saschapo/smartlada/VAZ2106_Smart_Lamp_Context.md

# Умный светильник из заднего фонаря ВАЗ-2106 — контекст проекта

> Хэндофф-документ для будущих сессий. Фиксирует все технические решения, их обоснование и открытые вопросы.
> Формат: **[Ф]** факт · **[В]** вывод · **[Г]** гипотеза/оценка · **[Р]** решение проекта.

## 1. Идея

Из штатного заднего фонаря ВАЗ-2106 сделать домашний умный светильник:
управление голосом через Алису (есть **Яндекс Станция Миди**), мозг — ESP32,
4 секции фонаря диммируются независимо. В кадре снимать НЕ планируется
(строб-эффект от камеры не учитываем; для глаза мерцание убрать всё равно нужно).

## 2. Донор — фонарь ВАЗ-2106

- Деталь: **«фонарь в сборе 2106-3716011»** (левый) / корпус **2106-3716041**.
- **[Ф] Корпус пластиковый, разделён на 5 секций**; рассеиватель цветной, тоже 5 частей:
  1. указатель поворота (жёлтый, крайний наружный),
  2. габарит (красный),
  3. фонарь заднего хода (прозрачный/белый),
  4. стоп-сигнал (красный, крайний внутренний),
  5. подсветка номера (чёрный внутренний выступ).
  Средняя верхняя секция — без лампы.
- **[Р] Используем только 4 секции** (поворот, габарит, задний ход, стоп).
  Подсветку номера НЕ задействуем.
- **[Ф] Поправка к ранней гипотезе:** в 2106 габарит и стоп — РАЗНЫЕ секции с
  отдельными однонитевыми лампами, а НЕ двухнитевая P21/5W «две в одной».
  Значит эффект «габарит тускло / стоп ярко» = просто два независимых PWM-канала
  на две красные секции.
- **[Ф] Задняя часть фонаря штатно ОТКРЫТА** (вставлялся в кузов, лампы — из
  багажника через плату патронов). Поэтому «задняя крышка» = закрыть открытую
  полость по периметру, а не повторять кривую кромку.

## 3. Протокол / интеграция с Алисой

- **[Р] Zigbee, ESP32-C6, прямая привязка к Станции Миди** как несколько
  dimmable-light эндпоинтов (по одному на секцию → каждая = отдельная «лампа»
  в приложении «Дом с Алисой», управляется голосом раздельно).
- **[Ф] Обоснование:** Миди — встроенный Zigbee-координатор; тип «лампа» —
  самый богатый и лучше всего поддерживаемый; работает без сервера, без облака,
  без Wi-Fi-прослойки, без роутера. On/Off + Level Control (яркость) поддержаны.
- **[Ф] Ограничения Яндекса:** нет RGB/сцен для ламп (не нужно — цвет дают
  физические рассеиватели); Zigbee end-device привязывается только к ОДНОМУ
  координатору (Миди ИЛИ Home Assistant, не оба сразу).
- **[Г] Незакрытый риск:** встанет ли самодельное Zigbee-устройство со
  стандартными кластерами (On/Off + Level Control) в Миди «чисто», и приедет ли
  яркость в интерфейс Алисы. Вероятность высокая. ПРОВЕРИТЬ НА ПРОТОТИПЕ ПЕРВЫМ ДЕЛОМ.
- **Отвергнутые альтернативы:**
  - Matter over Wi-Fi — рабочий не-Zigbee вариант (Миди — Matter-коммиссионер,
    работает на ESP32 через esp-matter), но требует живого роутера + риск с
    тестовым сертификатом аттестации (DAC). Отклонён в пользу Zigbee.
  - Wi-Fi + Home Assistant / своё облако / Tuya-эмуляция — больше инфраструктуры.
- **[Ф] Классический ESP32 (WROOM) и ESP8266 Zigbee НЕ умеют** (нет радио 802.15.4).

## 4. Мозг (MCU)

- **[Р] Финал: ESP32-C6** (радио 802.15.4 + Wi-Fi/BLE). Рекомендуемые платы:
  `ESP32-C6-DevKitC-1` (8 МБ flash, удобно для отладки) для прототипа;
  `Seeed XIAO ESP32-C6` (внешняя антенна u.FL) для компактного финала.
- **[Р] Для стартового стенда — имеющийся ESP8266 HW-365A.** Годится ТОЛЬКО для
  bring-up световой части (плата MOSFET + диоды + PWM + плавность диммирования),
  т.к. это не зависит от радио. Zigbee/Алису на нём проверить НЕЛЬЗЯ.
  PWM-API отличается от C6 (`analogWrite` vs `ledcAttach`/`ledcWrite`).
- **[Р] Антенна:** корпус пластиковый (RF проходит — хорошо). НЕ размещать
  фольгу/металлический теплоотвод рядом с антенной C6.

## 5. Силовая часть — плата MOSFET

- **[Р] Выбрана 4-канальная плата на базе D4184 с опторазвязкой (PC817).**
  (Ozon, ~232 ₽, «Четырёхканальный MOSFET-модуль с оптопарной изоляцией».)
- **[Ф] Почему годится от 3.3 В:** затвор смещается от напряжения НАГРУЗКИ через
  оптопару, поэтому 3.3 В на входе открывают ключ так же полно, как 5 В.
  Проблема «logic-level» тут решена схемотехникой. Отменяет идею паять дискретные
  MOSFET-каналы.
- **[Ф] MOSFET:** AOD4184, Rds(on) ~8.5 мОм, 40 В / ~10 А (запас огромный).
- **Распиновка / подключение:**
  - Вход: `PWM1..4` → GPIO МК; `GND1..4` → земля МК.
  - Выход: `Power+ / Power−` → 12 В; диод между `OUTx+` и `OUTx−`
    (анод → `OUTx+`, катод → `OUTx−`; ПРОЗВОНИТЬ, что `OUTx+` = `Power+`).
  - Активный HIGH (duty PWM = яркость, без инверсии).
  - Флайбек-диод не нужен (нагрузка не индуктивная).
- **[Р] Частота PWM: старт ~500 Гц–1 кГц.** Оптопара смазывает фронты на высокой
  частоте. ПРОВЕРИТЬ плавность диммирования, особенно на низкой яркости.
  Заложить гамма-коррекцию (~2.2) при маппинге яркости Алисы 0–100 % в duty.
- **[Ф] Земли сигнала и нагрузки на плате развязаны.** Для реальной развязки —
  МК и 12 В от разных источников, земли не соединять. Общая земля — тоже работает,
  но развязка номинальная.
- **[Г] Fallback:** если плавность PWM разочарует — non-isolated logic-level
  MOSFET (напр. IRLB8721 для прототипа TO-220 / AO3400 SMD для финала),
  4× LEDC → 4× MOSFET напрямую.
- **Отвергнуто:** PCA9685 / I2C-серво-плата (для 4 каналов избыточно; это
  генератор сигнала, не силовой ключ).

## 6. Питание

- **[Р] Рабочее напряжение диодов — 12 В** (5 В давало >2–4 А при мощных диодах;
  6 В нестандартно для PD → отброшено; 9 В рассматривалось, финально 12 В).
- **[Ф] 12 В в USB-PD — опциональный/негарантированный профиль** (стандартные
  фиксированные: 5/9/15/20 В).
- **[Р] Источник 12 В:**
  - Прототип: обычный 12 В adapter (barrel) или лабораторник (исключить PD из
    переменных отладки).
  - Финал: PD-триггер **20 В → buck → 12 В** (надёжно), либо PD-зарядка с
    подтверждённым 12 В в списке PDO.
  - Предохранитель на линии 12 В.
- **[Р] Питание МК:** на стенде — USB от компа; в финале — 12 В → buck 5 В.

## 7. Свет (LED)

- **[Р] Патроны выламываем, ставим свои диоды** (свобода по CRI/оптике/напряжению).
- **[Р] НЕ автомобильные LED-ретрофиты** (низкий CRI, конфликт с внешним PWM).
  Брать сырые модули/COB под прямое управление MOSFET-ом.
- **[Р] CRI важен только под прозрачной секцией заднего хода** (единственный
  «полезный» белый свет) → high-CRI 90+ белый 2700–3000K.
  За цветными секциями (стоп/габарит — красный, поворот — жёлтый) CRI не считается;
  эффективнее ЦВЕТНЫЕ диоды под цвет секции (белый за фильтром теряет ~половину потока).
- **[Р] Топология под 12 В:** строки диодов последовательно + ограничение тока.
  Для старта — модули со ВСТРОЕННЫМ ограничением тока (чтобы PWM-ить прямо
  MOSFET-ом и не спалить). Для мощных сырых LED (>1–2 А) — источник постоянного
  тока (CC-драйвер) на канал, PWM на его enable-вход (шаг 2).
- **[Р] Тепло:** даже LED в закрытом пластиковом корпусе греются — минимальный
  теплоотвод (алюминиевая подложка), особенно под задний ход на полной яркости.

## 8. Корпус / механика

- **[Р] Задняя панель-носитель, печать PETG** (LED холодные, но buck/PD греются;
  PETG надёжнее PLA).
- Панель держит: ESP32-C6, PD/buck, плату MOSFET, ввод питания; диоды — прямо
  в секции корпуса.
- **[Г] CAD:** сложность средняя — обмер периметра открытой полости + корыто со
  стойками; заложить допуск/уплотнитель (не press-fit по месту).

## 9. Итоговая архитектура (сводка)

```
[12 В источник] --Power+/-→ [4-ch D4184 opto MOSFET board]
                                   ↑ PWM1..4 / GND
[ESP32-C6] --4× LEDC (PWM)---------┘
   └─ Zigbee end-device (4× dimmable light) ──radio──→ [Яндекс Станция Миди] → Алиса

Каждый канал: OUTx+ (=12В) → LED-строка секции → OUTx- (ключ на землю)
Секции: 1 поворот(жёлт) · 2 габарит(красн) · 3 задний ход(бел,high-CRI) · 4 стоп(красн)
```

## 10. Открытые вопросы

1. Мощность белого под секцию заднего хода → определит, хватит ли
   токоограниченного модуля или нужен CC-драйвер.
2. Финальный способ получения 12 В (PD 20 В+buck vs 12 В-adapter vs verified-12V PD).
3. Точная плата C6 (DevKitC-1 для отладки → XIAO C6 для финала?).

## 11. Порядок работ (прототип → финал)

1. **[СТЕНД, можно сейчас на ESP8266]** ESP8266 + плата D4184 (1 канал) + 1 диод +
   12 В adapter. Проверить: коммутацию, плавность PWM-диммирования на 500 Гц–1 кГц,
   линейность на низкой яркости. Затем 4 канала.
2. **[РАДИО, на C6]** ESP32-C6 + 1 MOSFET-канал + 1 диод. Поднять Zigbee
   dimmable-light, привязать к Миди, убедиться, что ЯРКОСТЬ реально управляется
   из Алисы. ← снимает главный риск (примет ли Миди самоделку) ДО механики.
3. Полная электроника (4 канала), гамма-коррекция, heartbeat/reconnect-логика.
4. Свет: подбор диодов (high-CRI белый + цветные), теплоотвод.
5. Механика: обмер, CAD задней панели, печать PETG, сборка.

## 12. Профиль исполнителя (для контекста)

Программистский бэкграунд, активный embedded-хоббист (параллельный проект CineInk:
ESP32 + LoRa + e-ink). Работает в Arduino IDE, комментарии/ошибки — простым текстом.
Свободно RU/EN. Ценит формат peer-review: разделение факт/вывод/гипотеза, проверку
логики и скрытых допущений, отсутствие «воды».
