saschapo/smartlada/SmartLadaRevC/DEV_PLAN.md

# SmartLada Rev C — план разработки прошивки

Дата: 2026-09-04. Железо revC поднято и провалидировано (питание PD 12В + buck 3.3В, USB,
OLED, кнопки, I2C, 4 канала — гоняли 35 Вт реальной нагрузки, стабильно, ничего не греется).
LEDC зафиксирован на 10 бит (см. [[esp32c6-ledc-freq-ceiling]]).

Цель: свести в основную прошивку `SmartLadaRevC` сетевое управление (Zigbee + опц. WiFi/веб)
поверх существующего локального (OLED-меню + кнопки), с единой моделью состояния.

## Целевая архитектура

**Единый источник состояния — `config::s`** (mode, master, staticBri[4] + калибровка).
Все «писатели» правят его, луп не меняется:

```
loop: buttons -> menu -> [zigbee/wifi callbacks уже записали config::s]
      fx::compute(mode, now, master, staticBri, out[4])   // компоновщик
      channels::write(now, out)                            // slew -> gamma -> LEDC
      menu::render()
```

Писатели состояния: **меню (кнопки), Zigbee, WiFi/веб.** Приоритет — **last-writer-wins**.
Двусторонняя синхра: изменил меню → репорт в Zigbee-атрибуты (и в веб); пришло из Zigbee/веб →
дёрнуть `menu::render()`. `fx::compute` уже делает компоновку (Static→поканально×master,
анимация→кадр×master), поэтому компоновщик из `RevCZigbeeFx` схлопывается в существующий `fx`.

## Zigbee-модель (архитектура подтверждена, см. research/smartlada_zigbee_effects_plan.md)

Один узел = 5 эндпоинтов (EP = логическое под-устройство; Станция видит их как 5 устройств):

| EP | Тип | Роль |
|----|-----|---|
| 10..13 | `ZigbeeDimmableLight` | 4 лампы (Turn/Marker/Reverse/Stop): on/off + level |
| 14 | `ZigbeeColorDimmableLight` «Fara» | слой эффектов: hue=**селектор эффекта**, level=**яркость эффекта** |

> **Правило приоритета ниже УСТАРЕЛО** (планировалось до реализации, дважды пересмотрено на
> железе). Действующая модель — в `README.md`, раздел «Compositor / control model». Коротко:
> `mode` один определяет слой; EP14 никогда не трогает `staticBri`; выкл и белый на EP14
> значат одно — эффектов нет; групповая и поканальная яркость целиком на EP10-13.
> Блок оставлен как история решения, а не как инструкция.

```
master = Fara.on ? Fara.level/254 : 1.0
Fara.on && насыщенный цвет  -> out[i] = кадр_эффекта[i] * master   (hue -> эффект)
иначе (Fara off/белый)      -> out[i] = лампа[i] * master           (PASSTHROUGH: EP10..13 индивидуально)
```

Готовая реализация всей этой логики (плоская, стендовая) — `sketches/RevCZigbeeFx/RevCZigbeeFx.ino`;
переносим в модуль. Build: `ZigbeeMode=ed, PartitionScheme=zigbee_8MB, FlashSize=16M, CDCOnBoot=cdc`.

## WiFi / веб-интерфейс (оставляем, стретч-цель)

Видение: управление и с телефона (веб), и Zigbee, и кнопками/OLED. Веб — в стиле **cineink**
(`/Users/saschapo/Documents/Documents/arduino/260518_cineink/cineink/`): подключение к WiFi по QR,
`smartlada.local` (mDNS) тоже по QR, тёмный `web_view/` (device.css/index.html/app.js).

**WiFi+Zigbee одновременно на C6:** железо умеет (один 2.4ГГц радиотракт, RF-coexistence /
тайм-слайсинг Wi-Fi6 ↔ 802.15.4). Риск — софт (Arduino: Zigbee-стек + WiFi + веб-сервер + LittleFS
+ OLED одновременно, менее обкатано; возможны потери/латентность). **Стратегия:** WiFi и Zigbee —
независимые модули, которые МОГУТ работать вместе, но с **переключателем в меню (WiFi ↔ Zigbee)** как
гарантированным fallback. Coexistence проверяем эмпирически.

## Решённые вопросы

1. Приоритет при одновременном управлении — **last-writer-wins** по `config::s`.
2. Скорость/яркость эффекта — **параметр меню** (Fara.level = master яркость; скорость — таймингами эффекта в меню).
3. Персист состояния в **NVS** — делаем. NVS в ESP-IDF с wear-leveling, на практике (cineink) не изнашивается;
   писать **с дебаунсом** (на «оседании» значения, не каждый кадр). Глянуть NVS/LittleFS-паттерн cineink.
4. Passthrough (Fara off → индивидуальные лампы) — **оставляем**.

## Железные дельты стенд→продукт (учесть в портировании)

| Стенд (nanoC6) | Продукт revC | Действие |
|---|---|---|
| статус NeoPixel **GPIO8** | **IO8 не разведён** | статус сети на **OLED** |
| factory-reset BOOT(GPIO9) | SW2=IO9 + пункт меню | оба |
| — | **PG=IO10** (12В есть, LOW), **VBUS=IO4** (ADC) | PD-gating (Фаза 4) |

## Фазы

- **Фаза 1 — билд/скелет. СДЕЛАНО.** Zigbee в билд `SmartLadaRevC` (FQBN выше). Проверить, что `config` NVS
  живёт под zigbee-партицией. Вынести Zigbee в `src/net/zigbee.{h,cpp}` (тонкий слой). RF-риск от
  пропущенного EPAD WROOM — проверяем бесплатно при первом паринге (LQI/дальность).
- **Фаза 2 — интеграция состояния. СДЕЛАНО** (report-back EP14 без цвета — см. README). Коллбэки Zigbee → `config::s`; изменения меню → report в Zigbee.
  `fx::compute` как компоновщик. Карта hue→индекс эффекта (общая для hue-коллбэка и пункта «Mode»).
- **Фаза 3 — меню под сеть. ЧАСТИЧНО:** экран Zigbee (статус/PAN/LQI/re-pair) есть,
  WiFi-пункт заглушка, переключателя WiFi<->Zigbee нет. **Планировалось:** Пункты `WiFi`/`WiFi QR` **оставить/доразвить** (провижн по QR, smartlada.local).
  Добавить «Zigbee» (статус joined/PAN/LQI, Pair/Re-pair) и переключатель **WiFi ↔ Zigbee**.
  Статус сети на OLED (вместо NeoPixel). Factory-reset расширить на `Zigbee.factoryReset()`.
- **Фаза 4 — PD-gating + debug-байпас. СДЕЛАНО 2026-09-05.** Гейтинг по **VBUS(IO4 ADC)** с
  гистерезисом (нет ~12В → каналы в 0 + «NO 12V» на idle) — VBUS надёжнее, чем PG, и не «блэкаутит»
  ложно на реальных 12В. Пункт меню **Settings → Force Out (on/off)** — байпас гейтинга для дебага по
  индикаторным LED на 5В без ламп. VBUS/PG/temp видны в Info. (PG=IO10 читается, показывается.)
- **Фаза 5 — эффекты. СДЕЛАНО** (Breathe/Turn/Chase/Fade/Drive). 2-3 стартовых (blink/chase/fade уже есть) на движок `fx::`; hue→эффект.
- **Фаза 6 — WiFi/веб + персист. ЧАСТИЧНО:** NVS-персист с дебаунсом сделан
  (`config::tick`, restore при подаче питания); WiFi и веб-UI отложены сознательно. Веб-UI из cineink (dark view, QR-провижн, mDNS). NVS-персист
  состояния ламп с дебаунсом. Имена/rejoin (T-пункты чеклиста research/).

## Риски

- **RF с пропущенным EPAD WROOM** — держим в голове, проверяем при первом паринге.
- **WiFi+Zigbee coexistence** на C6 под Arduino — главный софт-риск; fallback = переключатель в меню.
- Гетерогенный Zigbee-узел (4×0x0101 + 1×0x0102) — приёмка Станцией (чеклист research/, T3).
- `config` NVS под zigbee-партицией; рост прошивки (16М флеш — запас есть).

## Референсы

- Архитектура Zigbee: `research/smartlada_zigbee_effects_plan.md`, `.../multi_endpoint_summary.md`,
  результаты стенда `research/zigbee_alice_test_results.md`.
- Готовый Zigbee-код: `sketches/RevCZigbeeFx/RevCZigbeeFx.ino` (+ `RevCZigbee4EP` — 4 лампы, вариант A).
- Веб/NVS/лог: cineink `/Users/saschapo/Documents/Documents/arduino/260518_cineink/cineink/`
  (`web_view/`, `firmware/cineink/{web,log,rtc}.cpp`).
- Pin-map ground truth: `README.md`.
