saschapo/smartlada/custom_pcb/smartlada_custom_pcb_kicad.md

# SmartLada C6 — план кастомной платы в KiCad

> **УСТАРЕЛО — исторический документ.** Это первоначальный набросок, написанный до
> начала проектирования. Rev A пошла другим путём: не интеграция модуля
> ESP32-C6-WROOM-1, а **плата-носитель 80 x 65 мм**, к которой девборда подключается
> соплями через 8-контактный J3 (без сокетов и без резерва под неё). Отпали также TVS,
> ESD, ADS1115, NTC и 5 В rail.
>
> Актуальные документы:
> - **[KICAD_WORKFLOW.md](KICAD_WORKFLOW.md)** — точка входа: состояние, что дальше
> - [smartlada_rev_a_bom_netlist.md](smartlada_revA/smartlada_rev_a_bom_netlist.md) — спецификация Rev A
>
> Этот файл сохранён ради раздела 8 (замысел ревизий A/B/C) и списка того, что
> сознательно не делается.

## 1. Назначение платы

Кастомная плата должна заменить связку:

- ESP32-C6 devboard;
- 4-канальный модуль D4184;
- внешнюю разводку питания и управляющих сигналов.

Целевая функция: четыре независимых низковольтных PWM-канала для ламп R10W 12 V, Zigbee, локальная кнопка, индикация и сервисный USB.

Расчетная постоянная нагрузка: около 40 W / 3.33 A при 12 V. Холодный ток ламп кратковременно значительно выше, поэтому силовая часть должна проектироваться по пусковым токам, а не только по номинальным 0.83 A на канал.

---

## 2. Рекомендуемая блок-схема

```text
12 V IN
  ├─ предохранитель
  ├─ защита от переполюсовки
  ├─ TVS (только если питание может быть «грязным»)
  ├─ 12 V BUS ──> 4 × лампа ──> 4 × low-side MOSFET
  └─ DC/DC 12→3.3 V ──> ESP32-C6-WROOM-1
                         ├─ Zigbee
                         ├─ USB-C
                         ├─ BOOT / RESET
                         ├─ status LED / NeoPixel
                         ├─ NTC inputs
                         └─ PWM GPIO0…3
```

---

## 3. Обязательные узлы

### 3.1 ESP32-C6

Использовать модуль **ESP32-C6-WROOM-1**, а не голый чип.

Почему:

- встроены flash, кварц и RF-согласование;
- существенно проще трассировка;
- меньше риск ошибок в первой плате;
- доступны официальные symbol, footprint и 3D-модель Espressif для KiCad.

Выбирать объем flash под фактическую прошивку. Для текущего проекта 16 MB дает запас, но не является обязательным технически.

Обязательные элементы вокруг модуля:

- локальные развязывающие конденсаторы по reference design;
- EN pull-up и RC-цепь reset;
- BOOT-кнопка на GPIO9;
- RESET-кнопка на EN;
- тестовые площадки UART/USB/GND/3V3;
- RF keepout под антенной модуля.

### 3.2 Питание логики

Для стационарного источника 12 V использовать DC/DC-преобразователь **12→3.3 V** минимум на 0.8–1 A пикового тока.

Предпочтительно:

- синхронный buck;
- высокий КПД;
- рабочий вход минимум 16–18 V;
- корректная работа при импульсной нагрузке Wi‑Fi/Zigbee.

Отдельный промежуточный 5 V rail не нужен, если на плате нет 5-вольтовых узлов.

Если USB-C должен одновременно питать и программировать плату, необходимо заранее выбрать архитектуру:

1. USB питает только ESP32 при отключенных 12 V;
2. USB и 12 V объединяются через power mux / ideal-diode OR;
3. USB используется только как data, а плата всегда питается от 12 V.

Для первой ревизии безопаснее вариант 1 или 3. Нельзя напрямую соединять 5 V USB с выходом 3.3-вольтового преобразователя.

### 3.3 USB-C

Нужны:

- разъем USB-C USB 2.0;
- два резистора 5.1 kΩ на CC1/CC2;
- ESD-защита D+/D−;
- трассировка D+/D− как дифференциальной пары;
- при необходимости — последовательные резисторы по reference design Espressif.

USB нужен для прошивки, логов и восстановления устройства. Отдельный USB-UART мост для ESP32-C6 обычно не нужен: можно использовать native USB.

### 3.4 Четыре MOSFET-канала

Вместо модуля D4184 использовать четыре дискретных logic-level N-MOSFET в low-side включении.

Для каждого канала:

- MOSFET с низким RDS(on) при 3.3 V gate drive;
- gate resistor примерно 22–100 Ω;
- gate pulldown примерно 47–100 kΩ;
- широкая силовая дорожка;
- отдельный выход на лампу;
- общий силовой GND;
- контрольная точка затвора;
- запас по току и рассеиваемой мощности.

Лампы накаливания не являются индуктивной нагрузкой, поэтому flyback-диоды не обязательны. Однако посадочное место под TVS или RC-snubber можно предусмотреть как DNP для борьбы с выбросами и EMI.

MOSFET выбирать не только по максимальному току из datasheet. Критичны:

- RDS(on) именно при VGS = 2.5–3.3 V;
- корпус и теплоотвод;
- SOA при холодном пуске лампы;
- реальная температура платы.

### 3.5 Вход 12 V и предохранитель

Обязательны:

- входной разъем с запасом по току;
- общий предохранитель около T4A для текущей нагрузки;
- защита от переполюсовки.

Если плата питается только от регулируемого Ecola B2L080ESB в помещении, автомобильная защита от load dump не обязательна.

Если плата когда-либо будет подключаться к бортовой сети автомобиля, нужно добавить отдельный automotive front-end:

- TVS, рассчитанный на автомобильные импульсы;
- защита от reverse battery;
- фильтр;
- DC/DC с соответствующим входным диапазоном;
- проверка по ISO 7637-2 / ISO 16750.

Это другая категория питания; нельзя считать обычный 12-вольтовый LED-БП эквивалентом автомобильной сети.

---

## 4. Полезные опциональные узлы

### NTC температуры

Добавить два входа:

- NTC силовой части / MOSFET;
- NTC корпуса фонаря или блока питания.

Для каждого:

- NTC 10 kΩ;
- резистивный делитель;
- RC-фильтр;
- ADC-вход;
- разъем или посадочное место для проводного датчика.

Это полезнее, чем цифровые 3-проводные датчики, если требуется просто защита от перегрева.

### Измерение напряжения 12 V

Резистивный делитель на ADC позволяет:

- обнаруживать просадку блока питания;
- логировать аварии;
- отключать анимации при нестабильном питании.

### Измерение тока

Не обязательно для первой платы.

Варианты:

- один общий шунт на весь 12 V BUS;
- четыре отдельных low-side/high-side current sense канала.

Поканальный контроль существенно усложняет силовую землю и разводку. Добавлять его стоит только при реальной задаче диагностики перегоревшей лампы или заклинившего канала.

### Status LED

NeoPixel можно оставить, если он уже участвует в UX.

Если нужен минимализм и надежность, заменить его на:

- один обычный RGB LED;
- либо два одноцветных LED.

NeoPixel добавляет импульсное потребление и программную зависимость, но для одного индикатора это не критично.

---

## 5. Что убрать

Для текущей функции не нужны:

- LiPo charger и аккумулятор;
- RTC;
- SD-карта;
- PSRAM;
- CAN/LIN;
- USB-UART bridge;
- отдельный Wi‑Fi модуль;
- реле;
- flyback-диоды как обязательные компоненты;
- 5 V rail, если его не требуют внешние узлы.

CAN/LIN стоит добавлять только при переходе от автономного светильника к интеграции с автомобилем.

---

## 6. Рекомендуемые разъемы

Минимум:

- 12 V IN: 2 контакта;
- 4 × lamp output;
- общий lamp +12 V либо общий силовой разъем;
- 2 × NTC;
- USB-C;
- SWD/JTAG/UART test pads;
- BOOT/RESET;
- опциональный сервисный I²C header.

Для ламп предпочтительны разъемы с фиксацией и реальным токовым рейтингом, а не Dupont.

---

## 7. Размещение и трассировка в KiCad

Разделить плату на зоны:

```text
[RF antenna]
[ESP32 + USB + buttons]
[DC/DC]
[MOSFET 0][MOSFET 1][MOSFET 2][MOSFET 3]
[12 V / lamp connectors]
```

Правила:

- антенна ESP32 у края платы;
- под антенной — keepout без меди и компонентов;
- силовые токи ламп не должны проходить через землю ESP32;
- соединить силовую и логическую землю низкоимпедансно, но контролировать пути возвратного тока;
- DC/DC держать дальше от антенны;
- MOSFET и силовые разъемы располагать близко;
- использовать полигоны для 12 V и GND;
- предусмотреть тепловые переходные отверстия под MOSFET;
- D+/D− вести коротко и симметрично;
- добавить test points на 12V, 3V3, GND и все PWM.

---

## 8. Ревизии платы

### Rev A — функциональная

- ESP32-C6-WROOM-1;
- 4 MOSFET;
- 12→3.3 V;
- USB-C;
- BOOT/RESET;
- status LED;
- общий предохранитель;
- NTC footprints;
- крупные test points.

Цель: заменить devboard и D4184 без добавления новых функций.

### Rev B — диагностическая

- измерение 12 V;
- температура;
- общий current sense;
- улучшенная EMC;
- разъемы финального корпуса.

### Rev C — автомобильная, только если нужна

- automotive input protection;
- CAN/LIN;
- квалифицированный DC/DC;
- диагностика ламп;
- проверка по автомобильным импульсным тестам.

---

## 9. Главный принцип

Первая кастомная плата должна повторять уже проверенную функциональность, а не одновременно вводить Zigbee, новые датчики, автомобильную защиту, новый корпус и сложную диагностику.

Для SmartLada рациональная первая цель: **одна плата вместо ESP32-C6 devboard + D4184, с теми же GPIO и тем же поведением прошивки**.
