saschapo/smartlada/custom_pcb/smartlada_revC/SESSION_HANDOFF.md

# SmartLada Rev C — Session Handoff (2026-08-15)

> **СТАТУС на 2026-08-17: PCB и компоненты ЗАКАЗАНЫ.** Платы — DDAYA (AliExpress) $14.99/5шт,
> order 5551293542950288. Компоненты — Платан заказ №771612 (оплачен 4284₽). Docs: закупка
> `smartlada_revC_procurement.csv` + `platan_import_revC.txt`; сборочный пакет `fab/*_ddaya.xlsx`.
> **Следующий фокус — ПРОШИВКА (PD-gating): см. `../../SmartLadaRevC/CODE_HANDOFF.md`.**
> Всё ниже — история PCB-работы (задачи закрыты).

Передача состояния для новой сессии. Всё ниже — проверенные факты этой сессии.

## Что это
Продуктовая плата контроллера ламп фонаря ВАЗ. Ветка от revB (интегр. ESP32-C6-WROOM-1),
минус дисплей-на-плате, плюс механика под установку в фонарь. **Схема ГОТОВА, PCB РАЗВЕДЕНА.**

## Файлы
- Спека: `smartlada_rev_c_spec.md` · BOM: `smartlada_rev_c_bom.md`
- Board setup: `board_setup.md` · Ревью схемы: `smartlada_revC_schematic_review.md`
- KiCad-проект: `smartlada_revC/` (sym-lib-table + fp-lib-table + libs `../libs/Vendor.pretty`)
- Механика: `smartlada_revC/mechanical/` (PDF-чертёж + STEP крепёжной пластины)
- CH224K datasheet: `https://www.platan.ru/pdf/datasheets/wch/CH224D-K-221K.pdf`

## Архитектура (финал)
- **MCU:** ESP32-C6-WROOM-1-N16 (модуль, закуплен, 5 шт).
- **Питание: USB-C PD, профиль 12В/3А** через **CH224K** (ESSOP-10, 12В-триггер). Лампы 12В
  НАПРЯМУЮ (без понижайки). Рекоменд. БП COMMO Core 45-140Вт (в инструкцию: «в один порт»,
  у 45Вт при двух портах 12В падает до 1.67А).
- **CH224K обвязка:** CFG1=24k→GND (=12В), CFG2/3=NC, **DP/DM отвязаны от D+/D- и закорочены
  между собой** (чистый PD, QC не используем), VBUS(8) через R21-последоват., VDD(1) через
  R19 1k + 1uF. **PG — open-drain, active-LOW.**
- **Детект «зарядка vs компьютер»:** firmware включает каналы только при **«PG=LOW И нет
  USB-хоста»** (защита от 30Вт из ноутбука). Дефолт каналов OFF.
- **VBUS-sense:** делитель 100k/33k → ADC ESP.
- **Buck:** TPS54202 12→3.3В. FB-делитель = **R4/R5** (стоит вплотную к U2, ~4.5мм ✓).
  EN плавающий (наследие revB, работает через внутр. pull-up).
- **4 канала ламп:** AOD4184A (DPAK), low-side, gate 100R + pulldown 100k на PGND.
  **Нагрузка 2×10Вт + 2×5Вт = 30Вт** (под бюджет PD).
- **ESD:** USBLC6-2SC6 на D+/D-. **VBUS-пин U4 → +3V3, НЕ 12В** (5-вольтовая деталь!).
- **Индикация:** 6× красных LED 0805 (4 канала + 12В + 3.3В).
- **Выходы ламп:** Faston 6.3мм «папа» TE 63951-1 (футпринт `TE_1217754-1`), ×5 (4 OUT + 1
  общий +12В). «Мама» под обжим на провода — заказать.
- **Дисплей:** SSD1315 + 4 кнопки, вынос кабелем → **J4** (I2C + KEY1-4 + 3V3/GND, 8-pin,
  угловой pin header; кабель BLS-8 Platan 10660).
- **UART debug:** J8 (TX/RX/GND).
- **C_bulk 470мкФ/25В** на 12В rail. **Тест-точки** GND/12V/3V3/PG.
- **Убрано:** барел, предохранитель, TVS, переполюсовка (Q5), выключатель — защита входа
  делегирована PD-источнику. RGB, датчики — тоже убраны.

## Механика
- Плата **100×59 мм**, 4× крепёжных Ø3.2 (клиренс M3), прямоугольник **88×47**, NPTH.
- Зазор над крепёжной пластиной 2мм (back-side пропай/via). Faston и антенна WROOM торчат
  за край (намеренно, out-of-bounds warnings исключены).

## PCB статус
- **2 слоя** (F.Cu сигналы + B.Cu GND-полигон). Саша перешёл с 4 на 2 слоя.
  (Моя рекомендация была 4 ради RF/buck; на 2 работает, если земля под D+/D-/buck/антенной
  сплошная.)
- **DRC чистый, КРОМЕ 66× `footprint_symbol_field_mismatch` (поле Platan)** — это ШУМ от
  впаянного поля Platan (символы имеют, футпринты нет). **Фикс:** Update PCB from Schematic
  с галкой **«Update footprint fields from symbols»**, ИЛИ Board Setup → Violation Severity →
  `footprint_symbol_field_mismatch` = Ignore.
- GND-разрывы (намеренные, короткие): +12В для LED в зоне ламп (там B-полигон убран),
  CC1/CC2 по B, +3V3 на U4 и на J4. **B.Cu GND под лампами убран** (не пускать шум в землю).
- USB D+/D-: длины ~43.8мм согласованы (для FS не обязательно). ПРОВЕРИТЬ: сплошная B.Cu
  земля под парой (нет щелей поперёк).
- **PGND↔GND: звезда через NT1** (SMD net-tie). D6 (индик. LED) переведён на GND (был PGND).

## Нумерация R/C — ПЕРЕНУМЕРОВАНА Сашей (инкрементально по блокам)
НЕ использовать старую карту. Buck FB = R4/R5. VBUS-делитель = R7(100k)/R8(33k). Проверять
по актуальному нетлисту.

## Переименование
**LAMP0..3 → OUT0..3** (Саша, для читаемости шелкографии).

## Firmware pin-map — ИЗМЕНЁН при разводке (перепроверить в схеме!)
- **CH2 ↔ CH3 поменяны** (U1 пины 26/27, IO2/IO3). Финальную карту OUT↔IO сверить в схеме.
- **CH224_PG → IO10** (было IO5).
- **VBUS-sense ADC → IO4.**
- **USB D+/D- → IO13/IO12** (native USB).
- **I2C → IO18/IO19; KEY1-4 → IO20-23; UART TX/RX → GPIO16/17** (J8 пины 2/3 переставлены —
  сверить silk TX/RX с нетами!).
- **BOOT → IO9; RESET → EN.**
- База revB-remap: IO0=CH1(OUT1), IO1=CH0(OUT0). После свопа CH2/CH3 — сверить.

## Открытые задачи (для следующей сессии)
1. ~~Убрать 66 Platan-warning~~ **DONE (2026-08-15):** severity `footprint_symbol_field_mismatch`=Ignore
   в `.kicad_pro`. DRC 0/0/0.
2. ~~Самопроверка B.Cu-земля под D+/D-~~ **DONE:** пара вся по F.Cu, земля сплошная, стежок-via есть.
   Мелкая CC-щель у разъёма — ок для FS. Подробно: `smartlada_revC_verification.md`.
3. ~~Silk J8 TX/RX~~ **DONE:** pad1=GND, pad2=RX(/UART_RX), pad3=TX(/UART_TX) — совпадает.
4. ~~Антенна WROOM~~ **DONE:** keepout за краем платы (x>230), меди под антенной нет.
5. Прошивка: **ФОРК + PIN-REMAP DONE (2026-08-15).** `SmartLadaRevC/` (форк SmartLadaRevB):
   каналы `{1,0,2,3}` (OUT0=IO1,OUT1=IO0,OUT2=IO2,OUT3=IO3), кнопки `{23,22,21,20}` (KEY1..4),
   I2C 18/19 без изменений; version.h -> revC. **Собирается** (arduino-cli, esp32c6, CDCOnBoot=cdc,
   27% flash). **ОТЛОЖЕНО:** PD-gating (PG=IO10, VBUS-sense=IO4, USB-host detect, «каналы ON
   только при безопасном питании») — отдельным заходом. Ещё не проверено на железе.
6. Косметика silk (Саша исключил из проверки).
7. ~~Gerber/fab~~ **DONE (2026-08-15):** пакет `smartlada_revC_fab_20260815.zip` (Gerber X2 +
   Excellon PTH/NPTH + job + `fab/README_FAB.md`). Готов к загрузке на pselectro.
   **ОТКРЫТО при оформлении заказа:** толщина 1.5 (board_setup) vs 1.6 (kicad_pcb) — выбрать 1.6.
   BOM/закупка — Саша сверяет цены (в т.ч. AliExpress).

## Верификация питания/связей (2026-08-15) — все критичные узлы сошлись
CFG1=24k(12В) · Buck 3.30В (R5=100k/R4=22k) · U4 VBUS на +3V3 · CH224 DP/DM закорочены и отвязаны
от данных · PG→IO10 · EN RC-reset · +12V: J1 VBUS×4→buck+C11 470µF+Faston J7. См. verification.md.

## Инфра-заметки
- **Platan API:** `shop.platan.ru` отключён (403); работает `www.platan.ru`. Скилл
  `platan-parts` пропатчен на www.platan.ru + браузерный UA.
- Метод работы: Саша сам в KiCad, ассистент разбирает файлы (kicad-cli нетлист/BOM/DRC,
  разбор питоном) и сверяет со скриншотами. Не редактировать .kicad_sch, когда KiCad открыт
  (правки затираются при сохранении).
