saschapo/smartlada/SmartLadaRevC/codex_reviews/REPORT.md

# Ревью SmartLadaRevC 1.0.6-revC

Дата: 2026-09-06. Проверено текущее содержимое рабочей папки, включая незакоммиченные изменения. Код и документы проекта не изменены, устройство не прошивалось. Это настольный светильник на базе автомобильного фонаря; требования автомобильной эксплуатации к нему не применялись.

**Результат:** два приоритетных дефекта, несколько ошибок на переходах состояний и существенное расхождение документации с реализацией. Обычные сценарии могут работать стабильно, несмотря на эти находки.

## Объём и метод

Прочитаны все 25 исходных и документальных файлов SmartLadaRevC: основной скетч, все модули и заголовки, шрифты, README, DEV_PLAN, оба handoff. 13 файлов build — сгенерированные артефакты: изучены параметры сборки, разделы флеш-памяти, конфигурация SDK; прочитаны байты и зафиксированы хеши всего набора. Двоичные файлы не рассматриваются как дополнительный исходный код.

Дополнительно использованы материалы из родительской папки: общие документы проекта, спецификация и верификация Rev C, журнал тестирования с Алисой, ТЗ Drive из SmartLadaC6, клиент tools/ble_ota.py. Старые документы про ESP8266, LED, другие GPIO и другой блок питания не приняты за требования текущей Rev C.

Проверена установленная библиотека Arduino-ESP32 **3.3.10**, особенно реальные реализации Zigbee setters/callbacks и блокировок. Это позволило не приписать прошивке отсутствующую проблему «все setters вызываются без Zigbee lock»: внутри setClusterAttribute блокировка есть.

Сборка с FQBN из README завершилась успешно:

- Прошивка: **1 111 526 байт**, 32% доступного раздела приложения.
- Глобальные переменные: **40 416 байт**, 12% учитываемой сборщиком RAM. Это не измерение пикового потребления памяти во время работы BLE/Zigbee.
- Сборка выполнена в /tmp/smartlada-revc-review-build.

Для воспроизведения логики собран временный C++ стенд: он включает реальные config.cpp, effects.cpp, channels.cpp, buttons.cpp и menu.cpp; периферия, часы и Preferences заменены имитацией. AddressSanitizer/UndefinedBehaviorSanitizer обнаружили два варианта недопустимого обращения к памяти. Это проверка кода на компьютере, не запуск ESP32 и не проверка радиоканала или силовой части.

## Находки

### 1. P1 — смена эффекта из Алисы во время редактирования Timings повреждает работу меню

**Подтверждено воспроизведением с диагностикой памяти.**

Место: [menu.cpp:650](</Users/saschapo/Documents/Claude/Projects/VAZ smart light/SmartLadaRevC/src/ui/menu.cpp:650>), особенно обращение к параметру в строке 664; [notifyExternalChange:822](</Users/saschapo/Documents/Claude/Projects/VAZ smart light/SmartLadaRevC/src/ui/menu.cpp:822>).

Сценарий: выбрать Chase, открыть Timings, включить редактирование Fade. Не закрывая редактор, через Алису выбрать Drive либо Turn.

Режим уже новый, но editing и cursor остались от Chase. Для Drive массив params равен nullptr. Для Turn cursor=1 указывает за пределы единственного параметра: проверка cursor >= nItems пропускает его, потому что nItems включает строку Reset To Defaults.

Результаты стенда:

- Chase → Drive: `reference binding to null pointer`, затем аварийное чтение.
- Chase → Turn: `global-buffer-overflow` при чтении параметра.

При следующем UP/DOWN возможна также запись за пределы массива. На ESP32 ожидаемы сбой/перезагрузка либо повреждение состояния; точную реакцию конкретной сборки на плате не проверял.

**Направление исправления:** при внешней смене режима завершать редактирование и перепроверять курсор относительно nparams; получать согласованный снимок режима на обработку экрана. Проверять индекс непосредственно перед доступом к params. Ограничения только по числу строк меню недостаточно.

### 2. P1 — плавный старт учитывает время, когда лампы ещё вообще не разгонялись

**Ошибка расчёта подтверждена; электрические последствия требуют проверки на плате.**

Место: [channels.cpp:47](</Users/saschapo/Documents/Claude/Projects/VAZ smart light/SmartLadaRevC/src/channels/channels.cpp:47>), [channels.cpp:57](</Users/saschapo/Documents/Claude/Projects/VAZ smart light/SmartLadaRevC/src/channels/channels.cpp:57>), [SmartLadaRevC.ino:65](</Users/saschapo/Documents/Claude/Projects/VAZ smart light/SmartLadaRevC/SmartLadaRevC.ino:65>).

s_lastMs устанавливается в channels::begin. Затем идут OLED, NVS, эффекты и запуск Zigbee. Перед первым channels::write меняется только коэффициент softMs, но отсчёт времени не сбрасывается. Первый dt включает всю инициализацию. В установленной библиотеке Zigbee.begin ожидает старт стека; это не вызов с гарантированно нулевой задержкой, хотя дальнейшее присоединение к сети идёт в фоне.

Контролируемый пример: между begin и первым write прошло 2000 мс, целевой уровень 255, BOOT_SOFT_MS=1500. Первый write сразу выдаёт логический уровень 187.78 и **PWM 578/1023 ≈ 56.5%** при штатной калибровке. До этого PWM был нулевой. Чем дольше инициализация, тем ближе первый шаг к полной мощности.

Это не измерение фактического времени запуска платы. Это воспроизводимый контрпример к гарантии плавного старта. Приоритет высокий из-за уже описанной в журнале чувствительности общего питания к резкому включению холодных ламп.

**Направление исправления:** отдельный старт рампы с актуальным временем и нулевым выходным состоянием; не учитывать время ожидания до её начала. Отдельно проверить возврат 12 В после завершения setup: сейчас повторная загрузочная рампа там не запускается.

Дополнительно, 1500 мс теперь означает τ экспоненты, а не время достижения заданного уровня. Из идеального нуля за одну τ достигается около 63% логического уровня, затем прошивка переключает τ на обычный. Фразы «0→target за 1.5 с» требуют корректировки.

### 3. P2 — защитное отключение питания проходит через пользовательское плавное затухание

**Подтверждено воспроизведением PWM-логики.**

Место: [SmartLadaRevC.ino:115](</Users/saschapo/Documents/Claude/Projects/VAZ smart light/SmartLadaRevC/SmartLadaRevC.ino:115>), [channels.cpp:64](</Users/saschapo/Documents/Claude/Projects/VAZ smart light/SmartLadaRevC/src/channels/channels.cpp:64>).

При потере разрешённого напряжения код обнуляет целевые out[], но реальный PWM остаётся в s_actual и плавно уменьшается. Таким образом, «NO 12V → каналы 0» верно лишь для цели, а не для выходов.

Пример с допустимым значением Soft Start=3000 мс: через одну секунду после запрета при исходном полном выходе PWM всё ещё **549/1023 ≈ 53.7%**. Это не процент мощности лампы при изменившемся напряжении; это доля времени открытого ключа.

**Направление исправления:** отдельное немедленное отключение PWM со сбросом s_actual при срабатывании защиты; пользовательское сглаживание применять к обычным изменениям яркости. Возобновление питания — самостоятельный сценарий плавного включения.

### 4. P2 — удержание подтверждения может тут же вывести устройство из BLE OTA

**Поведение кнопок воспроизведено; связь с конкретным случаем из handoff — гипотеза.**

Место: [menu.cpp:778](</Users/saschapo/Documents/Claude/Projects/VAZ smart light/SmartLadaRevC/src/ui/menu.cpp:778>), [buttons.cpp:25](</Users/saschapo/Documents/Claude/Projects/VAZ smart light/SmartLadaRevC/src/input/buttons.cpp:25>), [SmartLadaRevC.ino:97](</Users/saschapo/Documents/Claude/Projects/VAZ smart light/SmartLadaRevC/SmartLadaRevC.ino:97>).

Пользователь подтверждает Yes и удерживает кнопку до окончания перезагрузки. buttons::begin считает все кнопки отпущенными, поэтому спустя debounce физически удерживаемая SEL формирует новое pressed(SEL). OTA-loop трактует любую такую кнопку как команду немедленной перезагрузки в обычный режим.

Стенд подтвердил событие pressed(SEL) через 26 мс после первого наблюдения удерживаемой кнопки. Это возможное объяснение записи «вход из меню не сработал». Доказательств, что именно так происходило на плате пользователя, нет.

**Направление исправления:** при входе в OTA сначала дождаться отпускания всех кнопок, после этого разрешать выход новым нажатием.

### 5. P2 — защита от собственного Zigbee-эха может отбросить настоящую команду Алисы

**Подтверждается допустимой последовательностью выполнения кода; частота проявления на радио неизвестна.**

Место: [zigbee.cpp:76](</Users/saschapo/Documents/Claude/Projects/VAZ smart light/SmartLadaRevC/src/net/zigbee.cpp:76>), [zigbee.cpp:139](</Users/saschapo/Documents/Claude/Projects/VAZ smart light/SmartLadaRevC/src/net/zigbee.cpp:139>).

s_reporting глобален для обеих задач. Пока основной цикл репортит состояние, onFaraHsv игнорирует все вызовы, не различая собственный callback и внешнюю команду.

Возможная последовательность: loop ставит s_reporting=true и ждёт Zigbee-lock внутри setter; задача Zigbee обрабатывает входящую команду и вызывает onFaraHsv; тот немедленно возвращается из-за флага. Внутреннее состояние библиотечного endpoint уже обновилось, а config::s — нет. Команда потеряна.

Комментарий «однобайтовые поля атомарны, поэтому гонка безвредна» неверен как общее обоснование: атомарное чтение байта не делает согласованными несколько полей и операции read-modify-write над lampOn.

**Направление исправления:** один владелец прикладного состояния с очередью команд; либо согласованная синхронизация и распознавание эха по контексту вызова. Одного volatile недостаточно. Нельзя просто ставить произвольный общий mutex вокруг существующих callbacks/setters: сначала определить порядок блокировок, чтобы не получить взаимное ожидание.

### 6. P2 — прерывание BLE OTA не согласовано с задачей записи

**Подтверждён конфликт владения ресурсом; сбой при конкретном обрыве связи не воспроизводился на ESP32.**

Место: [bleota.cpp:49](</Users/saschapo/Documents/Claude/Projects/VAZ smart light/SmartLadaRevC/src/net/bleota.cpp:49>), [bleota.cpp:78](</Users/saschapo/Documents/Claude/Projects/VAZ smart light/SmartLadaRevC/src/net/bleota.cpp:78>), [bleota.cpp:91](</Users/saschapo/Documents/Claude/Projects/VAZ smart light/SmartLadaRevC/src/net/bleota.cpp:91>).

writerTask использует s_handle для esp_ota_write. Одновременно callback отключения или ABORT вызывает esp_ota_abort для того же handle без ожидания завершения записи. Смена s_receiving не отменяет уже начатый esp_ota_write. START также допускается во время активного сеанса и заменяет общие handle/состояние.

По [документации Espressif](https://docs.espressif.com/projects/esp-idf/en/latest/esp32c6/api-reference/system/ota.html), esp_ota_abort освобождает handle и связанные ресурсы. Возможны обращение к освобождённому состоянию, ошибка записи или сбой повторной попытки. Из этого не следует, что основной образ неизбежно повреждается: запись направлена в неактивный OTA-раздел.

**Направление исправления:** передать START, DATA, FINISH, ABORT и disconnect одному владельцу OTA-сеанса; callback должен запрашивать отмену, а задача записи подтверждать её после завершения текущей операции. Запретить второй START до завершения/отмены первого.

Смежные пробелы: результат xStreamBufferSend не проверяется; размер из START служит только для прогресса, равенство recv==total перед FINISH не проверяется. esp_ota_end всё же валидирует образ, поэтому утверждать «любая обрезанная прошивка будет принята» неверно. Нужна обработка потерь данных как явной ошибки протокола.

### 7. P2 — команды Алисы сами по себе не сохраняются после перезапуска

**Подтверждено по всем местам сохранения и стендом с имитацией Preferences. Это известный незавершённый пункт плана, а не обязательно новая регрессия.**

Место: [zigbee.cpp:75](</Users/saschapo/Documents/Claude/Projects/VAZ smart light/SmartLadaRevC/src/net/zigbee.cpp:75>), [menu.cpp:814](</Users/saschapo/Documents/Claude/Projects/VAZ smart light/SmartLadaRevC/src/ui/menu.cpp:814>), [config.cpp:26](</Users/saschapo/Documents/Claude/Projects/VAZ smart light/SmartLadaRevC/src/config/config.cpp:26>).

Zigbee меняет config::s и s_dirty; notifyExternalChange только перерисовывает экран. Ни сохранения, ни постановки pendingSave в этом пути нет. Пишет NVS меню.

Сценарий: сохранить локально включённые лампы, выключить через Алису, перезапустить. Возвращается локально сохранённое включённое состояние. Напротив, последующая правка даже настройки дисплея сохранит всю config::s вместе с сетевым состоянием. Персист оказывается зависим от несвязанного локального действия.

**Направление исправления:** явная политика восстановления питания и общий отложенный персист для нужных полей независимо от источника команды. Не писать NVS прямо из каждого сетевого callback.

### 8. P2 — переход в Static не отражается полностью в состоянии Fara

**Подтверждено по прошивке и setters установленной библиотеки; конкретное отображение плитки Алисы не проверялось.**

Место: [zigbee.cpp:150](</Users/saschapo/Documents/Claude/Projects/VAZ smart light/SmartLadaRevC/src/net/zigbee.cpp:150>), [zigbee.cpp:155](</Users/saschapo/Documents/Claude/Projects/VAZ smart light/SmartLadaRevC/src/net/zigbee.cpp:155>).

После эффекта EP14 получает On=true и насыщенный цвет. При локальном выборе Static репорт меняет только Level. Старые On=true и цвет остаются внутри Fara и в соответствующих атрибутах. При следующем изменении Level библиотека передаст callback старые state/hue/sat, и onFaraHsv снова выберет цветовой эффект.

В комментарии описан осознанный обход ошибки Алисы с белым цветом. Обход имеет цену: состояние текущего режима уже не полностью синхронизировано. Поэтому формулировка handoff «report-back полностью» чрезмерна.

**Направление исправления:** определить однозначное представление Static в EP14 и поведение следующей команды яркости. Например, выключать именно endpoint эффектов при локальном выходе из эффекта; отдельно сохранить согласованное представление белого статического мастера. Решение требует проверки с Алисой, чтобы не вернуть зафиксированный баг белого цвета.

### 9. P3 — меню Chase допускает значения Fade, которые фактически не применяются

**Подтверждено непосредственно алгоритмом.**

Место: [effects.cpp:44](</Users/saschapo/Documents/Claude/Projects/VAZ smart light/SmartLadaRevC/src/fx/effects.cpp:44>).

При Step=400 мс пользователь может установить Fade=4000 мс, однако renderer ограничивает каждую рампу половиной Step, то есть 200 мс. Значения Fade от 200 до 4000 мс дают одну и ту же форму. Экран и NVS при этом сохраняют введённые 4.0 с.

**Направление исправления:** динамически ограничивать Fade значением Step/2 либо показывать фактическое ограничение. Дополнительно, fmtParam выводит только десятые секунды при шаге 50 мс — некоторые нажатия меняют параметр без изменения показанного числа.

## Алгоритмы и документация

- **DEV_PLAN описывает отвергнутую модель.** Там Static умножается на master и Fara названа питанием фары. Текущий код Static на master не умножает; Fara off завершает эффект и возвращает статическую картинку. Если руководствоваться планом при следующей правке, легко вернуть уже исправленное двойное диммирование.
- **README и handoff расходятся по статусу.** README относит report-back и PD-gating к будущему. В коде оба есть, но с ограничениями выше. Проверки со статусом TODO в тест-журнале соседствуют с утверждениями «полностью» и «всё протестировано»: по документам нельзя восстановить, какая проверка выполнена на какой версии.
- **Комментарии от предыдущих реализаций:** в .ino старый порядок каналов и «PD gating not implemented»; в bleota.h и клиенте — BLE одновременно с Zigbee; в config.h master общий для Static и эффектов, параметры эффектов ещё TODO. В действительности BLE работает отдельным загрузочным режимом, параметры уже сохраняются, а калибровка gamma/min/max/softMs общая для всех каналов, несмотря на выражение per-channel gamma в README.
- **Drive соответствует таблицам прежнего ТЗ, но формулировки гарантий сильнее графа.** REVERSE действительно имеет единственный вход из STOP. Однако STOP также достижим из HAZARD и REVERSE и является стартовым состоянием, поэтому «STOP только после торможения» буквально неверно. Запрет самопереходов означает отсутствие повторения одного состояния подряд; он не означает неповторяющийся сценарий: циклы CRUISE→BRAKE→CRUISE разрешены.
- **Некоторые решения Drive — художественные условности.** REVERSE→CRUISE возможен без промежуточного STOP; в REVERSE постоянно горит стоп, габарит поднимается до 100%. Это прямо соответствует существующему ТЗ. Не считаю их ошибками реализации. Если нужна реалистичность движения, надо сначала уточнить правила сценария.
- **Предел гарантии питания нужно описать точно.** present12V проверяет пороги 7/8 В. Это различение низкого питания и допустимого по этой политике, а не измерительное подтверждение именно 12 В. Старые требования аппаратной спеки о запрете ламп при обнаруженном USB-host и верхнем пороге напряжения сейчас не реализованы. Их статус нужно явно определить; автоматическое возвращение старых требований без согласования не предлагается.
- **Успешный boot-тест не доказывает универсального устранения причины.** Он подтверждает работоспособность проверенного сочетания ламп, источника, настроек и времени запуска. Из этого не следует, что аппаратные меры при любых источниках больше не нужны. Особенно с учётом найденного первого шага рампы.

## Что проверено без найденных возражений

- Компоновщик Static: 16 384 проверки выходов для всех 256 значений master и 16 масок lampOn прошли. Выход зависит от staticBri и разрешения канала; повторного масштабирования master нет.
- Turn включает только канал поворотника. Игнорирование статической маски в эффектах согласуется с принятой моделью v2; это не восстановленный баг B1.
- Соответствие функций GPIO0..3 актуальной верификации платы, с перекрещенными OUT0/OUT1, подтверждается документами. Старый комментарий .ino не означает, что массив GPIO в текущем channels.cpp неверен.
- Разделы app0/app1 реально присутствуют и достаточно велики для собранного приложения. Старое предположение журнала о single-app разделе не соответствует текущему partitions.csv.
- Шрифты содержат по 95 ASCII-глифов. По их метрикам строки Update Over BLE в System и Reverse рядом с баром помещаются; фактическое изображение OLED на плате не проверялось.
- Отсутствие отдельного контроля температуры ламп не названо регрессией: в актуальных аппаратных решениях датчики сознательно исключены, temperatureRead описан как диагностика кристалла. Этот обзор не сертифицирует тепловую безопасность корпуса.

## Приоритет следующей работы

Сначала исправить недопустимые обращения к параметрам и отсчёт загрузочной рампы. Затем отделить защитное отключение от анимационного сглаживания, исправить удержанную кнопку OTA и владение состоянием между задачами. Персист и точную семантику EP14 оформить как явные правила продукта.

После исправлений нужны целевые проверки на плате: смена эффектов при открытом редакторе; PWM первого включения при разных задержках запуска; потеря и возврат питания; вход OTA с удержанием SEL; обрыв BLE на разных стадиях и повторный START; выключение Алисой с последующим ребутом; Effect→локальный Static→EP14 Level. Опасный сценарий меню лучше сначала проверять без силовой нагрузки.

Файлы временного стенда и хеши находятся в /tmp/smartlada-review (временные файлы могут быть удалены системой). Никаких исправлений по результатам ревью не внесено.
