saschapo/smartlada/custom_pcb/pselectro_tech_limits.md

# ЭЛЕКТРОконнект / pselectro.ru — технологические возможности (справочник)

Извлечено из `datasheets/electroconnect_tech_limits.pdf` (стр. «Технологические
возможности изготовления печатных плат», ООО «ЭЛЕКТРОконнект», Новосибирск,
order@pselectro.ru). Приёмка по IPC-A-600, ГОСТ Р 53429-2009, ГОСТ 23752-79.

Две колонки: **Стандарт** (штатный техпроцесс, без наценки/согласования) и
**Предел** (абсолютная возможность, обычно дороже/по согласованию/выше отбраковка).
**Проектируем по «Стандарту».** Буквы (A, B, C…) — обозначения на чертеже завода.

---

## Сводка под НАШУ плату (revB: 4 слоя, 35 µm/1oz, 1.5 мм, контур скрайбом)

| Параметр | Значение (Стандарт) | Источник |
|---|---|---|
| Min ширина проводника (35 µm) | **0.175 мм** | топология |
| Min зазор проводник/площадка (35 µm) | **0.175 мм** | топология |
| Min зазор полигон→площадка/проводник (35 µm) | **0.200 мм** | H |
| Min металлизированное отверстие (PTH/via) | **0.30 мм** | B |
| Отношение отв:толщина | до **1:7** (при ≤2.5 мм) → min 0.21 при 1.5 мм | B |
| Min поясок PTH (annular, 35 µm) | **0.200 мм** (предел 0.150) | C |
| Min поясок внутр. слоя | 0.200 (предел 0.100) | D |
| Отступ топологии от края PTH | **0.250 мм** | G |
| **Медь→край при СКРАЙБЕ, 1.5 мм** | **0.500 мм** (внешн. и внутр.) | I/U |
| Медь→край при фрезеровке (внешн. / внутр.) | 0.250 / 0.400 | I / U |
| Min расстояние между краями отверстий | 0.200 мм | Z |
| Min маска: ширина полоски | **0.150 мм** | R |
| Min зазор проводник→край маски | 0.100 мм | S |
| Min зазор площадка→край маски | 0.050 мм | Q |
| Маркировка: высота символа | **1.0 мм** (предел 0.8) | W |
| Маркировка: ширина линии | **0.150 мм** (предел 0.1) | V |
| Маркировка→паяемая площадка | 0.200 мм | X |
| Толщина маски | 0.01–0.02 мм | — |
| Финиш HASL (ПОС-63) | ОК (не применяется на платах < 1 мм) | — |

**Важно для нас:**
- **Чёрная (цветная) маска:** переходные отверстия **⌀ ≤ 0.4 мм рекомендуется закрывать
  маской (tenting)**. У нас маска чёрная и via 0.3 → тентим (в KiCad tenting front/back = yes).
- Наши via 0.6/0.3 давали поясок 0.15 = **предел**, не стандарт. Под «Стандарт» нужен поясок
  **0.20** → via **0.7/0.3** (или силовые 0.8/0.4 = 0.20).
- Контур скрайбим → медь-край **0.5 мм** (совпало с текущей настройкой).

---

## Полные таблицы (Стандарт / Предел)

### Размеры плат, мм
| Параметр | Стандарт | Предел |
|---|---|---|
| Max размер 1-/2-сторонней | 430×300 | 575×455 |
| Max размер МПП | 450×350 | 550×450 |
| Допуск на положение контура | ±0.200 | |
| Допуск на размеры платы | 0..−0.25 | 0..−0.2 |
| Min толщина платы | 0.500 | 0.100 |
| Max число слоёв | 6 | 28 |
| Max толщина платы | 3.0 | 3.5 |

### Топология по толщине фольги (мм)
| Фольга | Min проводник (Ст/Пр) | Min зазор (Ст/Пр) | Полигон→пад/пров H (Ст/Пр) |
|---|---|---|---|
| 12 µm | 0.100 / ≤0.075 | 0.100 / ≤0.075 | 0.200 / 0.150 |
| 18 µm | 0.125 / ≤0.100 | 0.125 / ≤0.100 | 0.200 / 0.150 |
| **35 µm** | **0.175 / ≤0.150** | **0.175 / ≤0.150** | **0.200 / 0.175** |
| 50 µm | 0.270 | 0.270 | 0.270 |
| 70 µm | 0.300 | 0.300 | 0.300 |
| 105 µm | 0.350 | 0.350 | 0.350 |

Сетчатый полигон (линия/зазор), 35 µm: 0.250/0.275 (предел 0.225/0.225).

### Металлизированные отверстия, мм
| | Параметр | Стандарт | Предел |
|---|---|---|---|
| B | Min PTH | 0.30 | 0.200 |
| B | отв:толщина | 1:7 (≤2.5мм) | 1:10 (≤2мм) |
| | Max PTH | 4.5 | не огр. |
| C | Min поясок PTH 12µm | 0.125 | ≤0.075 |
| C | ...18µm | 0.150 | ≤0.125 |
| C | **...35/50µm** | **0.200** | **≤0.150** |
| C | ...70/105µm | 0.250 | 0.200 |
| D | Min поясок внутр. слоя | 0.200 | 0.100 |
| M | Слепые via | 0.200–0.500 | |
| T | Глухие via | ⌀=глубина+0.100 | |
| G | Отступ топологии от края PTH | 0.250 | 0.200 |
| Y | Металлизированное полуотверстие | 0.600–5.000 | 0.400 |

### Неметаллизированные отверстия (NPTH), мм
| | Параметр | Стандарт | Предел |
|---|---|---|---|
| F | NPTH→топология | 0.200 | 0.200 |
| Z | между краями отверстий | 0.200 | 0.200 |
| K | Min поясок NPTH | 0.300 | 0.200 |
| E | Max NPTH тентированием | 3.5 | 3.5 |
| J | NPTH→край платы | 0.300 | 0.250 |

Слотовое сверло: 0.6, 0.7, 0.8, 1.0, 1.2, 1.5, 1.8, 2.0. Длина паза 2–10 ⌀.

### Контур: фрезеровка / скрайб (отступ топологии от края), мм
| | Стандарт | Предел |
|---|---|---|
| Фрезеровка, внешние (I) | 0.250 | 0.200 |
| Фрезеровка, внутр. МПП (U) | 0.400 | 0.400 |
| NPTH→край (фрезеровка, J) | 0.250 | 0.250 |

Скрайбирование по толщине платы (внешние I и внутренние U одинаково):
| 0.5 мм | 1.0 мм | **1.5 мм** | 2.0 мм |
|---|---|---|---|
| 0.350 | 0.400 | **0.500** | 0.700 |

### Паяльная маска LPI, мм
| | Параметр | Стандарт | Предел |
|---|---|---|---|
| R | Min ширина полоски маски | 0.150 | 0.100 |
| S | проводник→край маски | 0.100 | 0.05 |
| Q | площадка→край маски | 0.05 | 0.025 |
| | Толщина маски | 0.01–0.02 | |
| | Цвет | зелёный | чёрный, белый, красный, синий |

**Цветная (не зелёная) маска: via ⌀ ≤ 0.4 мм рекомендуется закрывать маской.**

### Маркировка (шелкография), мм
| | Параметр | Стандарт | Предел |
|---|---|---|---|
| V | Min ширина линии | 0.150 | 0.100 |
| W | Min высота символа | 1.0 | 0.8 |
| X | маркировка→паяемая площадка | 0.200 | |
| | Цвет | белый | чёрный |

### Финиш и контроль
- Финиш: HASL (ПОС-63; **не тоньше 1 мм**), иммерсионное золото (ENIG), иммерсионное олово.
- Электроконтроль (flying probe): min площадка 0.2, min толщина 0.5.
- Контроль импеданса: допуск **±10%** (заказывается отдельно; мы не заказываем).
- Заполнение отверстий компаундом: ⌀ 0.2–0.6, min толщина платы 0.5.
