saschapo/smartlada/custom_pcb/smartlada_revB/smartlada_rev_b_pinout.md

# SmartLada Rev B — распиновка разъёмов и GPIO-карта

Снято с разведённой платы (2026-07-24, parity схема=PCB = 0). **Источник истины — плата.**
При разводке часть GPIO переназначена (чтобы не пересекались дорожки) — см. пометки ⚠.
Связанные доки: [спека §9](smartlada_rev_b_spec.md), полная карта там же.

---

## Разъёмы

### J1 — POWER INPUT (клеммник 5.0 мм, 2 pos)
| Pin | Сигнал | Примечание |
|----|---|---|
| 1 | +12V_IN | вход 12 В (через F1 -> +12V_FUSED -> Q5 реверс) |
| 2 | PGND | силовая земля (возврат ламп 3.33 А) |

### J2 — LAMPS_OUT (клеммник 2.54 мм, 5 pos)
Low-side ключи: лампа между `+12V` (COM) и `LAMPx`; GPIO открывает MOSFET.
| Pin | Сигнал | Ключ | Управляющий GPIO |
|----|---|---|---|
| 1 | +12V (COM) | — | питание ламп (общий +) |
| 2 | LAMP0 | Q1 | **IO1** ⚠ (было IO0) |
| 3 | LAMP1 | Q2 | **IO0** ⚠ (было IO1) |
| 4 | LAMP2 | Q3 | **IO3** ⚠ (было IO2) |
| 5 | LAMP3 | Q4 | **IO2** ⚠ (было IO3) |

### J3 — USB Type-B (USB-B1HSB6) — **DATA ONLY**
VBUS НЕ заведён (плата всегда питается от 12 В). Нативный USB-Serial-JTAG ESP32-C6.
| Pin | Сигнал | GPIO | Примечание |
|----|---|---|---|
| 1 (VCC) | — | — | не подключён (VBUS не используется) |
| 2 (D−) | USB_D− | IO12 | пара, не трогать |
| 3 (D+) | USB_D+ | IO13 | пара, не трогать |
| 4 (GND) | GND | — | + экран (P1/P2) на GND |

Цепь: J3 → U3 (USBLC6 ESD) → R5/R6 (0R серия) → U1. R5/R6 = placeholder-перемычки.

### J4 — OLED_AND_BUTTONS (гребёнка 2.54 мм, 8 pin)
I2C-дисплей SSD1315 (3.3 В) + 4 кнопки (active-low, внутр. pull-up).
| Pin | Метка на плате | GPIO | Функция |
|----|---|---|---|
| 1 | GND | — | земля |
| 2 | +3V3 | — | питание |
| 3 | SCL | IO18 | I2C clock |
| 4 | I2C_SDA | IO19 | I2C data |
| 5 | KEY4 | IO20 ⚠ | кнопка (active-low) |
| 6 | KEY3 | IO21 ⚠ | кнопка |
| 7 | KEY2 | IO22 ⚠ | кнопка |
| 8 | KEY1 | IO23 ⚠ | кнопка |

⚠ Порядок кнопок реверснут: **KEY1=IO23 … KEY4=IO20** (в исходном черновике был KEY1=IO20).

### J5 — SERVICE_PINS (гребёнка 2.54 мм, 8 pin)
Сервисные GPIO + UART. Метки `SVC_IOxx` **буквально равны** `GPIOxx`.
| Pin | Метка на плате | GPIO | Функция |
|----|---|---|---|
| 1 | SVC_IO11 | IO11 | свободный GPIO |
| 2 | SVC_IO10 | IO10 | свободный GPIO |
| 3 | SVC_IO7 | IO7 | свободный GPIO |
| 4 | SVC_IO6 | IO6 | свободный GPIO |
| 5 | GND | — | земля |
| 6 | +3V3 | — | питание |
| 7 | UART_RX | IO17 | U0RXD (лог/консоль) |
| 8 | UART_TX | IO16 | U0TXD |

---

## Полная GPIO-карта ESP32-C6 (по плате)

| GPIO | Нет / функция | Куда | Примечание |
|---|---|---|---|
| IO0 | CH1_IN | LAMP1 (Q2) | ⚠ своп |
| IO1 | CH0_IN | LAMP0 (Q1) | ⚠ своп |
| IO2 | CH3_IN | LAMP3 (Q4) | ⚠ своп |
| IO3 | CH2_IN | LAMP2 (Q3) | ⚠ своп |
| IO4 | — | — | свободен (пад U1.4, не разведён) |
| IO5 | — | — | свободен (пад U1.5) |
| IO6 | SVC_IO6 | J5.4 | |
| IO7 | SVC_IO7 | J5.3 | |
| IO8 | WS2812_DIN | LED1 | strapping (idle ok), 10k pull-up |
| IO9 | BOOT | SW2 | strapping, внутр. pull-up |
| IO10 | SVC_IO10 | J5.2 | |
| IO11 | SVC_IO11 | J5.1 | |
| IO12 | USB_D− | J3.2 | нативный USB |
| IO13 | USB_D+ | J3.3 | нативный USB |
| IO15 | — | — | свободен (пад U1.23), strapping |
| IO16 | UART_TX | J5.8 | U0TXD |
| IO17 | UART_RX | J5.7 | U0RXD |
| IO18 | I2C_SCL | J4.3, OLED | |
| IO19 | I2C_SDA | J4.4, OLED | |
| IO20 | KEY4 | J4.5 | ⚠ реверс |
| IO21 | KEY3 | J4.6 | ⚠ реверс |
| IO22 | KEY2 | J4.7 | ⚠ реверс |
| IO23 | KEY1 | J4.8 | ⚠ реверс |
| EN | RESET | SW1 | RC 10k/1µF + кнопка |

**Свободные для доп. нужд:** IO4, IO5, IO15 (на паде U1, соплёй). IO15 — strapping, осторожно.
**Занятые полностью:** остальные (лампы, USB, I2C, UART, кнопки, WS2812, BOOT).

---

## Для firmware — что учесть (иначе поедет)

- **Лампы:** `LAMP0=IO1, LAMP1=IO0, LAMP2=IO3, LAMP3=IO2` (НЕ прямое IO0..3).
- **Кнопки:** `KEY1=IO23, KEY2=IO22, KEY3=IO21, KEY4=IO20`, active-low + debounce.
- UART-консоль доступна на J5 (IO16/17); плюс нативный USB-Serial-JTAG через J3.
