saschapo/smartlada/custom_pcb/smartlada_revB/smartlada_rev_b_spec.md

# SmartLada Rev B — плата с интегрированным ESP32-C6-WROOM-1 (4 слоя)

Учебная эволюция [revA](smartlada_rev_a_bom_netlist.md). Rev A была **носителем**
для готовой девборды nanoESP32-C6 (модуль на летящих проводах через J3). Rev B
**интегрирует модуль ESP32-C6-WROOM-1-N16 прямо на плату** и добавляет USB Type-B для
прошивки, RGB-индикатор и разъём под съёмный OLED-модуль с кнопками.

Главная учебная цель — **четырёхслойная плата**: сплошная опорная земля, разделение
силового и цифрового доменов, дифпара USB с контролируемым импедансом, RF keepout под
антенной. Всё это невозможно на двух слоях и есть смысл 4-слойки.

Питание и нагрузка — как в revA: **12 В / 80 Вт**, 4 лампы R10W BA15S (0.83 А/канал,
3.33 А суммарно). **Каналы ламп при разводке переназначены** (LAMP0=IO1, LAMP1=IO0,
LAMP2=IO3, LAMP3=IO2 — см. §9), поэтому **firmware-ядро требует правки маппинга каналов**;
плюс добавляется периферия (OLED, кнопки, RGB, сервисные/UART GPIO).

**Статус: спека (Stage 1-2). Схема и плата ещё не нарисованы.**

---

## 1. Что делает Rev B и чем отличается от Rev A

| Блок | Rev A | Rev B | Почему изменилось |
|---|:-----:|:-----:|---|
| ESP32 | девборда на J3 (летящие провода) | **модуль WROOM-1-N16 на плате** | цель revB — интеграция, USB-C требует всего обвеса ESP |
| Прошивка/логи | USB-C на девборде | **USB Type-B на нашей плате** (native USB C6) | своя точка прошивки; Type-B надёжнее SMD USB-C |
| Питание 3V3 | AMS1117 на девборде | **buck 12V->3.3V напрямую** | 5 В никто не потребляет; USB только данные |
| Слои | 2 | **4** (Sig / GND / Pwr / Sig) | опорная плоскость, домены, дифпара USB, RF |
| RGB | WS2812 на девборде | **свой WS2812B на плате** | у WROOM-1 нет встроенного LED |
| Кнопки | BOOT на девборде | **BOOT + RESET на плате** + 4 кнопки на OLED-модуле | модулю нужны свои кнопки прошивки |
| Дисплей/HMI | нет | **8-pin гребёнка** под съёмный OLED SSD1315 + 4 кнопки | сервис/настройка на месте |
| Датчики | нет (revA убрал ADS/NTC) | **сервисная гребёнка** 3V3+GND+GPIO | вынос под будущие датчики, без распайки на плате |
| Силовой блок | 4x MOSFET + reverse + buck | **тот же, без изменений** | доказан на revA, переносим 1:1 |
| I2C | выкинут в revA | **вернулся** (для OLED) | нужен дисплею; подтяжки ставим свои |
| Габарит | 80x65 | **92x80 (факт)** | ориентир был 100x100; фактический Edge.Cuts вышел 92x80 |

**Сознательно НЕ добавляем** (держим объём умеренным, чтобы довести до конца): токовые
шунты, монитор 12 В, NTC, USB-UART мост (CH343/CP2102 — не нужен, у C6 нативный USB),
LDO и промежуточный рельс 5 В (не нужны — см. §2), схему авто-прошивки на 2 транзисторах
(нативный USB сбрасывает чип сам), снабберы, TVS.

---

## 2. Архитектура питания

**Одна понижайка 12V -> 3.3V, и всё.** На плате нет ни одного потребителя 5 В (модуль,
WS2812, OLED — все на 3.3 В), поэтому промежуточный рельс 5 В и LDO не нужны. USB несёт
**только данные**; питание всегда от 12 В (12 В на стенде есть всегда). Это убирает из
revB LDO, оба Шоттки-OR и весь узел выбора источника: меньше тепла (buck ~85% против LDO,
который рассеивал бы ~0.65 Вт) и на ~6 позиций меньше деталей.

```text
J1 12V --[F1 T4A]--[Q5 AOD4185 reverse]--+--> +12V bus --> LAMP_COM (J2.1)     3.33 A
                                          |
                                          +--> U2 TPS54202 buck (3.3 V) --> +3V3
                                                                              |
                                                        модуль(pin2), WS2812, OLED, подтяжки

USB-C: только D+/D-, CC, ESD -- НЕ питает плату (VBUS не заведён на питание)
```

**Почему USB без питания корректно.** Нативный USB C6 (USB-Serial-JTAG) работает от 3.3 В
самой платы. Пока подано 12 В — ESP запитан, USB поднимается и шьётся авто-сбросом; роль
USB как у отладчика (данные есть, питание своё). Без 12 В плата не работает — это принятое
ограничение (12 В при заливке есть всегда). `VBUS` разъёма оставляем не подключённым (при
желании — делитель на свободный GPIO как «USB подключён», опционально, по умолчанию нет).

**Buck на 3.3 В (перенос из revA, новый делитель FB).** TPS54202, Vref 0.596 В:
`Vout = Vref x (1 + R2/R3)`. **R2 = 100k / R3 = 22k (1%) -> Vout = 3.30 В** типовое
(3.22-3.39 В по разбросу Vref — в окне модуля 3.0-3.6 В, подстройка не нужна). L1 = 10 µH
shielded >=2 А, Cin = 2x10 µF/50 В (1210), Cboot = 100 нФ, Cout = 2x22 µF/16 В. EN
плавающий (внутр. pull-up включает; no-connect flag). Питаем RF-модуль **напрямую с
понижайки**, поэтому SW-нода малой площади и подальше от антенны (§12), а декаплинг у
модуля (22µF + 0.1µF) обязателен.

**Бюджет тока `+3V3`.** Пик модуля (datasheet Table 13): **WiFi TX 802.11b — 382 мА**.
Плюс WS2812B (~60 мА) и OLED (~20 мА). Пик ~0.45-0.5 А. Buck (2 А) — с большим запасом.

---

## 3. Стек-ап 4 слоя и стратегия земли

```text
L1  Signal + компоненты        35µm/1oz  <- сигналы, силовая медь, USB microstrip
L2  GND  (сплошная плоскость)  35µm/1oz  <- тихая опора для ВСЕЙ цифры/USB/RF
L3  Power (+3V3 полигон)       35µm/1oz  <- единый +3V3 (5В нет), часть трасс
L4  Signal + 12V силовая медь  35µm/1oz  <- обратный ток силового блока, доразводка
```

**Типовой конструктив pselectro (с сайта, подтверждён):**
`Типовой/4/1,5/35/FR/вн 0.71 (35/35)`. Полная раскладка сверху вниз, суммарно **1.57 мм**:

| Слой | Материал | Толщина, мм |
|---|---|---|
| Фольга L1 (F.Cu) | медь 35 µm / 1 oz | 0.035 |
| Препрег | 7628 | 0.18 |
| Препрег | 7628 | 0.18 |
| вн. слой (core + меди L2/L3) | кор 0.71 + медь 35/35 | 0.78 |
| Препрег | 7628 | 0.18 |
| Препрег | 7628 | 0.18 |
| Фольга L4 (B.Cu) | медь 35 µm / 1 oz | 0.035 |
| **Итого** | | **1.57** |

Ключевое: **зазор L1–L2 = 2 листа препрега 7628 = 0.36 мм** (не 0.32), фольга **35 µm
(1 oz) на всех 4 слоях** (внутренние тоже 35/35, не 0.5 oz), внутренний кор 0.71 мм. 1.5 мм
из ранних черновиков — прикидка; настоящий типовой = **1.57 мм** (строго 1.5 — нестандартный
набор препрега/кора, может стоить дороже). Зазор L1–L2 = 0.36 мм задаёт геометрию USB-дифпары
(§6, §14): под 90 Ω трассы шире, чем при тонком препреге — считать в KiCad PCB Calculator.

**Фактически введено в KiCad (Board Setup -> Physical Stackup):** F.Cu 0.035 / prepreg 0.36
(FR4, εr 4.5) / In1.Cu 0.035 / core 0.71 (FR4, εr 4.5) / In2.Cu 0.035 / prepreg 0.36 /
B.Cu 0.035; маски по 0.01. Board thickness в KiCad = **1.59 мм** (= 1.57 конструктив +
2×0.01 маска; завод считает толщину 1.57 без маски).

### 3.1 Силовой ток 3.33 А НЕ идёт сквозь плоскость L2

Разбор вопроса «можно ли закапывать 3.33 А в 0.5 oz L2»:

- **Термически плоскость справилась бы:** по стеку pselectro внутренние слои **1 oz**
  (35 µm, ~0.5 mΩ/квадрат). 3.33 А через ~5 квадратов растекания = ~2.5 mΩ, падение
  ~8 мВ, ~30 мВт на большой площади — нагрев ничтожен (даже на 0.5 oz был бы).
- **Но реальные проблемы не в нагреве:** (1) токовые узкие места у переходных отверстий —
  чтобы 3.33 А с внешних пятачков истоков MOSFET попал в L2 и вернулся, нужно много via
  (одно 0.3 мм via ~1-2 А), ток крадётся у отверстий; (2) **шум по опорной плоскости** —
  возврат ламп это коммутируемые 30 кГц импульсы 3.33 А; пропусти их через ту же
  плоскость, что служит опорой для USB/RF/цифры, и IR-падение появится как помеха на
  опорной земле (тот же урок, что revA про землю J3).
- Плюс внутренний слой «замурован» в FR4 и хуже отводит тепло; IPC-2221 берёт для
  внутренних вдвое меньший коэффициент.

**Решение:** возврат силовой земли `PGND` (до 3.33 А) — **широкой медью по внешним
L1/L4** локально в силовом углу, как в revA. `L2` — тихая опорная плоскость, несёт
только цифровой возврат. `PGND` и тихая `GND` сходятся в **одной точке** у J1.

### 3.2 Разделение доменов

- **Силовой угол** (вход 12 В, F1, Q5, buck U2, Q1..Q4, клеммники J1/J2) — в один край
  платы. Его земля/питание — внешними слоями.
- **Цифровой/RF угол** (модуль, USB-C, LDO, WS2812, OLED-гребёнка) — в противоположный,
  антенна на кромке. Под ним сплошная L2 GND даёт короткий возврат каждому сигналу.
- **Единая точка стыка** силовой и тихой земли — у входного J1 (звезда).
- **Плоскости под антенной вырезаны на всех 4 слоях** (§5) — иначе медь под антенной её
  расстраивает. На 2-слойке чистят top+bottom; на 4-слойке ОБЯЗАТЕЛЬНО ещё L2 и L3.

---

## 4. ESP32-C6-WROOM-1-N16 — интеграция

### 4.1 Модуль

| Параметр | Значение (datasheet v0.6) |
|---|---|
| Тип | ESP32-C6-WROOM-1-N16, 16 MB flash, **PCB-антенна** |
| Габарит | **18.0 x 25.5 x 3.2 мм**, 29 pin (28 castellated + EPAD) |
| Питание | **3.0-3.6 В** (RF нормируется при 3.3 В) |
| EN | не оставлять плавающим; RC-задержка R=10k, C=1µF (datasheet §7) |
| EPAD (pin 29) | на GND, массив thermal via в L2 (улучшает теплоотвод) |

**Закупка:** на **Platan модуля НЕТ** (0 позиций). Брать в ЧипДип / Космодром /
AliExpress. Это единственная позиция BOM вне обычного канала — заложить срок.

### 4.2 Пиновка модуля -> нет платы

Из datasheet Table 3 (pin no. -> имя). USB на IO12/IO13, strapping — IO4/IO5/IO8/IO9/IO15.

| Pin | Имя | Нет revB | Примечание |
|----:|-----|---|---|
| 1, 28, 29 | GND, GND, EPAD | `GND` | EPAD на via-массив |
| 2 | 3V3 | `+3V3` | декаплинг 22µF + 0.1µF рядом с пином |
| 3 | EN | `EN` | RC 10k/1µF + кнопка RESET |
| 8 | IO0 | `CH0_IN` | PWM stop (не strapping) |
| 9 | IO1 | `CH1_IN` | PWM reverse |
| 27 | IO2 | `CH2_IN` | PWM turn |
| 26 | IO3 | `CH3_IN` | PWM marker |
| 10 | IO8 | `WS2812_DIN` | **strapping** (boot mode); см. 4.6 |
| 15 | IO9 | `BOOT` | **strapping**, внутр. pull-up; кнопка BOOT на GND |
| 13 | IO12 | `USB_D-` | нативный USB, НЕ использовать как GPIO |
| 14 | IO13 | `USB_D+` | нативный USB |
| 16 | IO18 | `I2C_SCL` | OLED |
| 17 | IO19 | `I2C_SDA` | OLED |
| 18 | IO20 | `KEY1` | кнопка модуля K1 |
| 19 | IO21 | `KEY2` | K2 |
| 20 | IO22 | `KEY3` | K3 |
| 21 | IO23 | `KEY4` | K4 |
| 6 | IO6 | `SVC_IO6` | сервисная гребёнка (ADC1_CH6, LP_I2C_SDA) |
| 7 | IO7 | `SVC_IO7` | сервисная гребёнка (LP_I2C_SCL) |
| 11 | IO10 | `SVC_IO10` | сервисная гребёнка |
| 12 | IO11 | `SVC_IO11` | сервисная гребёнка |
| 25 | TXD0 (GPIO16) | `UART_TX` | сервисный UART (лог/отладка) |
| 24 | RXD0 (GPIO17) | `UART_RX` | сервисный UART |
| 4, 5, 23 | IO4, IO5, IO15 | — | **strapping, оставить не подключёнными** |
| 22 | NC | — | нет вывода |

### 4.3 EN / RESET

`EN` <- R (10k) на `+3V3`, C (1µF) на `GND` (datasheet §7, RC-задержка старта). Кнопка
`RESET` (SW1) замыкает `EN` на `GND`. **Не оставлять EN плавающим.**

### 4.4 BOOT

`IO9` имеет внутренний слабый pull-up (default = 1, boot из flash). Кнопка `BOOT` (SW2)
замыкает `IO9` на `GND` -> download mode. Внешний 10k на `+3V3` опционален (усиливает
дефолт), можно не ставить — как на девборде.

### 4.5 Нативный USB — почему без CH343 и без транзисторов авто-прошивки

У ESP32-C6 есть встроенный **USB Serial/JTAG контроллер** (IO12/IO13). Он:
- даёт прошивку и лог **без внешнего USB-UART моста** (минус CH343/CP2102 и его питание);
- **сам сбрасывает чип в download** по команде esptool — классическая схема авто-сброса
  на 2 транзисторах (DTR/RTS -> EN/IO9) **не нужна**.

Кнопки `BOOT`+`RESET` остаются как ручной fallback (нужны в любом случае). Это осознанное
упрощение: меньше деталей, при этом переспрошивка идёт авто-сбросом по нативному USB.

### 4.6 Декаплинг и strapping-оговорка

- `+3V3` у pin 2: **22 µF + 0.1 µF** вплотную (datasheet §7).
- `IO8` — strapping (boot mode) и одновременно линия данных WS2812. Ставим **10k pull-up
  (R11) на +3V3** (populate): гарантирует IO8=1 при загрузке (нормальный boot из flash).
  WS2812 DIN — вход с высоким импедансом; подтяжка держит линию high только пока GPIO в
  Z (boot/reset), в работе GPIO сам управляет линией. Связка проверена на nanoESP32-C6.

---

## 5. RF — антенна и keepout

WROOM-1 (PCB-антенна) имеет **keepout-зону** у торца с антенной (у 1U-версии её нет).

Правила размещения (datasheet §8.2, Espressif HW guidelines):

1. **Модуль — на кромке платы**, антенным торцом наружу. Keepout-зона антенны совпадает
   с краем платы (лучше — слегка выступает / заподлицо).
2. **Под keepout-зоной НЕТ меди на всех 4 слоях**: ни трасс, ни полигонов, ни земли —
   L1, **L2 (GND!)**, **L3 (Power!)**, L4. Плоскости L2/L3 вырезать под антенной.
3. Никаких компонентов и via в keepout.
4. Металлические/высокие детали (электролит C1, держатель F1) — подальше от антенны.
5. Земляное «ограждение» из via по периметру модуля (кроме антенного торца) сшивает
   L1 и L2 под модулем.

Keepout-зона **увеличена в футпринте с запасом**; антенна смотрит на кромку платы,
компоненты и медь в зону не попадают by design. Точные размеры — из футпринта (Figure 10
datasheet, «Antenna Area»); свериться визуально при размещении.

---

## 6. USB-интерфейс (Type-B)

Разъём — **USB 2.0 Type-B**, розетка THT right-angle (не USB-C). Выбран за механическую
надёжность: сквозной монтаж, крупный корпус с ключом — для стенда/учебной платы прочнее
хрупкого SMD USB-C. Обратная сторона — нет реверсивности и CC (Type-B их не имеет), зато
на 2 резистора меньше.

| Ref | Номинал / PN | Назначение |
|-----|---|---|
| J3 | USB Type-B THT right-angle. **Platan 249636968**, футпринт TE **292304-5** (SnapEDA) | разъём прошивки/лога |
| U3 | USBLC6-2SC6 (SOT-23-6) | ESD-защита D+/D- |
| R5, R6 | 0R (место под 22R) | серия в D+/D-; у C6 обычно 0R |

Пиновка Type-B (стандарт): Pin1 `VBUS`, Pin2 `USB_D-`, Pin3 `USB_D+`, Pin4 `GND`.
Экранные лапки корпуса — в **PTH на GND** (экран + механика).

- `VBUS` (Pin1) — **не заведён на питание** (Option A). Оставить NC (опц. делитель на
  свободный GPIO как «USB подключён»).
- CC-резисторов нет — Type-B не USB-C.

**Дифпара `USB_D+/USB_D-`:**
- 90 Ω дифф. **microstrip над сплошной L2 GND**, опора непрерывна под парой (без
  разрезов/трасс в L2 под ней);
- вести парой вплотную, коротко (модуль близко к разъёму), length matching; ESD U3 у
  разъёма, до модуля;
- Full-Speed 12 Мбит/с к импедансу терпим; строгий «controlled impedance» не заказываем;
- зазор L1-L2 по стеку pselectro ~0.32 мм -> под 90 Ω трассы шире: ориентир
  `W ~= 0.4 мм`, `S ~= 0.25 мм`, финально в KiCad Impedance calc (h=0.32, er~4.3).

**Сверить в футпринте 292304-5 (метод: координаты + скриншот):** отверстия контактов
~0.9-1.0 мм (Pin holes 0.92 мм по TE), крепёжные ~2.3 мм под экранные лапки (PTH, на GND),
шаг контактов 2.5/2.71 мм, габарит ~12.0 x 15.7 мм. Ключевые размеры TE-чертежа и
Platan-детали совпадают (крепёж 12.0/12.04, solder tail 10.28, шаг 2.5/2.71).

---

## 7. Периферия

### 7.1 RGB-индикатор

| Ref | PN | Notes |
|-----|-----|---|
| LED1 | **WS2812B-V5** (в наличии на Platan, 14₽) | 1 шт, статус-индикатор, на `IO8` |
| R7 | 300-470R | серия в `WS2812_DIN` |
| C11 | 100 нФ | декаплинг у LED |

Питание LED — от `+3V3` (как встроенный на девборде). При VDD=3.3 В порог Vih WS2812
= 2.31 В, логика 3.3 В подходит. (Если запитать LED от 5 В — Vih=3.5 В > 3.3 В, было бы
маргинально; поэтому именно 3.3 В.)

### 7.2 Гребёнка OLED + кнопки (J4)

Съёмный модуль «0.96" SSD1315 128x64 I2C + 4 кнопки». Разъём — **8-pin гребёнка «мама»
2.54 мм**, пинаут в порядке модуля:

| Pin J4 | Сигнал модуля | Нет платы |
|---:|---|---|
| 1 | GND | `GND` |
| 2 | VCC | `+3V3` (подтверждено: питание 3.3 В) |
| 3 | SCL | `I2C_SCL` (`IO18`) |
| 4 | SDA | `I2C_SDA` (`IO19`) |
| 5 | K4 | `KEY4` (`IO23`) |
| 6 | K3 | `KEY3` (`IO22`) |
| 7 | K2 | `KEY2` (`IO21`) |
| 8 | K1 | `KEY1` (`IO20`) |

- **I2C-подтяжки:** R8, R9 = **4.7k на `+3V3`** на SCL/SDA. revA отмечал: в системе
  нет подтяжек нигде. Ставим свои; если на модуле они тоже есть — параллель ~2.35k
  допустима.
- **Кнопки K1-K4:** на модуле замыкаются на GND (active-low). На стороне C6 — вход с
  внутренним pull-up, читаем 0 при нажатии. Внешние подтяжки не нужны.
- Разъём — у кромки, чтобы модуль/дисплей не наезжал на высокие детали.

### 7.3 Сервисная гребёнка под датчики (J5)

**6-pin гребёнка «папа» 2.54 мм**, вынос питания и свободных GPIO (вместо распайки
датчика на плате):

| Pin J5 | Нет | Примечание |
|---:|-----|---|
| 1 | `+3V3` | питание датчиков |
| 2 | `GND` | — |
| 3 | `SVC_IO6` | ADC1_CH6 / LP_I2C_SDA |
| 4 | `SVC_IO7` | LP_I2C_SCL |
| 5 | `SVC_IO10` | GPIO |
| 6 | `SVC_IO11` | GPIO |

Заложить **опциональное посадочное место 4.7k** на одну линию (напр. `SVC_IO6`) на
`+3V3` — под будущий 1-Wire DS18B20 (см. открытый вопрос [[ds18b20-defective-batch]]:
корень -127 не найден, подозрение на подтяжку). Не распаивать по умолчанию.

---

## 8. Силовой блок — перенос из Rev A без изменений

Вход, reverse-protection, buck и 4 ключа берутся из revA 1:1 — доказаны, DRC 0/0/0.
Полное обоснование (ориентация Q5, направление body-diode, gate pull-down у затвора,
FB после L1, слаботочный fuse, ширины под 3.33 А) — в
[smartlada_rev_a_bom_netlist.md](smartlada_rev_a_bom_netlist.md) §3, §5, §6.

| Блок | Компоненты | Ключевое правило |
|---|---|---|
| Вход 12 В | J1 (клемма 5.0 мм), F1 (T4A slow-blow), C1 (100µF/25В), C2 (100нФ) | slow-blow обязателен: пусковой ток нити ~8-10 А |
| Reverse | Q5 AOD4185 (P-ch, TO-252), R1 100k (gate pull-down) | **drain к входу +12 В, source к плате**. Топологию пересматривали (2026-07-22): P-ch оставлен как оптимум; low-side N-ch исключён — земля USB его шунтирует |
| Buck | U2 TPS54202, L1 10µH, C3/C4 10µF, C5 100нФ, C6/C7 22µF, R2 100k, R3 **22k** (3.3 В) | вход. петля <2 мм; FB после L1; SW-медь малой |
| Ключи x4 | Q1..Q4 AOD4184A (TO-252), Rg 100R, Rpd 100k, TP_G0..3 | **Rpd у затвора** — держит лампы off в окне сброса |
| Выход ламп | J2 (клемма 5-pos 2.54 мм): COM +12В, CH0..3- | 3.33 А COM |

---

## 9. GPIO-карта ESP32-C6 (сводно)

**АКТУАЛЬНО по разведённой плате (2026-07-24).** При разводке часть GPIO переназначена,
чтобы не пересекались дорожки — карта ниже снята с платы (parity схема=PCB = 0). Пометки
«(было IOx)» — расхождение с исходным черновиком; **firmware обязан использовать новую карту.**

```text
-- Лампы, PWM low-side (J2) -- ПЕРЕНАЗНАЧЕНЫ (пары свопнуты) --
IO1   CH0_IN  -> LAMP0     (было IO0)
IO0   CH1_IN  -> LAMP1     (было IO1)
IO3   CH2_IN  -> LAMP2     (было IO2)
IO2   CH3_IN  -> LAMP3     (было IO3)
-- Периферия на плате --
IO8   WS2812_DIN  (strapping, idle ok)
IO9   BOOT        (strapping, внутр. pull-up; кнопка SW2)
IO12  USB_D-      (нативный USB, не трогать)
IO13  USB_D+      (нативный USB, не трогать)
IO16  UART_TX  U0TXD  -> J5.8 (лог/сервис)
IO17  UART_RX  U0RXD  -> J5.7
IO18  I2C_SCL  -> OLED, J4.3
IO19  I2C_SDA  -> OLED, J4.4
-- Кнопки OLED-модуля (J4) -- ПЕРЕНАЗНАЧЕНЫ (реверс порядка) --
IO23  KEY1  -> J4.8       (было IO20)
IO22  KEY2  -> J4.7       (было IO21)
IO21  KEY3  -> J4.6       (было IO22)
IO20  KEY4  -> J4.5       (было IO23)
-- Сервис (J5) -- (метка SVC_IOxx == GPIOxx) --
IO11  SVC_IO11 -> J5.1
IO10  SVC_IO10 -> J5.2
IO7   SVC_IO7  -> J5.3
IO6   SVC_IO6  -> J5.4
EN    RESET (RC 10k/1µF + кнопка SW1)
-- Свободны: IO4 (U1.4), IO5 (U1.5), IO15 (U1.23, strapping) -- на паде модуля, не разведены --
```

Конфликтов нет. `IO0..3` (PWM) и `IO8/IO9` (RGB/BOOT) сохранены как в revA -> ядро
firmware не трогаем.

---

## 10. BOM (по разделам, с наличием Platan на 2026-07-22)

Пассив 0805, X7R и лучше; на делителе FB — 1%. Наличие/цена по розничному Platan
(`platan-parts`); QUANTY 0 при сроке = «под заказ», не «нет».

### 10.1 Силовой блок (из revA)

| Ref | PN | Корпус | Platan |
|-----|-----|---|---|
| J1 | клемма 2-pos 5.0 мм | THT | — |
| F1 | T4A slow-blow 5x20 + клипсы | THT | — |
| Q5 | AOD4185 | TO-252 | есть (YOUTAI 21₽, 1-2 дня, MINZAKAZ 1) |
| Q1..Q4 | AOD4184A | TO-252 | есть (2010030452, 28.94₽, MINZAKAZ 13) |
| U2 | TPS54202DDCR | SOT-23-6 | есть (2015708243, 35₽, 1-2 дня, MINZAKAZ 1) |
| L1 | 10 µH shielded >=2 А | 6x6 | — |
| R1, Rpd1..4 | 100k | 0805 | — |
| Rg1..4 | 100R | 0805 | — |
| R2 | 100k 1% | 0805 | — |
| R3 | 22k 1% (Vout 3.3 В) | 0805 | — |
| C1 | 100µF/25В | THT электролит | — |
| C2 | 100нФ/50В | 0805 | — |
| C3, C4 | 10µF/50В | 1210 | — |
| C5 | 100нФ | 0603 | — |
| C6, C7 | 22µF/16В | **1210** | 22µF/16В в 0805 на Platan НЕТ (только <=6.3В) -> 1210 (CCTC TCC1210, MINZAKAZ 1) |
| J2 | клемма 5-pos 2.54 мм | THT | — |

### 10.2 ESP32-C6 + обвязка

| Ref | PN | Корпус | Platan |
|-----|-----|---|---|
| U1 | **ESP32-C6-WROOM-1-N16** | module | **НЕТ на Platan** — внешний источник |
| C8 | 22µF/16В | **1210** | 3V3 у модуля (pin 2); тот же корпус, что C6/C7 |
| C9 | 100нФ | 0603 | — |
| R4 | 10k | 0805 | — (EN pull-up на +3V3) |
| C10 | 1µF | 0805 | — (EN RC) |
| R11 | 10k | 0805 | — (IO8 pull-up на +3V3, boot=1) |
| SW1, SW2 | тактовая кнопка | SMD/THT | — (RESET, BOOT) |

LDO и оба Шоттки убраны (Option A: buck делает 3.3 В напрямую, USB не питает плату).

### 10.3 USB Type-B

| Ref | PN | Корпус | Platan |
|-----|-----|---|---|
| J3 | USB Type-B THT right-angle (футпринт TE 292304-5) | THT | **есть, Platan 249636968** |
| U3 | USBLC6-2SC6 | SOT-23-6 | есть (YOUTAI/TECH PUBLIC 8₽, MINZAKAZ 1) |
| R5, R6 | 0R (место под 22R) | 0805 | — |

### 10.4 Периферия / HMI

| Ref | PN | Корпус | Platan |
|-----|-----|---|---|
| LED1 | **WS2812B-V5** | 5050 | **есть, 1551 шт**, 14₽, MINZAKAZ 1 |
| R7 | 300-470R | 0805 | — |
| C11 | 100нФ | 0603 | — |
| J4 | гребёнка «мама» 8-pin 2.54 | THT | — (OLED-модуль) |
| R8, R9 | 4.7k | 0805 | — (I2C pull-up) |
| J5 | гребёнка «папа» 6-pin 2.54 | THT | — (сервис) |
| R10 | 4.7k (место, не распаивать) | 0805 | — (опц. 1-Wire) |
| H1..H4 | M3 mounting hole 3.2 мм | — | — |
| TP1.. | test pads 1 мм | copper | — |

**Итого distinct PN ~35.**

### 10.5 Наличие и корпуса на Platan (проверено 2026-07-22)

Ключевое для выбора футпринтов и замен. `MINZAKAZ` — мин. заказ (важно для ручной сборки).

| Позиция | Корпус к применению | Наличие / замена |
|---|---|---|
| 100nF | 0805 или 0603, X7R 50В | CCTC (TCC0805/0603X7R104K500), ~2₽, **MINZAKAZ 1**, 1-2 дня. Любой корпус |
| 1µF | 0805/0603 X7R | коммодити, MINZAKAZ 1 |
| 10µF/50В (Cin buck) | **1210** X7R | CCTC TCC1210X7R106K500MT, 12-20₽, **MINZAKAZ 1**. В 0805 при 50В нет |
| 22µF/16В (Cout, 3V3) | **1210** X7R/X5R | CCTC TCC1210, MINZAKAZ 1. **В 0805 только <=6.3В** — на 3.3В рельсе 6.3В прошёл бы, но берём 1210 с запасом |
| 100µF/25В электролит | THT radial 6.3мм, шаг 2.5 | JWCO 6.3x7.7 / 6.3x12, 3-4₽, **MINZAKAZ 100** (насыпью) |
| Резисторы (100k/100R/10k/4.7k/22k/470R/0R) | 0805 (или 0603/1206) | все значения есть. Yageo/Vishay — **реелами** (MINZAKAZ 1000+); generic «Тайвань» 0805 — **MINZAKAZ 10** (кратно 5). Корпус не проблема |
| L1 10µH >=2А shielded | 6x6 (CDRH6D28) | **CDRH6D28NP-100NC** (как revA), Sumida 32₽, **MINZAKAZ 1**, 3-4 дня |
| J1 клемма 2P 5.0мм | DG127-5.0-02P | Degson, 9₽, **MINZAKAZ 1** (как revA) |
| J2 клемма 5P 2.54мм | DG308-2.54-05P | Degson, 21₽, **MINZAKAZ 1** (как revA) |
| J4 гнездо 8P 2.54 | из PBS-40 (обрезать) | Connfly DS1023-1x40, **MINZAKAZ 1**, 333 в наличии |
| J5 вилка 6P 2.54 | из PLS-40 (обрезать) | Connfly/KLS, MINZAKAZ 10 |
| SW1/SW2 тактовые | 6x6 THT/SMD | TE 6x6 (1825910-6 и др.), MINZAKAZ 15 |
| F1 T4A 5x20 | 5x20 slow-blow | Klemsan 4А 5x20, **MINZAKAZ 25, 1-3 нед** — подтвердить slow-blow (T); долгий срок, рассмотреть ЧипДип |
| Держатель F1 | клипсы/патрон 5x20 | коммодити (API отдаёт битый JSON — брать вручную) |
| U1 ESP32-C6-WROOM-1-N16 | module | **не на Platan** — AliExpress |
| U2 TPS54202DDCR | SOT-23-6 | Platan MINZAKAZ 1 (см. §10.1) |
| U3 USBLC6-2SC6 | SOT-23-6 | Platan MINZAKAZ 1 |
| LED1 WS2812B-V5 | 5050 | Platan, **в наличии 1551**, MINZAKAZ 1 |
| J3 USB Type-B | THT, футпринт 292304-5 | **Platan 249636968** |
| Q1..Q4 AOD4184A / Q5 AOD4185 | TO-252 | Platan MINZAKAZ 13 / 1 |

**Выводы по заменам:**
- **Керамика с большим C×V идёт в 1210**, не 0805: 10µF/50В и 22µF/16В — только 1210 (CCTC,
  MINZAKAZ 1). Заложить в схеме/футпринтах 1210 для C3/C4/C6/C7/C8.
- **Резисторы** — корпус любой (0603/0805/1206), но брендовые реелами; для ручной сборки
  брать generic «Тайвань» (MINZAKAZ 10) или мини-реел.
- **Электролит и предохранитель** — насыпью/долгий срок; не критичные, заказать заранее.
- Единственная long-lead позиция — **модуль (AliExpress)**.

---

## 11. Схема net-by-net (черновик)

```text
+12V_IN     J1.1 -> F1.1                                   3.33 A
+12V_FUSED  F1.2 -> Q5.D                                   3.33 A
+12V        Q5.S -> C1,C2 -> U2.VIN, J2.1 (LAMP_COM)       3.33 A
+3V3        U2 out (после L1) -> C6,C7; модуль(pin2)+C8,C9; WS2812; OLED VCC; подтяжки
VBUS        J3.1 -> NC (не заведён на питание; опц. делитель на GPIO)
GND         тихая земля; L2 plane; сходится с PGND у J1 (звезда); экран J3 -> GND
PGND        возврат ламп (истоки Q1..Q4) -> J1 return; внешние слои
EN          R4->+3V3, C10->GND, SW1->GND
BOOT        IO9; SW2->GND
USB_D-/D+   J3.2/J3.3 -> U3(ESD) -> R5/R6 -> IO12/IO13      дифпара 90 Ω
I2C_SCL/SDA IO18/IO19 -> R8/R9(4.7k->3V3) -> J4.3/J4.4
KEY1..4     IO20..23 -> J4.8/7/6/5
WS2812_DIN  IO8 -> R7 -> LED1.DIN;  LED1.VDD=+3V3, C11;  R11 10k IO8->+3V3 (boot)
CH0..3_IN   IO0,IO1,IO2,IO3 -> Rg -> GATE0..3
GATE0..3    Rg out, Rpd->PGND, Q gate, TP_G0..3
LAMP0..3    J2.2..5 -> Q1..Q4 drain
SVC_*       IO6,IO7,IO10,IO11 -> J5; UART_TX/RX (IO16/17) -> J5
```

---

## 12. Layout-правила (4 слоя)

Из revA (актуальны) + новое для 4-слойки:

1. **Единая точка стыка** `PGND` и тихой `GND` — у J1 (звезда). Силовой возврат по
   внешним слоям, не через L2. Реализовать **net-tie** (KiCad `NetTie_2`) или 0R между
   `GND` и `PGND` у J1 — держит нети раздельными для DRC, но соединяет в одной точке.
   `GND` (тихая) — сплошной полигон на **L2**; `PGND` — медь на внешних L1/L4 в силовом углу.
2. **Плоскости под антенной вырезаны на L1/L2/L3/L4.** Модуль на кромке, антенна наружу.
3. **USB-дифпара над сплошной L2**, без разрезов опоры под ней; коротко, парой, 90 Ω.
4. **Вход. петля buck < 2 мм** (ближайший Cin к VIN/GND). SW-медь малой площади. FB —
   отдельным возвратом к GND-пину U2 (revA §6.2a).
5. **Gate-петли коротко:** Rg/Rpd у своего MOSFET, возврат в локальную PGND. Четыре
   MOSFET колонкой, лампы J2 сразу за ними.
6. **Ширины под 3.33 А** — все три входных сегмента (`+12V_IN`, `+12V_FUSED`, `+12V`) и
   `LAMP0..3`: POWER-класс 1.5 мм (1 oz, ~11 °C). DRC ток НЕ проверяет.
7. **Netclass с ведущими wildcard** (`*12V*`, `*LAMP*`) — локальные метки на корневом
   листе получают префикс `/`.
8. **Via stitching** L1<->L2 по периметру модуля и в силовой земле; EPAD модуля на
   via-массив в L2.
9. **Buck и силовой блок — подальше от антенны.**
10. **Тепловые via** под тэбами Q1..Q5 (DPAK).

---

## 13. Оформление под фабрику (pselectro.ru, 4 слоя)

По правилам revA-fab-дока ([FABRICATION_ORDER.md](FABRICATION_ORDER.md)), с поправками
на 4 слоя:

| Параметр | Значение |
|---|---|
| Контур | 92 x 80 мм (= 0.736 дм²; оценка ~1806₽/плата бралась для 100x100 = 1 дм², т.е. с запасом) |
| Слои | **4** |
| Стек-ап (MLB) | `Типовой/4/1,5/35/FR/вн 0.71 (35/35)`: L1 Sig / L2 GND / L3 Pwr / L4 Sig |
| Толщина | **1.57 мм** (типовой конструктив pselectro, см. §3; строго 1.5 — на заказ) |
| Медь | **35 µm (1 oz) на всех 4 слоях** (внутренние 35/35) |
| Min track / clearance | 0.20 / 0.20 мм (класс 4; USB-пара может быть уже — считать) |
| Min hole | 0.40 мм |
| Медь-край | 0.30 мм (фрезеровка) / 0.50 мм (скрайб) |
| Controlled impedance | **не заказываем** (USB FS терпим; геометрию считаем сами) |
| Маска | обе стороны; шелк — верх (низ по месту) |
| Финиш | HASL (или ENIG, если важна плоскостность под модуль) |
| NPTH | 4x M3 (3.2 мм), F1 (2.7 мм) — **немета** |
| Vias | tented; отдельные PTH.drl / NPTH.drl |

**Board Setup — контрольные значения (KiCad, revB):**
- **Нет-классы:** Default 0.2/0.2, via 0.6/0.3 (аннулярное 0.15); POWER 1.5/0.2, via 0.8/0.4
  (аннулярное 0.2); USB 0.4/0.2, дифпара 0.4/0.2.
- **Паттерны:** `*12V*`, `*LAMP*`, `PGND` -> POWER; `*USB_D*` -> USB (ведущий `*` обязателен —
  локальные метки корневого листа получают префикс `/`).
- **Constraints:** min track 0.2, min clearance 0.2, min through-hole **0.4**, медь-край 0.5,
  **min via annular ring 0.15** (важно: при 0.3 сквозная via 0.6/0.3 даёт 0.15 и фолит DRC),
  min via Ø 0.6, hole-to-hole 0.25.
- **Blind/buried vias и microvias (uVia) — ВЫКЛЮЧЕНЫ.** Типовой 4-сл. pselectro — одна
  ламинация, только механические сквозные PTH-via; uVia требует HDI-процесса (лазер,
  секвенциальная сборка) — не наш случай.

Gerber-набор и порядок проверки — как в revA-fab §3-4, **плюс два внутренних слоя**
(In1.Cu = GND, In2.Cu = Power) в набор. Проверить в внешнем вьювере, что вырезы плоскостей
под антенной присутствуют на In1/In2.

---

## 14. Статус вопросов (закрыты 2026-07-22)

- [x] **Модуль вне Platan** — берём с **AliExpress**, заказ позже. Единственная long-lead
      позиция.
- [x] **VCC OLED = 3.3 В** — подтверждено (SSD1315 по ядру 3.3 В).
- [x] **Футпринт USB Type-B 292304-5** — сверен с Platan 249636968: совпал (расхождение
      только по высоте корпуса — разные базы измерения, на посадку не влияет).
- [x] **Пиновка модуля в KiCad** — verified (SnapMagic). Правка: 3D-модель повёрнута на
      90° по X. **Внимание (KiCad-trap):** `Update Footprints from Library` сбрасывает
      per-instance 3D-override — не потерять поворот при обновлении из библиотеки.
- [x] **IO8 strapping** — ставим 10k pull-up на +3V3 (R11, populate): гарантирует boot=1,
      WS2812 DIN это не мешает (§4.6).
- [x] **Keepout антенны** — увеличен в футпринте с запасом; антенна на кромку платы,
      компоненты в зону не попадают by design.
- [ ] **USB-дифпара 90 Ω** — единственный оставшийся расчёт. НЕ ищется в datasheet
      (геометрия зависит от стека, а не от компонента; 90 Ω — требование USB-спеки).
      Метод: **KiCad PCB Calculator** (Coupled Microstrip) или Saturn PCB Toolkit,
      входные H=0.36 мм (2×препрег 7628, §3), T=35 µm, er~4.5 -> ориентир W~0.4-0.45 /
      S~0.2 мм (шире из-за более толстого препрега). Тестовый
      PCB-купон НЕ нужен (расчёт аналитический). Для FS 12 Мбит/с геометрия некритична.

---

## 15. Firmware — что добавить (+ ОБЯЗАТЕЛЬНАЯ правка маппинга каналов)

⚠️ **Ядро всё-таки требует одной правки:** каналы ламп на плате переставлены (§9), карту
`LAMPx -> GPIO` в ядре надо поменять на актуальную:
`LAMP0=IO1, LAMP1=IO0, LAMP2=IO3, LAMP3=IO2` (было прямое IO0..3). Иначе лампы поедут не туда.

Добавить:
- I2C (`IO18`/`IO19`) + драйвер SSD1315, экран настроек;
- чтение 4 кнопок — **порядок реверснут**: `KEY1=IO23, KEY2=IO22, KEY3=IO21, KEY4=IO20`
  (active-low, внутр. pull-up, debounce);
- нативный USB-Serial-JTAG (лог/CLI); проводной UART доступен на J5 (`IO16` TX / `IO17` RX);
- опционально: сервисные `IO6/7/10/11` (J5) под датчики.

## 16. Принятые отклонения (Rev B, решено 2026-07-29)

Осознанные отклонения, оставленные в Rev B (учебный прототип, indoor, лабораторный БП 12 В).
Обе позиции **не меняют PCB/схему**, проверяются на первом образце.

- **LED-01 — WS2812B-V5 запитан от 3.3 В** (спека V5 = 3.7–5.3 В). Решение: **принять out-of-spec
  и проверить на прототипе**, что индикатор светит и принимает данные при 3.3 В. Это единственный
  статусный LED, не критичен. Если конкретная партия не заведётся — заменить на drop-in в том же
  5050/4-pin (SK6812 / не-V5 WS2812B) либо DNP; PCB при этом не меняется.
- **USB-01 — VBUS-clamp USBLC6 (U3.5) подключён к системной +3V3, J3.1 (USB VBUS) = NC.**
  Референс USBLC6 использует USB VBUS как верхнюю clamp-шину. Решение: **принять как есть**, т.к.
  плата не питается от USB и ESD-события редки; при ESD часть энергии может кратко воздействовать
  на 3V3. Проверить ESD-устойчивость USB на прототипе. Правку (J3.1→U3.5 + 100nF VBUS–GND) отложить
  до возможного Rev C, если проявится проблема.

---

**Источники:** ESP32-C6-WROOM-1 Datasheet v0.6 (`datasheets/ESP32-C6-WROOM-1-Datasheet.pdf`),
модуль OLED (`datasheets/oled_buttons_module.jpg`),
[smartlada_rev_a_bom_netlist.md](smartlada_rev_a_bom_netlist.md),
[KICAD_WORKFLOW.md](KICAD_WORKFLOW.md), [FABRICATION_ORDER.md](FABRICATION_ORDER.md).
Наличие компонентов — розничный Platan (`platan-parts`, 2026-07-22).
