saschapo/smartlada/custom_pcb/smartlada_revB/260728_smartlada_revB_review.md

# SmartLada Rev B — consolidated PCB review

**Дата review:** 2026-07-28  
**Проверяемая ревизия PCB:** `smartlada_revB.kicad_pcb`, сохранена 2026-07-25 23:45 MSK  
**Назначение:** indoor-устройство, питание от регулируемого БП 12 В; плата не предназначена для прямого подключения к автомобильной бортовой сети.  
**Нагрузка:** четыре лампы R10W, суммарно 40 Вт / около 3.33 А при 12 В.

## 1. Итоговый статус

Базовая архитектура платы корректна: входная защита, силовые MOSFET-каналы, разделение PGND/GND, внутренние полигоны питания и основная GPIO-разводка выполнены осмысленно. Полного перепроектирования не требуется.

Текущую сохранённую ревизию **нельзя выпускать в Gerber**. Главный непосредственный блокер — незавершённая трассировка buck после последнего перемещения C6/C7 и R2/R3. Дополнительно до заказа необходимо исправить поля MPN/BOM, USB ESD-узел, питание статусного LED, RF-размещение и механический конфликт OLED/крепежа.

Обозначения приоритета:

- **P0 — release blocker:** плата или сборка гарантированно не соответствует замыслу; производство запрещено до исправления.
- **P1 — обязательно до финальной ревизии:** высокая вероятность нестабильности, ручной переделки или ухудшения ключевой функции.
- **P2 — проверка/улучшение:** прототип, вероятно, заработает, но режим не полностью гарантирован либо отсутствует достаточная верификация.

## 2. Сводная таблица правок

| ID | Приоритет | Узел | Статус на 2026-07-28 | Требуемое действие |
|---|---|---|---|---|
| BCK-01 | P0 | Buck output | C6/C7 перемещены к L1, но L1.1, C6/C7 и шина `+3V3` в текущем PCB не соединены трассами/via | Завершить `L1 → C6/C7 → +3V3 plane`, затем refill zones и DRC |
| BCK-02 | P0 | Buck FB | После перемещения R2/R3 сеть `FB` не дотрассирована | Соединить U2.4 с узлом R2/R3; sense брать с `Cout+`, R3 вернуть в тихую GND |
| BCK-03 | P1 | Buck SW | U2.2 → L1 около 7 мм, 0.4 мм | Приблизить/повернуть L1; целевой путь 2–3 мм, короткая медь без полигона |
| BCK-04 | P1 | Bootstrap | Петля U2.6–C5–SW около 5.2 мм | Разместить C5 непосредственно у U2, сократить обе стороны петли |
| BOM-01 | P0 | MPN | Несколько MPN противоречат номиналам схемы | Исправить поля схемы и сгенерировать BOM заново |
| BOM-02 | P0 | R3 buck | `Value=22k`, MPN соответствует 13.7 kΩ | Указать реальный MPN 22 kΩ; 13.7 kΩ даст около 4.95 В вместо 3.3 В |
| DRC-01 | P0 | Проверка выпуска | Последний DRC старше PCB и не видит новые unconnected | Новый ERC/DRC после окончания разводки: 0 violations, 0 unconnected, 0 footprint mismatch |
| USB-01 | P1 | USB ESD | U3 VBUS-clamp подключён к `+3V3`, USB VBUS не используется | Подключить J3.1 только к U3.5, добавить 100 nF VBUS–GND; плату от USB не питать |
| USB-02 | P1 | USB routing | Длины согласованы, но геометрия не подтверждает 90 Ω differential | Переразвести штатной diff-pair после расчёта по stack-up либо явно принять uncontrolled FS USB |
| RF-01 | P1 | Антенна ESP32 | Медь очищена, но под антенной остаётся FR-4 основной платы | Вынести антенную часть за Edge.Cuts либо сделать рекомендуемый вырез |
| LED-01 | P1 | WS2812B-V5 | Питание 3.3 В ниже специфицированных 3.7 В | Заменить на LED с гарантированным 3.3 В либо обычный RGB LED |
| FW-01 | P0 для запуска | GPIO | Firmware использует прямой GPIO0..3, плата имеет перестановку | Ввести аппаратную карту `L0=1, L1=0, L2=3, L3=2` |
| FW-02 | P0 для запуска | Flash | U1 — N8, текущий build/partition рассчитан на 16 MB | Создать профиль и partition table для 8 MB |
| MECH-01 | P1 | OLED/M3 | Контур OLED пересекает область M3_3/головки винта | Использовать точный footprint OLED и перенести отверстие либо модуль |
| DOC-01 | P1 | Размер платы | PCB 92×80 мм, fabrication doc 91.5×79 мм | Зафиксировать один размер во всех источниках и заказе |
| GATE-01 | P1 | Затворы Q1–Q4 | Rg/Rpd удалены от MOSFET, после Rg остаются длинные gate-трассы | Перенести Rg/Rpd к каждому MOSFET; Rpd коротко gate–source |
| FUSE-01 | P2 | F1/inrush | T4A имеет небольшой запас над 3.33 А, лампы дают холодный бросок | Проверить времятоковую кривую и серию холодных включений |

## 3. Buck TPS54202 — актуальная оценка после переразводки

### 3.1 Что исправлено удачно

Входной контур стал заметно лучше:

- C4 расположен рядом с U2 и является основным высокочастотным входным конденсатором;
- C3 подключён параллельно как дополнительная входная ёмкость;
- VIN и GND U2 соединены с C4 по F.Cu без возврата через удалённые участки платы;
- GND U2 имеет близкий via в сплошную GND-плоскость;
- положение C6/C7 рядом с L1 теперь соответствует правильной функциональной последовательности лучше предыдущей версии.

Расчётная электрическая часть остаётся разумной:

- R2 = 100 kΩ, R3 = 22 kΩ дают около 3.3 В;
- L1 = 10 µH;
- C3/C4 = 10 µF;
- C6/C7 = 22 µF;
- при 12 → 3.3 В, 500 кГц и нагрузке около 0.5 А расчётная пульсация тока L1 составляет примерно 0.48 App, ожидаемый пик около 0.74 А; запас TPS54202 и дросселя достаточен.

### 3.2 Критическое текущее состояние: перемещение выполнено, трассировка не закончена

В сохранённом PCB отсутствуют медные соединения для следующих цепей:

- выходная площадка L1 (`/+3V3`);
- положительные площадки C6 и C7;
- отрицательные площадки C6 и C7 до GND/via;
- R2.1 до `+3V3`;
- узел обратной связи U2.4–R2.2–R3.2;
- R3.1 до тихой GND.

Поэтому сохранённая плата в текущем виде не создаёт выход 3.3 В. Старый `DRC.rpt`, содержащий `0 unconnected pads`, был создан до этого перемещения и к текущей ревизии неприменим.

### 3.3 Требуемая окончательная топология

Силовая последовательность должна быть физически реализована так:

```text
+12V → C4/U2 → SW → L1 → C6/C7 → два via → In2 +3V3 plane → нагрузка
                 │             │
                 C5            └→ короткий GND-return → U2 GND
```

Правила завершения разводки:

1. Соединить выход L1 непосредственно с положительными площадками C6/C7 широкой короткой дорожкой, ориентировочно 0.8–1.0 мм.
2. Вводить питание в In2 `+3V3` только из узла после C6/C7; поставить рядом с `Cout+` два via 0.7/0.3 или крупнее.
3. У каждой отрицательной площадки C6/C7 поставить близкий GND-via; обеспечить короткий возврат к GND U2 через непрерывный In1.
4. FB-sense брать с положительной площадки ближайшего C6/C7, до ответвления в нагрузочную плоскость.
5. R3 подключить к тихой GND около U2, не к силовому пути выходных конденсаторов.
6. Не прокладывать FB рядом со SW и под корпусом L1.

### 3.4 Оставшиеся layout-замечания

Путь U2.2 → L1 в текущем размещении сохранился около 7 мм и выполнен шириной 0.4 мм. Для постоянного тока этого достаточно, но для переключающего узла важнее минимальная площадь и индуктивность. Рекомендуется повернуть или приблизить L1 так, чтобы его SW-площадка находилась в 2–3 мм от U2.2. SW следует делать коротким, умеренно широким и без большого полигона.

C5 расположен лучше исходной версии, но bootstrap-петля всё ещё около 5.2 мм суммарно. C5 следует поставить непосредственно возле U2.6 и локальной точки SW у U2, а не возле дросселя.

Опционально полезно добавить входной 100 nF в корпусе 0603 непосредственно между VIN/GND U2. Два 10 µF электрически достаточны, но малый конденсатор уменьшит паразитную индуктивность на быстрых фронтах.

## 4. BOM и поля компонентов

Поля `Value`, `MPN` и внешний Markdown-BOM пока нельзя использовать одновременно как надёжный источник закупки.

Актуальные расхождения схемы:

| Ref | Value в схеме | Текущее поле MPN | Риск/правка |
|---|---:|---|---|
| R3 | 22 kΩ | `RC0805FR-0713K7L` — 13.7 kΩ | **Критично:** заменить на MPN 22 kΩ; иначе около 4.95 В на 3V3 |
| R4 | 10 kΩ | тот же MPN 13.7 kΩ | Исправить на MPN 10 kΩ |
| R5, R6 | 0 Ω | `ERJP06F1003V` — код 1003, не 0 Ω | Исправить на 0 Ω либо оформить как solder jumper/DNP |
| R7 | 100 Ω | MPN 13.7 kΩ | Исправить на MPN 100 Ω |
| R8, R9 | 10 kΩ | MPN 13.7 kΩ | Исправить на MPN 10 kΩ |
| C6, C7, C8 | 22 µF | `TCC1210X7R106...` — 10 µF | Использовать MPN фактических 22 µF из закупочного BOM |
| C9 | 100 nF | MPN 10 µF/1210 | Исправить MPN и корпус |
| C10 | 1 µF | MPN 10 µF/1210 | Исправить MPN и корпус |

Внешний `smartlada_rev_b_bom.md` содержит более подходящие закупочные позиции, но его необходимо синхронизировать обратно со схемой. После исправления:

1. экспортировать BOM из KiCad;
2. сравнить `Ref / Value / Footprint / MPN` с закупочным листом;
3. отдельно проверить R3, R5/R6 и C6/C7;
4. не формировать заказ непосредственно из текущих полей схемы.

J4 в схеме имеет правильный female-footprint `PinSocket_1x08`, J5 — male `PinHeader_1x08`. В закупочном BOM J4 и J5 объединены как PLS-40 male; для J4 необходим PBS/PinSocket подходящей высоты.

## 5. Силовой тракт и MOSFET-каналы

### 5.1 Подтверждённо корректно

- Цепочка `J1 → F1 → Q5 → +12V` имеет правильную полярность.
- Q5 AOD4185 работает как high-side защита от переполюсовки.
- Q1–Q4 включены как low-side N-MOSFET: drain к LAMPx, source к PGND.
- На каждом затворе есть последовательный резистор и аппаратный pull-down.
- PGND и логическая GND соединены в одной контролируемой точке через net-tie рядом с силовым входом.
- Основные участки входа выполнены шириной до 3 мм; общий провод ламп — около 2 мм; отдельные LAMPx — около 2 мм.
- Для 3.33 А общего тока и около 0.83 А на канал при 35 µm меди эти ширины достаточны.
- Разъём J2 имеет достаточный токовый запас для данной indoor-нагрузки.

Оценочное рассеяние Q5 при 3.33 А и 20 mΩ составляет около 0.22 Вт — приемлемо для DPAK и текущей меди.

### 5.2 Затворные цепи

Rg1…Rg4 и Rpd1…Rpd4 находятся далеко от соответствующих MOSFET. После Rg остаются gate-трассы порядка 16–22 мм с переходами между слоями. Это увеличивает затворный контур и чувствительность к dV/dt на стоке.

Требуемая правка:

- Rg поставить непосредственно у gate MOSFET;
- Rpd поставить непосредственно между gate и локальным source/PGND;
- длинную GPIO-трассу вести до Rg со стороны ESP32;
- участок Rg → gate делать коротким, желательно без via.

### 5.3 AOD4184A при управлении 3.3 В

AOD4184A имеет гарантированный `RDS(on)` при VGS = 4.5 В и 10 В, но не при 3.3 В. Для тока около 0.83 А транзистор, вероятно, откроется достаточно, однако режим не подтверждён максимальным параметром datasheet.

Перед фиксацией BOM необходимо либо:

- измерить VDS и температуру корпуса при номинальном токе и холодном включении лампы;
- либо выбрать N-MOSFET с гарантированным `RDS(on)` при VGS = 2.5–3.0 В.

### 5.4 Предохранитель и холодный пуск

T4A разумен для постоянного тока 3.33 А, но имеет небольшой номинальный запас. Холодные нити четырёх ламп создают кратковременный ток, значительно превышающий номинальный. Ограничение блока питания снижает риск, но не заменяет проверку времятоковой характеристики F1.

Провести 50–100 одновременных холодных включений и проверить отсутствие деградации F1, перегрева Q5 и brownout ESP32.

## 6. USB Type-B и защита ESD

### 6.1 Что выполнено правильно

- GPIO12 используется как USB D−, GPIO13 как USB D+.
- Полные длины линий близки: примерно 19.6 и 20.0 мм; skew около 0.36 мм.
- Под USB имеется непрерывный GND reference.
- R5/R6 предусмотрены как места под последовательные элементы.

### 6.2 U3 USBLC6-2SC6

U3.5 `VBUS` подключён к системной `+3V3`, а J3.1 VBUS оставлен NC. При положительном ESD-событии часть энергии может инжектироваться в шину 3.3 В, где buck и ESP32 не предназначены для поглощения такого обратного тока.

Рекомендуемая схема:

- соединить J3.1 VBUS только с U3.5;
- добавить возле U3 конденсатор около 100 nF VBUS–GND;
- не соединять USB VBUS с питанием платы;
- переместить U3 максимально близко к контактам J3;
- вести `J3 → U3 → R5/R6 → ESP32` без длинных ответвлений.

### 6.3 Дифференциальная пара

Согласование длины хорошее, но D+/D− не сохраняют постоянную связанную геометрию. При текущем stack-up 0.36 мм до GND-плоскости заявлять 90 Ω differential без расчёта нельзя. Короткий USB Full-Speed, вероятно, будет работать, однако это не эквивалент контролируемому импедансу.

Варианты:

1. Рассчитать ширину/зазор по фактическому stack-up изготовителя и переразвести штатным KiCad differential-pair router до 90 Ω ±10%.
2. Для прототипа явно принять короткую uncontrolled Full-Speed линию, не указывая в документации, что 90 Ω уже обеспечены.

## 7. ESP32-C6 и RF

### 7.1 Что выполнено правильно

- Модуль расположен у правого края платы.
- Под антенной очищены все четыре медных слоя.
- В keepout нет компонентов и via.
- Под центральной GND-площадкой модуля есть массив переходных отверстий.
- In1 представляет собой почти непрерывную GND-плоскость.
- Локальная развязка питания ESP32 присутствует.

### 7.2 Антенна над основной платой

Антенная часть модуля остаётся над FR-4 основной платы; до Edge.Cuts остаётся около 2.3 мм. Отсутствие меди уменьшает влияние, но диэлектрик основной платы всё равно изменяет настройку и эффективность PCB-антенны.

Поскольку Zigbee является основной конечной функцией, рекомендуется:

- сдвинуть U1 так, чтобы антенная часть выступала за край основной платы;
- либо сделать вырез под антенной и по её сторонам по рекомендациям Espressif;
- добавить короткий ряд GND-via вдоль заземлённой части модуля, не входя в keepout;
- обеспечить не менее 15 мм свободного пространства вокруг антенны в корпусе;
- проверить RSSI, дальность и устойчивость Zigbee в окончательном корпусе.

## 8. Статусный LED

Предыдущее несоответствие нумерации pads LED1 **исправлено**: текущий footprint использует составные номера `1-VDD`, `2-DOUT`, `3-GND`, `4-DIN`, соответствующие символу. Это изменение следует считать закрытым после свежего DRC.

Остаётся электрическая проблема: WS2812B-V5 запитан от 3.3 В, тогда как для V5 указывается рабочее питание 3.7–5.3 В. Возможна работа отдельных экземпляров, но она не гарантирована по партиям, температуре и просадкам питания.

Рекомендуется:

- заменить LED1 на адресный LED, явно рассчитанный на питание 3.3 В;
- либо применить обычный RGB LED с тремя резисторами;
- не добавлять отдельную 5-вольтовую шину только ради одного статусного индикатора.

## 9. GPIO и firmware

Фактическая карта силовых каналов:

| Канал платы | GPIO |
|---|---:|
| LAMP0 | GPIO1 |
| LAMP1 | GPIO0 |
| LAMP2 | GPIO3 |
| LAMP3 | GPIO2 |

Текущий firmware и web UI используют прямой порядок GPIO0, GPIO1, GPIO2, GPIO3. Без отдельного hardware profile функциональные каналы будут попарно переставлены.

Требуется единая таблица аппаратного отображения, используемая драйвером, конфигурацией и UI:

```text
LAMP0 = GPIO1
LAMP1 = GPIO0
LAMP2 = GPIO3
LAMP3 = GPIO2
```

Кнопки также имеют обратный порядок: KEY1=GPIO23, KEY2=GPIO22, KEY3=GPIO21, KEY4=GPIO20.

На PCB установлен ESP32-C6-WROOM-1-N8 с 8 MB Flash. Текущая команда сборки в корневом README использует `FlashSize=16M` и 16-мегабайтную partition scheme от devboard N16. До запуска Rev B необходимо создать отдельный профиль:

- FlashSize = 8 MB;
- partition table, физически помещающаяся в 8 MB;
- проверенные размеры OTA-разделов и файловой системы;
- отдельное имя board profile `smartlada_revB`.

## 10. Механика и сборка

### 10.1 OLED и M3_3

Текущий условный контур OLED составляет около 44.5×27.6 мм. Центр M3_3 находится внутри либо практически на границе этого контура. Даже при отсутствии касания самой платы головка винта или стойка диаметром около 6–7 мм создаёт вероятный конфликт.

Необходимо:

1. измерить фактический OLED-модуль;
2. создать footprint с реальным контуром, разъёмом, монтажными отверстиями и courtyard;
3. добавить keepout под головку винта/стойку;
4. перенести M3_3 либо J4/OLED.

### 10.2 J4/J5

- J4 на PCB и в схеме — female 1×8; это соответствует концепции дочернего OLED-модуля.
- J5 — male 1×8.
- Внешний BOM ошибочно предлагает одинаковые PLS-40 male для обоих.
- Спецификация местами описывает J5 как 6-pin, хотя фактически он 8-pin.

Высоту J4 нужно выбирать вместе с реальной механикой OLED и корпуса.

### 10.3 Размер платы

Фактический Edge.Cuts:

```text
X: 53.2 … 145.2 mm = 92.0 mm
Y: 64.25 … 144.25 mm = 80.0 mm
```

`smartlada_rev_b_fabrication.md` указывает 91.5×79 мм. До заказа размер должен совпадать в PCB, fabrication note, Gerber review и заявке изготовителю.

## 11. Слои и технологичность

Подтверждённая структура:

- F.Cu — компоненты, сигналы и силовые линии;
- In1.Cu — сплошная GND-плоскость;
- In2.Cu — основная `+3V3`-плоскость;
- B.Cu — ограниченное количество сигналов;
- медь 35 µm на всех слоях;
- итоговая толщина около 1.6 мм;
- основные via 0.7/0.3 мм, кольцо 0.2 мм;
- глобальное tenting включено;
- RF keepout присутствует на всех медных слоях.

Эти параметры соответствуют указанным стандартным технологическим ограничениям PSElectro.

Остающиеся DFM-пункты:

- заменить тонкий TrueType-текст на B.Silk штриховым KiCad-шрифтом либо обеспечить толщину не менее технологического минимума;
- убрать локальное расхождение Value J4: на PCB `OLED_AND_BUTTONS`, в схеме `OLED AND BUTTONS`;
- не закрывать механический конфликт OLED/M3 исключением DRC;
- после окончания разводки заново заполнить все зоны перед DRC и Gerber export.

## 12. Несогласованности документации

Документы следует обновить после фиксации PCB, иначе они не могут считаться источником истины:

- введение `smartlada_rev_b_spec.md` всё ещё упоминает USB-C, хотя установлен USB Type-B;
- spec содержит как старый ориентир 100×100 мм, так и fabrication 91.5×79 мм, при факте 92×80 мм;
- J5 местами описан как 6-pin, фактически 8-pin;
- R7 в разных местах указан 300–470 Ω, фактически и в закупочном BOM — 100 Ω;
- R8/R9 в spec указаны 4.7 kΩ, фактически и в закупочном BOM — 10 kΩ;
- один раздел говорит, что firmware не меняется, другие правильно требуют новую GPIO-карту;
- корневой README описывает devboard N16 и не должен использоваться как инструкция прошивки Rev B;
- pinout корректно отражает текущую GPIO-карту, но его заголовок о parity относится к более раннему состоянию PCB.

После исправлений рекомендуется назначить источники истины:

- электрическая схема — номиналы, MPN и connectivity;
- PCB — физическая геометрия и GPIO routing;
- BOM, экспортированный из схемы — закупка;
- отдельный pinout — внешний интерфейс;
- отдельный fabrication note — только актуальные параметры производства.

## 13. Что не требует переделки

Следующие решения технически обоснованы и не нуждаются в искусственной критике:

- сама архитектура четырёх low-side каналов;
- high-side P-MOS защита от переполюсовки;
- отсутствие питания платы от USB;
- ширины основных силовых дорожек для 40 Вт нагрузки;
- одноточечное соединение PGND/GND возле входа;
- четырёхслойная структура со сплошным In1 GND;
- локальная развязка ESP32 и массив EPAD-via;
- выбор GPIO0…3 для ламп с учётом фактической карты;
- правильное назначение USB D−/D+;
- согласование длины USB-пары;
- медный keepout под RF-антенной;
- выбранные отверстия, кольца и tenting;
- отсутствие требования автомобильной load-dump/ISO 7637 защиты, поскольку заявлен регулируемый indoor-БП 12 В.

## 14. Чек-лист перед Gerber release

- [ ] Завершить трассировку buck: L1, C6/C7, FB, GND и вход в 3V3 plane.
- [ ] Сократить SW и bootstrap-петли либо осознанно зафиксировать прототипный риск.
- [ ] Перенести Rg/Rpd к Q1–Q4.
- [ ] Исправить все MPN в схеме и повторно экспортировать BOM.
- [ ] Сверить BOM по `Ref / Value / Footprint / MPN`.
- [ ] Исправить USBLC6 VBUS-clamp и размещение U3.
- [ ] Принять решение по геометрии USB differential pair.
- [ ] Принять решение по WS2812 на 3.3 В.
- [ ] Исправить положение антенны или Edge.Cuts под ней.
- [ ] Устранить конфликт OLED/M3_3.
- [ ] Синхронизировать J4/J5 и их пол в BOM.
- [ ] Зафиксировать габарит 92×80 мм либо изменить PCB на согласованный размер.
- [ ] Обновить spec, fabrication, pinout и root README.
- [ ] Refill all zones.
- [ ] ERC: 0 errors, 0 warnings либо документированные допустимые исключения.
- [ ] DRC: 0 violations, 0 unconnected, 0 footprint mismatch.
- [ ] Проверить Gerber/Excellon независимым viewer по всем четырём медным слоям.

## 15. План безопасного первого запуска

1. Не устанавливая ESP32 и LED1, подать 12 В от лабораторного БП с ограничением около 100–200 мА.
2. Проверить полярность и уровень `+3V3`; ожидаемое значение около 3.3 В, не выше 3.45 В.
3. Осциллографом проверить SW, пульсации 3V3, выбросы и запуск buck.
4. Проверить отсутствие обратного питания 3V3 через USB.
5. Установить ESP32 и прошить только 8-мегабайтным профилем.
6. Проверить USB Serial/JTAG, UART и отсутствие brownout при старте радио.
7. Проверить аппаратную GPIO-карту без ламп.
8. Подключать лампы по одной; проверить соответствие LAMP0…LAMP3 функциям firmware.
9. Выполнить одновременный холодный запуск четырёх ламп и измерить провал 12 В/3V3.
10. Провести тепловой тест 30–60 минут на максимальной длительной нагрузке.
11. Выполнить серию 50–100 холодных включений для оценки F1, Q5 и устойчивости ESP32.
12. Проверить Zigbee RSSI/дальность в окончательном корпусе и при работающем PWM/buck.

## 16. Проверенные файлы

- [`smartlada_revB/smartlada_revB.kicad_sch`](smartlada_revB/smartlada_revB.kicad_sch)
- [`smartlada_revB/smartlada_revB.kicad_pcb`](smartlada_revB/smartlada_revB.kicad_pcb)
- [`smartlada_revB/DRC.rpt`](smartlada_revB/DRC.rpt) — устарел относительно текущего PCB
- [`smartlada_revB/ERC.rpt`](smartlada_revB/ERC.rpt) — устарел относительно текущей схемы
- [`smartlada_rev_b_bom.md`](smartlada_rev_b_bom.md)
- [`smartlada_rev_b_fabrication.md`](smartlada_rev_b_fabrication.md)
- [`smartlada_rev_b_pinout.md`](smartlada_rev_b_pinout.md)
- [`smartlada_rev_b_spec.md`](smartlada_rev_b_spec.md)
- [`../README.md`](../README.md)

## 17. Основные datasheet/reference

- Texas Instruments, TPS54202: <https://www.ti.com/lit/ds/symlink/tps54202.pdf>
- Espressif, ESP32-C6 PCB layout: <https://docs.espressif.com/projects/esp-hardware-design-guidelines/en/latest/esp32c6/pcb-layout-design.html>
- STMicroelectronics, USBLC6-2: <https://www.st.com/resource/en/datasheet/usblc6-2.pdf>
- Alpha & Omega Semiconductor, AOD4184A: <https://www.aosmd.com/products/mosfets/medium-voltage-mosfets-40v-400v/aod4184a>
- WORLDSEMI WS2812B-V5 product data: <https://www.tme.com/ca/en/details/ws2812b-v5/smd-colour-leds/worldsemi/>
