saschapo/smartlada/custom_pcb/smartlada_revB/260729_smartlada_revB_review.md

# SmartLada Rev B — итоговый PCB review

**Дата review:** 2026-07-29  
**Проверяемая PCB:** `smartlada_revB/smartlada_revB.kicad_pcb`, сохранена 2026-07-29 15:01:56 MSK  
**Назначение:** indoor-устройство с питанием от регулируемого БП 12 В  
**Нагрузка:** четыре лампы R10W, суммарно 40 Вт / около 3.33 А при 12 В  
**Статус документа:** заменяет `260728_smartlada_revB_review.md` как актуальное заключение; старый документ сохранён для истории.

## 1. Итоговое заключение

Текущая Rev B имеет корректную силовую архитектуру и качественно улучшенную разводку. Buck полностью дотрассирован и пригоден для прототипа. Переразведённые затворные цепи Q1–Q4 также приняты: прежнее замечание о 16–22-миллиметровых участках после Rg закрыто.

Актуальный DRC:

- 0 DRC violations;
- 0 unconnected pads;
- 0 footprint errors.

Обязательной новой переразводки buck или силовых MOSFET-каналов не требуется.

До заказа и сборки остаются преимущественно интеграционные вопросы:

1. исправление MPN/BOM;
2. решение по WS2812B-V5 на питании 3.3 В;
3. устранение ERC library mismatch LED1;
4. окончательное решение по включению USBLC6;
5. механическая проверка OLED и M3_3;
6. синхронизация размеров платы и типов J4/J5 в документации;
7. отдельный firmware-профиль Rev B для фактической GPIO-карты и 8 MB Flash.

## 2. Приоритеты

- **Обязательно до заказа/сборки:** высокая вероятность неправильной комплектации, аппаратного конфликта или негарантированного режима.
- **Обязательно до первого запуска:** не требует изменения PCB, но без исправления устройство будет работать неправильно.
- **Необязательно/валидация:** текущая плата, вероятно, работает; изменение улучшает запас, EMI, повторяемость или документацию.
- **Закрыто:** прежнее замечание устранено и подтверждено текущей PCB/DRC.

## 3. Сводный статус

| ID | Узел | Статус | Итоговое действие |
|---|---|---|---|
| BCK-01 | Connectivity buck | **Закрыто** | C6/C7, FB, GND и 3V3 полностью соединены; DRC: 0 unconnected |
| BCK-02 | Входная петля | **Принято** | Внешний периметр около 6.32 мм; обязательных изменений нет |
| BCK-03 | SW U2→L1 | Необязательно | 6.97 мм; можно сократить, но для текущей нагрузки это не blocker |
| BCK-04 | Bootstrap | **Принято** | BOOT–C5–SW около 5.28 мм; приемлемо |
| BCK-05 | L1→C6/C7 | **Закрыто** | 3.07/3.71 мм через широкий F.Cu-полигон |
| BCK-06 | FB | **Принято** | U2→делитель 2.08 мм; R3→GND-via 1.70 мм |
| GATE-01 | Gate после Rg | **Закрыто** | 4.4–5.4 мм вместо прежних 16–22 мм |
| POWER-01 | Силовые дорожки | **Принято** | LAMPx 2 мм, PGND до 3 мм, силовой ток без via |
| BOM-01 | MPN | **Обязательно** | Исправить MPN и повторно экспортировать BOM |
| LED-01 | WS2812B-V5 @ 3.3 В | **Обязательно принять решение** | Заменить, DNP либо явно принять out-of-spec режим |
| ERC-01 | LED1 symbol/library | **Обязательно** | Синхронизировать символ; свежий ERC имеет 1 warning |
| USB-01 | USBLC6 VBUS clamp | Сильная рекомендация | Перевести U3.5 на USB VBUS либо документировать отклонение |
| USB-02 | USB impedance | Необязательно | Длины хорошие; строгие 90 Ω не подтверждены |
| RF-01 | Антенна над FR-4 | Валидация | Indoor может пройти; проверить Zigbee в корпусе |
| MECH-01 | OLED/M3_3 | **Обязательно проверить** | Точный footprint, винт, шайба и стойка |
| DOC-01 | Размер платы | **Обязательно** | PCB 92×80 мм; fabrication doc содержит 91.5×79 мм |
| FW-01 | GPIO map | **Обязательно до запуска** | L0=GPIO1, L1=GPIO0, L2=GPIO3, L3=GPIO2 |
| FW-02 | Flash | **Обязательно до запуска** | N8 требует 8 MB partition table вместо текущей 16 MB |
| MOS-01 | AOD4184A @ 3.3 В | Валидация | Измерить VDS и температуру; RDS(on) не нормирован при 3.3 В |
| FUSE-01 | T4A/inrush | Валидация | Серия холодных включений четырёх ламп |

---

# Часть I. Buck TPS54202

## 4. Электрические параметры

Схема buck:

- вход: 12 В;
- выход: 3.3 В;
- U2: TPS54202DDC;
- частота: около 500 кГц;
- L1: 10 µH;
- C3/C4: по 10 µF на входе;
- C5: 100 nF bootstrap;
- C6/C7: по 22 µF на выходе;
- R2: 100 kΩ;
- R3: 22 kΩ.

Расчётное выходное напряжение:

```text
VOUT ≈ 0.596 × (1 + 100k / 22k) ≈ 3.30 В
```

Оценка пульсации дросселя при 12 → 3.3 В:

```text
D ≈ 3.3 / 12 = 0.275
ΔIL ≈ (12 − 3.3) × 0.275 / (10 µH × 500 kHz)
ΔIL ≈ 0.48 App
```

При нагрузке 0.5 А ожидаемый пик тока дросселя составляет около 0.74 А. У TPS54202 и выбранного L1 имеется достаточный запас.

## 5. Точные длины buck

Размеры рассчитаны по координатам трасс и площадок в KiCad, а не по пикселям скриншота.

| Цепь | Длина | Ширина/геометрия | Оценка |
|---|---:|---|---|
| U2.3 VIN → C4+ | 3.177 мм | 0.4–0.7 мм F.Cu | Хорошо |
| C4− → U2.1 GND | 3.146 мм | 0.4–0.7 мм F.Cu | Хорошо |
| Внешний периметр входной горячей петли | около 6.323 мм | без удалённого возврата | Хорошо |
| U2.2 SW → L1.2 | 6.972 мм | 0.4 мм F.Cu | Допустимо, не идеально |
| U2.2 SW → C5.2 | 3.629 мм | 0.4 мм F.Cu | Допустимо |
| U2.6 BOOT → C5.1 | 1.655 мм | 0.4 мм F.Cu | Хорошо |
| Внешняя петля BOOT–C5–SW | около 5.284 мм | — | Допустимо |
| L1.1 OUT → C6+ | около 3.073 мм | широкий F.Cu-полигон | Хорошо |
| L1.1 OUT → C7+ | около 3.706 мм | широкий F.Cu-полигон | Хорошо |
| C6− → ближайший GND-via | около 2.806 мм | широкий GND-полигон | Хорошо |
| C7− → ближайший GND-via | около 6.048 мм | широкий GND-полигон | Допустимо |
| C6+ → ближайший 3V3-via | около 5.900 мм | широкий 3V3-полигон | Допустимо |
| C7+ → ближайший 3V3-via | около 9.200 мм | широкий 3V3-полигон | Допустимо |
| U2.4 FB → узел R2/R3 | 2.079 мм | 0.4 мм F.Cu | Хорошо |
| Узел FB → R3.2 | 2.000 мм | 0.4 мм F.Cu | Хорошо |
| R3.1 → GND-via | 1.700 мм | 0.4 мм F.Cu | Хорошо |

## 6. Входная горячая петля

C4 является ближайшим высокочастотным входным конденсатором. VIN и GND U2 связаны с ним коротко по F.Cu. U2 GND имеет близкий via в сплошную In1 GND.

Для синхронного buck входная петля является основной петлёй с большим di/dt. Текущий внешний периметр около 6.3 мм оценивается как хороший. C3 работает как дополнительная входная ёмкость и не обязан быть столь же близким, как C4.

Опционально можно добавить 100 nF 0603 непосредственно между VIN/GND U2. Два 10 µF электрически достаточны, но малый корпус даст меньшую паразитную индуктивность на фронтах.

## 7. SW-узел

U2.2 → L1.2 имеет длину 6.97 мм при ширине 0.4 мм.

По постоянному и пиковому току дорожка достаточна. При пике около 0.74 А её сопротивление, падение напряжения и тепловыделение пренебрежимо малы. Ограничение связано не с нагревом, а с:

- паразитной индуктивностью;
- overshoot/ringing;
- излучаемыми помехами;
- ёмкостной связью SW с соседними цепями.

Для reference-grade layout желательно 2–3 мм, но при фактической мощности около 0.5 А, четырёхслойной плате и отсутствии требований сертификации EMC текущие 6.97 мм не являются release blocker.

Решение:

- если L1 можно приблизить без перестройки узла — сократить SW;
- если потребуется существенная новая компоновка — оставить и проверить осциллографом.

Не увеличивать SW до большого полигона: минимальная площадь важнее избыточной ширины.

## 8. Bootstrap

Петля U2.6–C5–SW имеет внешнюю длину около 5.28 мм:

- BOOT → C5: 1.65 мм;
- SW → C5: 3.63 мм.

Это приемлемо. Обязательной перестановки C5 нет. При простой возможности C5 можно ещё приблизить к U2, но ожидаемый выигрыш невелик.

## 9. Выход L1/C6/C7

Предыдущее замечание о подключении C6/C7 через удалённую плоскость закрыто. Сейчас:

```text
U2 SW → L1 → широкий F.Cu 3V3-узел → C6/C7 → via-array → In2 3V3
```

Плюсы текущего исполнения:

- C6/C7 находятся непосредственно рядом с L1;
- расстояния от L1 до C6/C7 составляют только 3.1–3.7 мм;
- ток идёт через широкий полигон, а не через узкую дорожку;
- имеется большой массив 3V3-via;
- GND C6/C7 подключён широким локальным полигоном к In1 через несколько via.

Необязательное улучшение:

- добавить по одному GND-via непосредственно у GND-площадок C6 и C7;
- два 3V3-via можно поставить ближе к `Cout+`; текущий массив из девяти via имеет большой запас.

## 10. Feedback

FB выполнен достаточно хорошо:

- U2.4 до узла R2/R3: 2.08 мм;
- трасса не идёт длинным параллельным участком рядом с SW;
- R3 имеет собственный близкий GND-via;
- R2 получает VOUT из того же широкого узла, к которому подключены C6/C7.

Это не отдельный строгий Kelvin-track от площадки C6, но при широком выходном полигоне и нагрузке порядка 0.5 А падение на меди слишком мало, чтобы создавать заметную ошибку регулирования. Дополнительная переразводка FB не требуется.

## 11. Итог по buck

**Buck одобрен для прототипа. Обязательных изменений PCB нет.**

На первом образце проверить:

1. VOUT без ESP32: ориентир 3.3 В, допустимый практический диапазон около 3.2–3.4 В.
2. Пульсации непосредственно на C6 коротким GND-контактом щупа.
3. SW overshoot относительно GND U2 пружинным контактом, не длинным проводом щупа.
4. Запуск при включении радио ESP32.
5. Просадку 3V3 при одновременном холодном включении ламп.
6. Температуру U2 и L1 после 30–60 минут.

---

# Часть II. Выходные MOSFET-каналы

## 12. Силовые цепи Q1–Q4

Подтверждено:

- Q1–Q4 включены как low-side N-MOSFET;
- drain подключён к LAMPx;
- source подключён к PGND;
- LAMP0…LAMP3 выполнены дорожками 2 мм;
- общий PGND выполнен участками до 3 мм;
- силовой ток ламп идёт только по F.Cu;
- в основном силовом пути отсутствуют via;
- узкие дорожки B.Cu несут только gate/pull-down токи.

Длины LAMP-трасс:

| Канал | Полная длина медных сегментов | Ширина |
|---|---:|---:|
| LAMP0 | 25.462 мм | 2.0 мм |
| LAMP1 | 14.744 мм | 2.0 мм |
| LAMP2 | 14.795 мм | 2.0 мм |
| LAMP3 | 23.826 мм | 2.0 мм |

При токе около 0.83 А на канал эти дорожки имеют большой запас.

## 13. Gate-цепи после переразводки

Rg/Rpd перенесены значительно ближе к MOSFET. Расстояния от выхода Rg до gate с учётом via:

| Канал | Rg → gate | Оценка |
|---|---:|---|
| Q1 | около 4.4 мм | Хорошо |
| Q2 | около 5.4 мм | Хорошо |
| Q3 | около 5.1 мм | Хорошо |
| Q4 | около 5.1 мм | Хорошо |

Прежние значения составляли примерно 16–22 мм. Текущее исполнение при PWM 30 кГц, Rg=100 Ω и Qg около 14 нКл является приемлемым.

Длинные GPIO-трассы находятся до Rg, что соответствует правильной последовательности: series resistor расположен на стороне нагрузки, возле затвора.

Rpd подключён к тому же gate-узлу и возвращается в PGND по B.Cu. Строго локальное соединение Rpd с source было бы лучше, но при 100 kΩ и текущих расстояниях практического выигрыша от ещё одной переразводки не ожидается.

**Предыдущее замечание GATE-01 закрыто.**

## 14. AOD4184A при 3.3 В

Производитель гарантирует RDS(on) при VGS=4.5 В и 10 В, но не при 3.3 В. Это не означает, что MOSFET не откроется; при 0.83 А он, вероятнее всего, будет работать с большим запасом. Однако режим нужно подтвердить измерением.

На прототипе измерить:

- VDS полностью открытого Q1…Q4;
- температуру корпуса;
- холодный старт одной лампы;
- одновременный холодный старт четырёх ламп;
- работу при минимальном измеренном напряжении 3V3.

Если VDS или нагрев окажутся значительными, выбрать MOSFET с гарантированным RDS(on) при VGS=2.5–3.0 В.

## 15. Входной P-MOS и F1

Входная цепочка выполнена правильно:

```text
J1 → F1 T4A → Q5 AOD4185 → +12V
```

Q5 включён в правильной ориентации как high-side защита от переполюсовки. При 3.33 А и RDS(on) около 20 mΩ оценочное рассеяние составляет около 0.22 Вт — приемлемо.

T4A имеет небольшой запас над длительным током 3.33 А. Для ламп важен холодный бросок. Проверить времятоковую характеристику фактического предохранителя и выполнить серию 50–100 холодных включений.

---

# Часть III. Обязательные дальнейшие правки

## 16. Исправить MPN и BOM

Это основной реальный риск неверной сборки.

| Ref | Value в схеме | Текущее поле MPN | Требуемая правка |
|---|---:|---|---|
| R3 | 22 kΩ | MPN для 13.7 kΩ | **Критично:** поставить MPN 22 kΩ; 13.7 kΩ даст около 4.95 В |
| R4 | 10 kΩ | MPN для 13.7 kΩ | MPN 10 kΩ |
| R5/R6 | 0 Ω | `ERJP06F1003V`, код 1003 | MPN 0 Ω либо solder jumper/DNP |
| R7 | 100 Ω | MPN для 13.7 kΩ | MPN 100 Ω |
| R8/R9 | 10 kΩ | MPN для 13.7 kΩ | MPN 10 kΩ |
| C6/C7/C8 | 22 µF | MPN для 10 µF/1210 | MPN фактических 22 µF |
| C9 | 100 nF/0603 | чужой MPN 10 µF/1210 | Исправить MPN/корпус |
| C10 | 1 µF/0603 | чужой MPN 10 µF/1210 | Исправить MPN/корпус |

Внешний `smartlada_rev_b_bom.md` содержит более подходящие закупочные позиции, но поля нужно синхронизировать обратно со схемой.

Перед заказом:

1. исправить `Value / Footprint / MPN / Manufacturer` в схеме;
2. экспортировать новый BOM из KiCad;
3. сравнить его с закупочным BOM;
4. отдельно проверить R3, R5/R6, C6/C7;
5. не использовать текущие MPN схемы для автоматической комплектации.

## 17. WS2812B-V5 на 3.3 В

Pin numbering footprint LED1 исправлен и DRC больше не показывает net conflicts:

```text
1-VDD
2-DOUT
3-GND
4-DIN
```

Остаётся питание: WS2812B-V5 специфицирован примерно для 3.7–5.3 В. Питание 3.3 В находится вне гарантированного диапазона.

Нужно принять одно из решений:

- заменить на адресный LED с гарантированной работой от 3.3 В;
- заменить на обычный RGB LED;
- оставить LED1 DNP;
- явно принять негарантированный режим конкретной партии.

Добавлять отдельную шину 5 В только ради одного статусного LED нерационально.

## 18. ERC warning LED1

Свежая проверка ERC от 2026-07-29:

```text
0 errors
1 warning: Symbol 'WS2812B' doesn't match copy in library 'Vendor'
```

Необходимо синхронизировать символ схемы и библиотеку, не потеряв правильную нумерацию выводов. После обновления повторно выполнить ERC и DRC.

Целевое состояние выпуска:

```text
ERC: 0 errors, 0 warnings
DRC: 0 violations, 0 unconnected, 0 footprint errors
```

## 19. USBLC6-2SC6

Текущее соединение:

- U3.5 VBUS → системная `+3V3`;
- J3.1 USB VBUS → NC;
- плата питается только от 12 В.

Референсное включение USBLC6 использует USB VBUS как верхнюю clamp-шину. Для предсказуемой ESD-защиты рекомендуется:

```text
J3.1 USB VBUS → U3.5
U3.5 → 100 nF → GND
USB VBUS не подключать к питанию платы
```

Текущая схема, вероятнее всего, не мешает обычной работе USB, но при ESD часть энергии может воздействовать на системную шину 3V3. До окончательного выпуска следует либо исправить включение, либо документировать его как осознанное отклонение и проверить ESD на прототипе.

## 20. OLED и M3_3

Условный контур OLED находится в области правого нижнего крепёжного отверстия. Проверять нужно не только контур платы OLED, но также:

- головку винта;
- шайбу;
- стойку;
- доступ отвёртки;
- высоту и ориентацию female J4;
- выступы пайки/разъёма на OLED-модуле.

До выпуска требуется точный footprint реального OLED-модуля с courtyard, отверстиями и keepout под крепёж. Если реальная механика подтверждает отсутствие конфликта, изменение платы не требуется.

## 21. Размер платы и разъёмы

Фактический Edge.Cuts:

```text
X: 53.2 … 145.2 мм = 92.0 мм
Y: 64.25 … 144.25 мм = 80.0 мм
```

`smartlada_rev_b_fabrication.md` указывает 91.5×79 мм. Перед заказом необходимо зафиксировать один размер во всех документах.

Разъёмы:

- J4 на PCB/схеме — female PinSocket 1×8;
- J5 — male PinHeader 1×8;
- закупочный BOM ошибочно объединяет их как одинаковые PLS-40 male;
- спецификация местами описывает J5 как 6-pin.

## 22. Firmware GPIO и Flash

Фактическая GPIO-карта платы:

| Функция | GPIO |
|---|---:|
| LAMP0 | GPIO1 |
| LAMP1 | GPIO0 |
| LAMP2 | GPIO3 |
| LAMP3 | GPIO2 |
| KEY1 | GPIO23 |
| KEY2 | GPIO22 |
| KEY3 | GPIO21 |
| KEY4 | GPIO20 |

Текущий firmware использует прямую карту GPIO0…3, поэтому силовые функции будут попарно переставлены.

Необходим отдельный hardware profile Rev B:

```text
LAMP0 = GPIO1
LAMP1 = GPIO0
LAMP2 = GPIO3
LAMP3 = GPIO2
```

На плате установлен ESP32-C6-WROOM-1-N8, то есть 8 MB Flash. Текущая команда сборки проекта использует 16 MB и partition scheme N16.

До первого запуска:

- FlashSize = 8 MB;
- 8-мегабайтная partition table;
- проверенные размеры OTA и filesystem;
- отдельное имя board profile `smartlada_revB`;
- обновление GPIO в firmware и web UI.

---

# Часть IV. Необязательные правки и валидация

## 23. RF-антенна ESP32-C6

Выполнено правильно:

- keepout присутствует на всех четырёх медных слоях;
- в keepout отсутствуют компоненты и via;
- модуль расположен возле края платы;
- под основной частью модуля есть GND-via array.

Отклонение: антенная часть остаётся над FR-4 основной платы; до Edge.Cuts около 2.3 мм. Отсутствие меди уменьшает влияние, но диэлектрик всё равно изменяет настройку PCB-антенны.

Для indoor-применения текущий вариант может быть достаточен. Решение следует принимать по испытанию:

- проверить Zigbee RSSI и дальность в окончательном корпусе;
- выдержать около 15 мм до корпуса, проводов, OLED и металлического крепежа;
- проверить работу одновременно с PWM и buck;
- при недостаточном запасе вынести антенну за край либо сделать вырез платы;
- опционально добавить GND-via fence вдоль заземлённой части модуля.

## 24. USB differential pair

Полная длина от разъёма до ESP32 через U3 и R5/R6:

| Линия | Длина |
|---|---:|
| D+ | около 19.65 мм |
| D− | около 20.00 мм |
| Skew | около 0.35 мм |

Согласование длины отличное. Геометрия пары не обеспечивает подтверждённые 90 Ω differential по всей длине. Для короткого USB Full-Speed это, вероятнее всего, не вызовет проблемы.

Варианты:

- оставить как есть для прототипа;
- либо рассчитать ширину/зазор по реальному stack-up изготовителя и переразвести штатной diff-pair.

Не следует писать в документации, что 90 Ω уже обеспечены, пока нет расчёта или импеданс-контроля производителя.

## 25. Gate-цепи

Текущие 4.4–5.4 мм после Rg приемлемы. Сокращение до 1–2 мм возможно, но при PWM 30 кГц ожидаемый практический выигрыш невелик. Новая переразводка не требуется.

## 26. Выходные конденсаторы buck

Необязательные улучшения:

- GND-via непосредственно у каждой отрицательной площадки C6/C7;
- два 3V3-via непосредственно у `Cout+`;
- уменьшить избыточный массив via, если требуется пространство.

Текущая широкая медь и существующие via уже достаточны по току.

## 27. Silkscreen и технологичность

Текущий DRC не содержит прежнего предупреждения о толщине B.Silk, следовательно правка закрыта.

Структура платы:

- 4 слоя;
- F.Cu — компоненты, сигналы, силовые линии;
- In1.Cu — практически сплошной GND;
- In2.Cu — основная 3V3-плоскость;
- B.Cu — преимущественно GPIO/gate и вспомогательные сигналы;
- медь 35 µm;
- толщина около 1.6 мм;
- основные via 0.7/0.3 мм;
- глобальное tenting включено.

Эти параметры соответствуют заявленным стандартным технологическим ограничениям.

---

# Часть V. Подтверждённо хорошие решения

## 28. Что не требует переделки

- Архитектура четырёх low-side каналов.
- High-side P-MOS защита от переполюсовки.
- Последовательность J1 → F1 → Q5 → +12V.
- Одноточечное соединение PGND/GND через net-tie возле силового входа.
- Основные силовые дорожки 2–3 мм.
- Отсутствие via в токовых путях ламп.
- Сплошной In1 GND.
- Отдельный In2 3V3.
- Локальная развязка ESP32 и массив EPAD-via.
- Аппаратные gate pull-down.
- Переразведённые Rg/Rpd.
- Правильное назначение USB D−=GPIO12 и D+=GPIO13.
- Хорошее совпадение длин USB.
- RF keepout на всех слоях.
- Исправленная нумерация LED1.
- Via 0.7/0.3 мм и кольца 0.2 мм.
- Tenting переходных отверстий.
- Отсутствие требования automotive load-dump/ISO 7637, поскольку используется регулируемый indoor-БП 12 В.

---

# Часть VI. Чек-листы

## 29. Перед Gerber release

- [x] Buck полностью соединён.
- [x] C6/C7 размещены возле L1.
- [x] FB дотрассирован.
- [x] Gate-цепи Q1–Q4 переразведены.
- [x] DRC: 0 violations.
- [x] DRC: 0 unconnected.
- [x] DRC: 0 footprint errors.
- [ ] Синхронизировать LED1 symbol/library и получить ERC 0/0.
- [ ] Исправить все MPN в схеме.
- [ ] Экспортировать и вручную проверить новый BOM.
- [ ] Принять решение по WS2812B-V5.
- [ ] Принять решение по U3.5/USB VBUS.
- [ ] Проверить OLED/M3_3 по реальной механике.
- [ ] Исправить тип J4 в закупочном BOM.
- [ ] Зафиксировать J5 как 1×8 male.
- [ ] Синхронизировать размер 92×80 мм с fabrication note.
- [ ] Обновить `smartlada_rev_b_spec.md`, pinout и README.
- [ ] Refill all zones после последних изменений.
- [ ] Повторить ERC/DRC.
- [ ] Экспортировать Gerber/Excellon.
- [ ] Проверить все четыре медных слоя независимым Gerber viewer.
- [ ] Проверить drill map, NPTH/PTH и контур платы.

## 30. Перед первым включением

1. Не устанавливая ESP32 и LED1, подать 12 В с ограничением 100–200 мА.
2. Проверить отсутствие короткого замыкания 3V3/GND.
3. Измерить VOUT buck; ожидание около 3.3 В.
4. Осциллографом проверить пульсации C6 и SW overshoot.
5. Проверить правильность полярности и падение на Q5.
6. Установить ESP32 и прошить только профилем N8/8 MB.
7. Проверить USB Serial/JTAG и UART.
8. Проверить фактическую GPIO-карту без ламп.
9. Подключать лампы по одной.
10. Проверить LAMP0…LAMP3 против функций firmware.
11. Выполнить одновременный холодный старт четырёх ламп.
12. Контролировать 12 В, 3V3 и brownout ESP32.
13. Измерить VDS и температуру Q1…Q5.
14. Провести 30–60 минут на максимальной длительной нагрузке.
15. Выполнить 50–100 холодных включений.
16. Проверить Zigbee в окончательном корпусе.

## 31. Критерии успешного прототипа

- VOUT находится в допустимом диапазоне и не уходит вверх при малой нагрузке.
- Пульсации 3V3 не вызывают brownout или USB reset.
- SW не имеет опасного выброса относительно допустимого VDS внутренних ключей TPS54202.
- Все четыре лампы соответствуют логическим функциям firmware.
- Q1–Q5 не имеют недопустимого нагрева.
- F1 выдерживает повторные холодные включения.
- USB стабильно определяется и прошивает ESP32.
- Zigbee имеет требуемый запас дальности в корпусе.
- OLED и крепёж не конфликтуют физически.

---

# Часть VII. Проверенные материалы

## 32. Файлы проекта

- [`smartlada_revB/smartlada_revB.kicad_sch`](smartlada_revB/smartlada_revB.kicad_sch)
- [`smartlada_revB/smartlada_revB.kicad_pcb`](smartlada_revB/smartlada_revB.kicad_pcb)
- [`smartlada_revB/DRC.rpt`](smartlada_revB/DRC.rpt)
- [`smartlada_revB/ERC.rpt`](smartlada_revB/ERC.rpt) — файл устарел; свежая ручная проверка дала 0 errors / 1 library warning
- [`smartlada_rev_b_bom.md`](smartlada_rev_b_bom.md)
- [`smartlada_rev_b_fabrication.md`](smartlada_rev_b_fabrication.md)
- [`smartlada_rev_b_pinout.md`](smartlada_rev_b_pinout.md)
- [`smartlada_rev_b_spec.md`](smartlada_rev_b_spec.md)
- [`../README.md`](../README.md)
- `Screenshot 2026-07-29 at 15.17.33.png` — визуальная проверка buck с масштабной линейкой

## 33. Datasheet/reference

- Texas Instruments, TPS54202: <https://www.ti.com/lit/ds/symlink/tps54202.pdf>
- Espressif, ESP32-C6 PCB layout: <https://docs.espressif.com/projects/esp-hardware-design-guidelines/en/latest/esp32c6/pcb-layout-design.html>
- STMicroelectronics, USBLC6-2: <https://www.st.com/resource/en/datasheet/usblc6-2.pdf>
- Alpha & Omega Semiconductor, AOD4184A: <https://www.aosmd.com/products/mosfets/medium-voltage-mosfets-40v-400v/aod4184a>
- WORLDSEMI WS2812B-V5 product data: <https://www.tme.com/ca/en/details/ws2812b-v5/smd-colour-leds/worldsemi/>
