saschapo/smartlada/custom_pcb/smartlada_revC/silkscreen/2106_lamp_schematic_back_silkscreen_preview.png

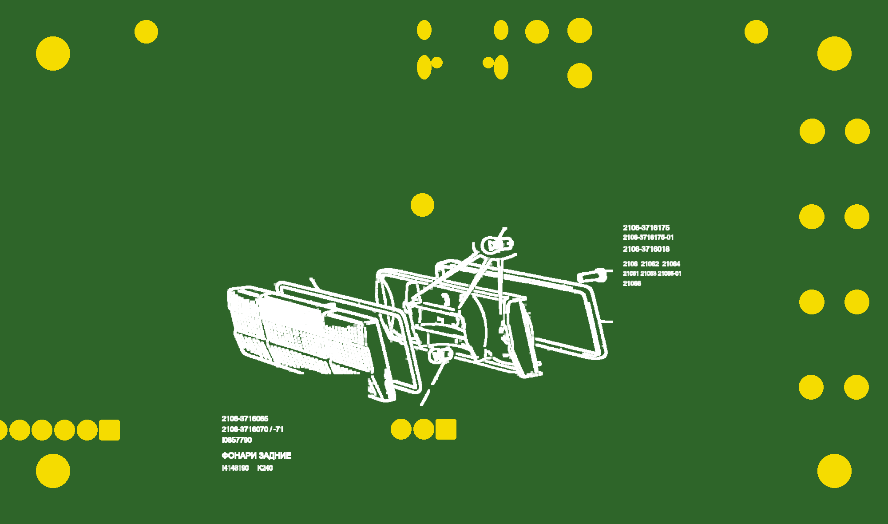
custom_pcb/smartlada_revC/silkscreen/2106_lamp_schematic_back_silkscreen_preview.png
