saschapo/smartlada/custom_pcb/smartlada_revC/silkscreen/1786289400695_default.png

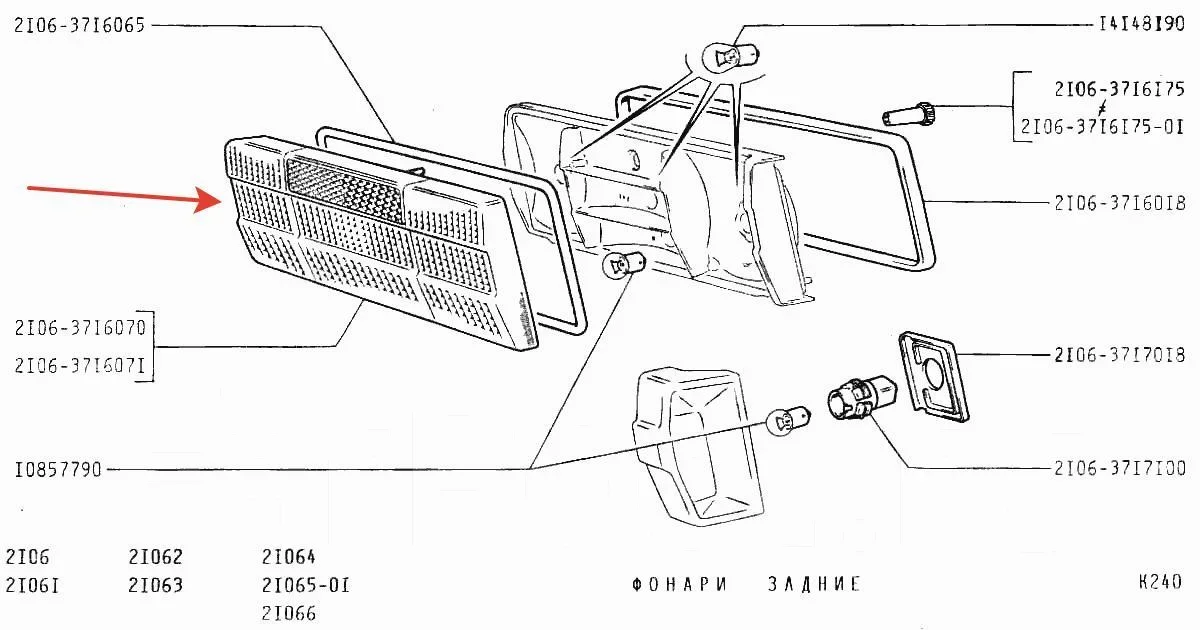
custom_pcb/smartlada_revC/silkscreen/1786289400695_default.png
