saschapo/smartlada/site/screens/anim/display.webp

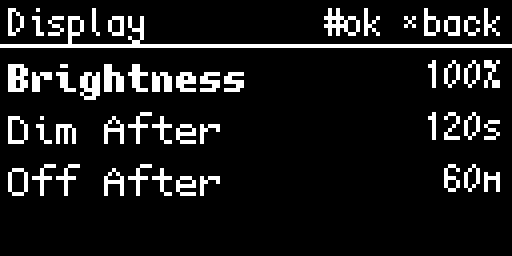
site/screens/anim/display.webp
