saschapo/smartlada/site/screens/anim/menu.webp

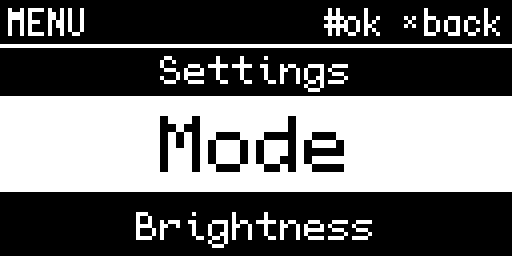
site/screens/anim/menu.webp
