saschapo/smartlada/site/screens/anim/mode.webp

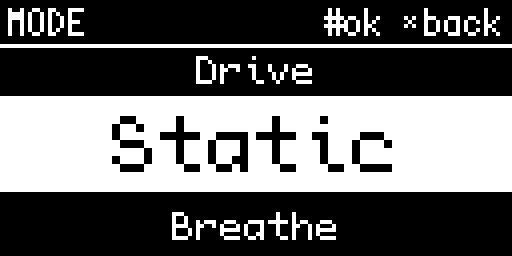
site/screens/anim/mode.webp
