saschapo/smartlada/site/screens/anim/settings.webp

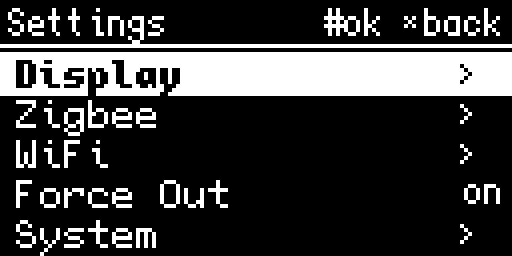
site/screens/anim/settings.webp
