saschapo/smartlada/site/screens/anim/system.webp

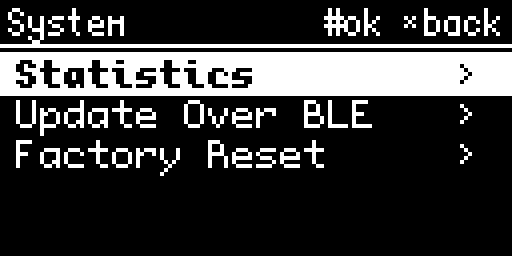
site/screens/anim/system.webp
