saschapo/smartlada/site/screens/contact.png

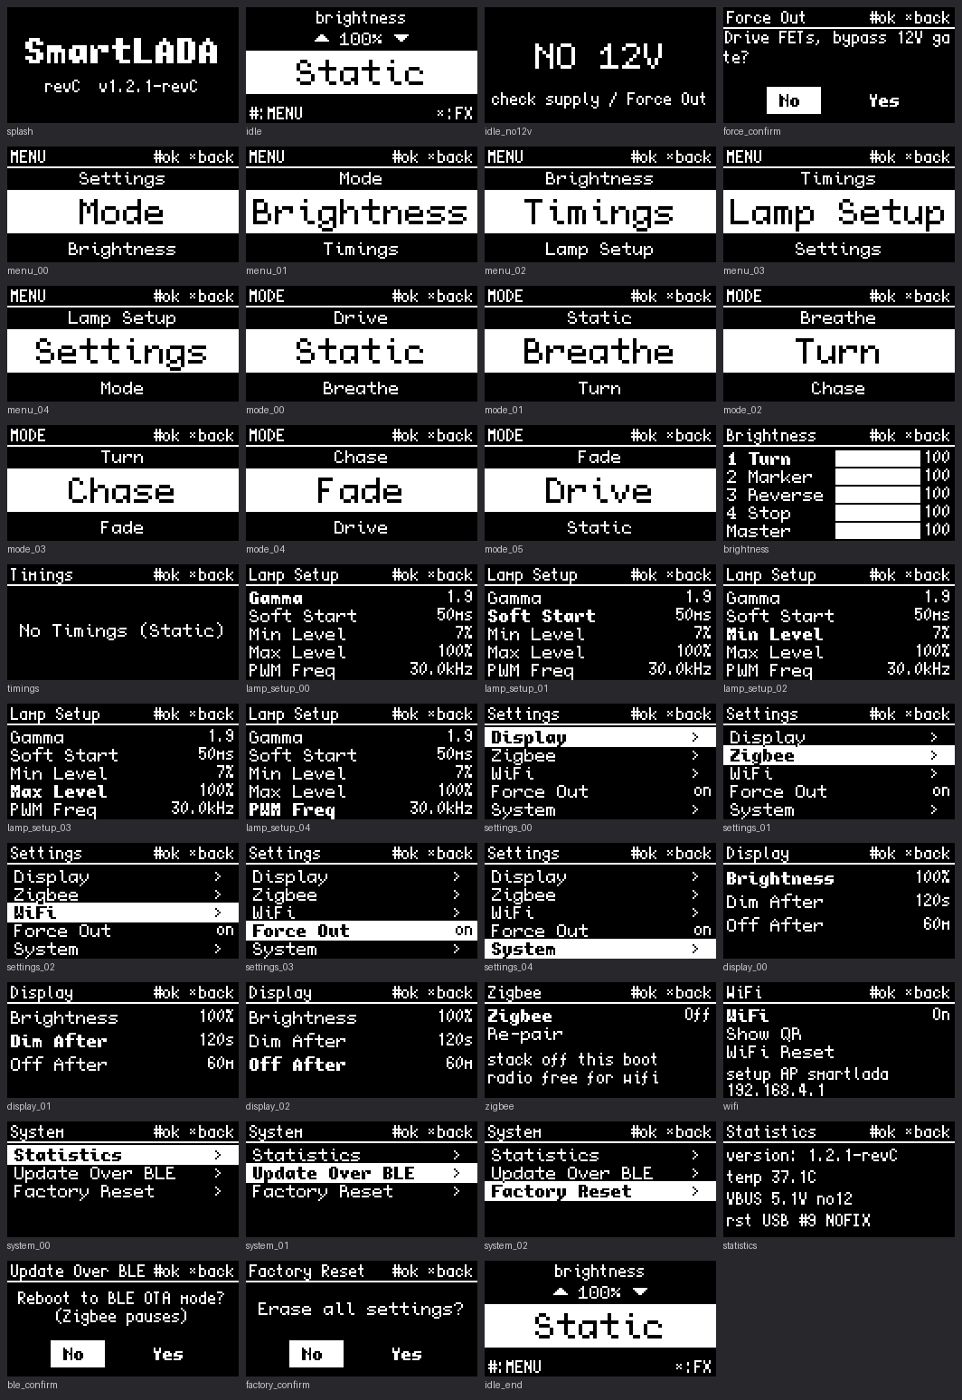
site/screens/contact.png
