saschapo/smartlada/site/screens/png/ble_confirm.png

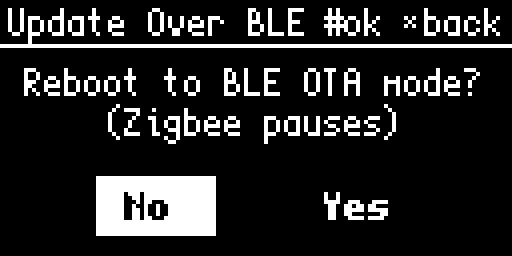
site/screens/png/ble_confirm.png
