saschapo/smartlada/site/screens/png/brightness.png

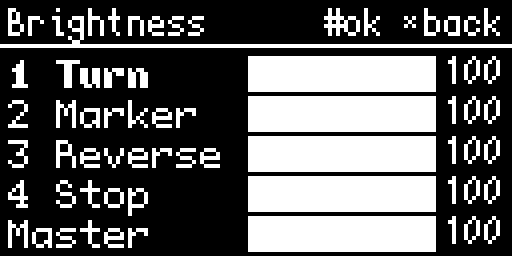
site/screens/png/brightness.png
