saschapo/smartlada/site/screens/png/factory_confirm.png

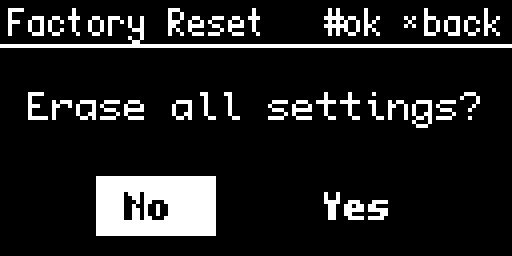
site/screens/png/factory_confirm.png
