saschapo/smartlada/site/screens/png/force_confirm.png

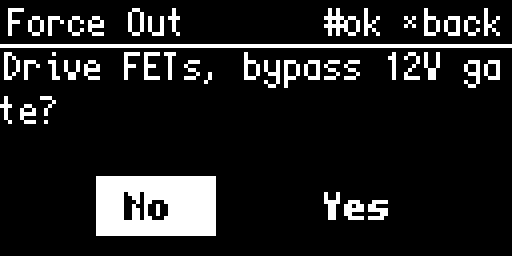
site/screens/png/force_confirm.png
