saschapo/smartlada/site/screens/png/idle.png

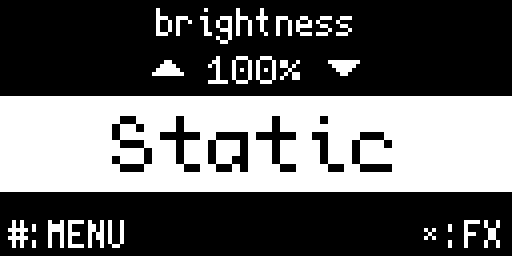
site/screens/png/idle.png
