saschapo/smartlada/site/screens/png/idle_no12v.png

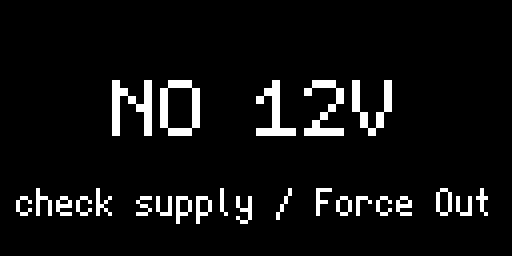
site/screens/png/idle_no12v.png
