saschapo/smartlada/site/screens/png/menu_01.png

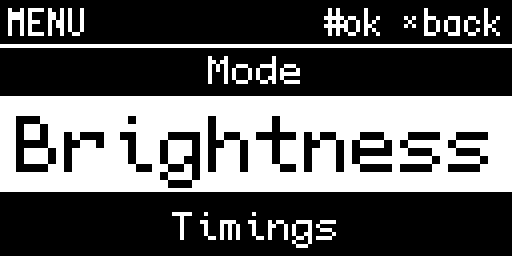
site/screens/png/menu_01.png
