saschapo/smartlada/site/screens/png/menu_02.png

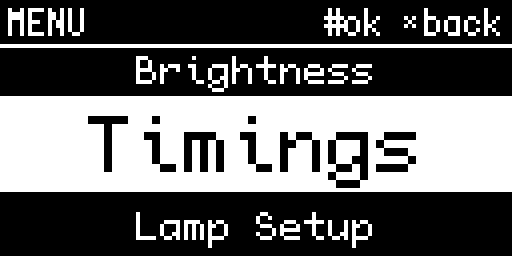
site/screens/png/menu_02.png
