saschapo/smartlada/site/screens/png/menu_03.png

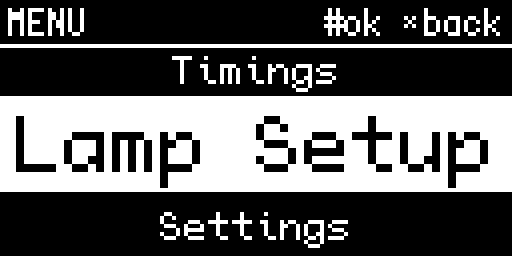
site/screens/png/menu_03.png
