saschapo/smartlada/site/screens/png/menu_04.png

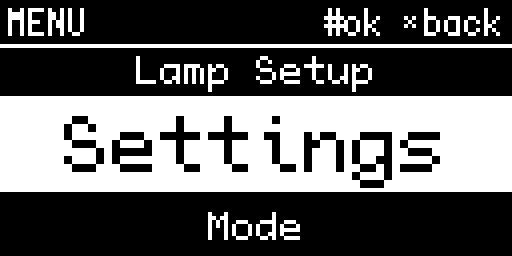
site/screens/png/menu_04.png
