saschapo/smartlada/site/screens/png/mode_01.png

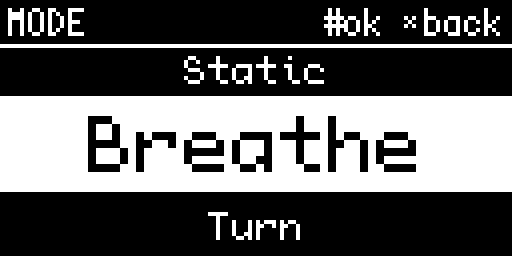
site/screens/png/mode_01.png
