saschapo/smartlada/site/screens/png/mode_02.png

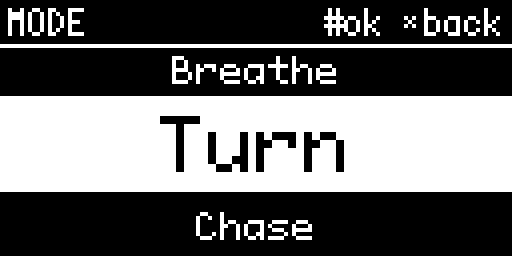
site/screens/png/mode_02.png
