saschapo/smartlada/site/screens/png/mode_03.png

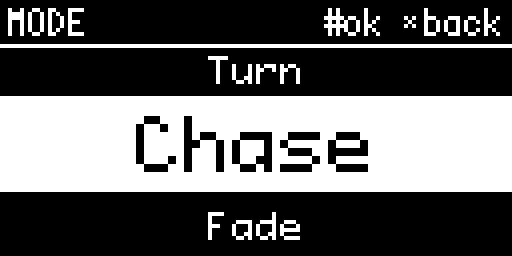
site/screens/png/mode_03.png
