saschapo/smartlada/site/screens/png/mode_04.png

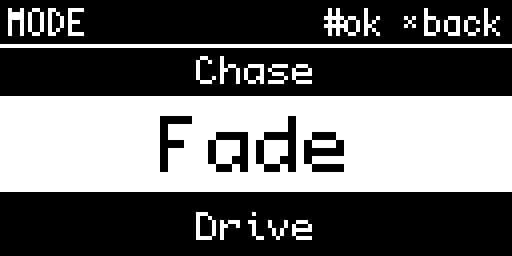
site/screens/png/mode_04.png
