saschapo/smartlada/site/screens/png/mode_05.png

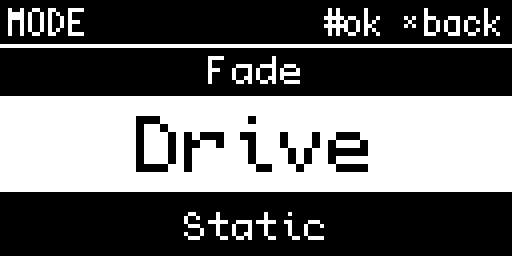
site/screens/png/mode_05.png
