saschapo/smartlada/site/screens/png/settings_01.png

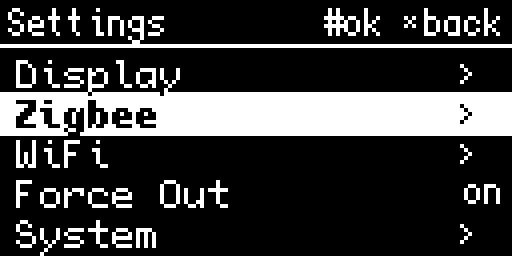
site/screens/png/settings_01.png
