saschapo/smartlada/site/screens/png/settings_02.png

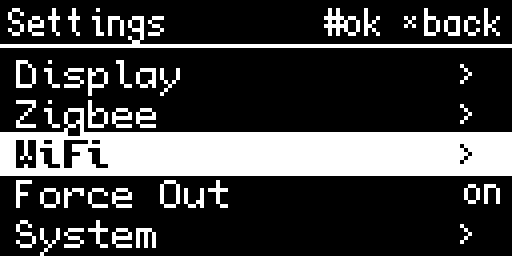
site/screens/png/settings_02.png
