saschapo/smartlada/site/screens/png/settings_03.png

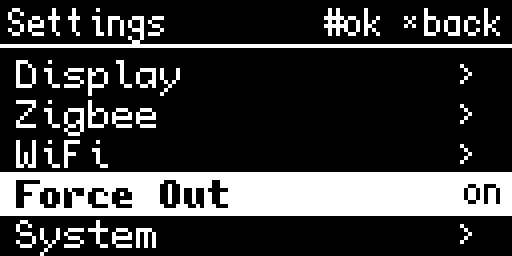
site/screens/png/settings_03.png
