saschapo/smartlada/site/screens/png/settings_04.png

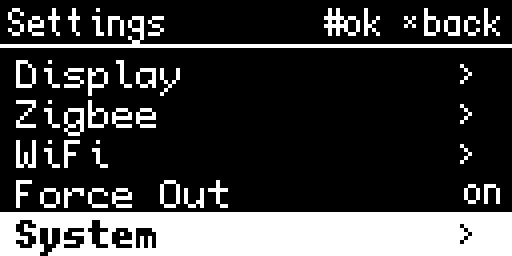
site/screens/png/settings_04.png
