saschapo/smartlada/site/screens/png/statistics.png

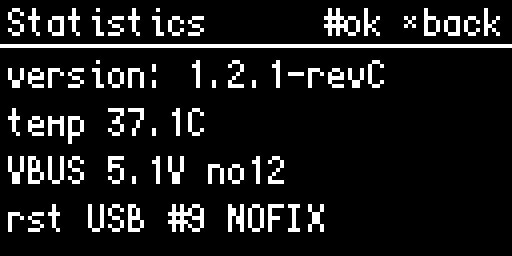
site/screens/png/statistics.png
