saschapo/smartlada/site/screens/png/system_01.png

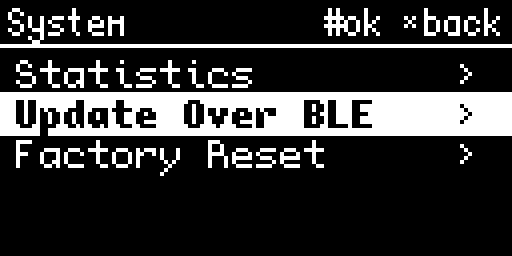
site/screens/png/system_01.png
