saschapo/smartlada/site/screens/png/system_02.png

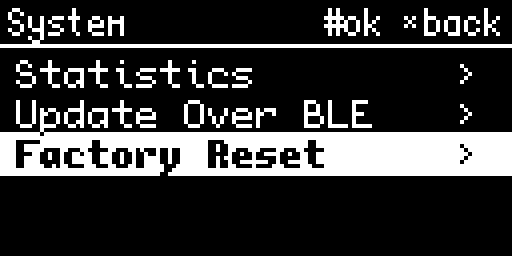
site/screens/png/system_02.png
