saschapo/smartlada/site/screens/png/timings.png

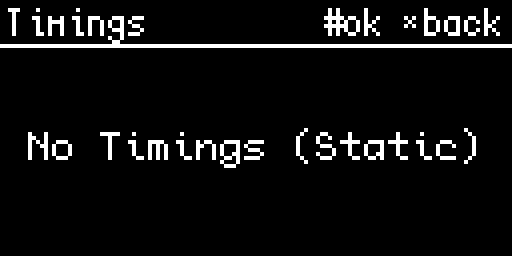
site/screens/png/timings.png
