saschapo/smartlada/site/screens/png/wifi.png

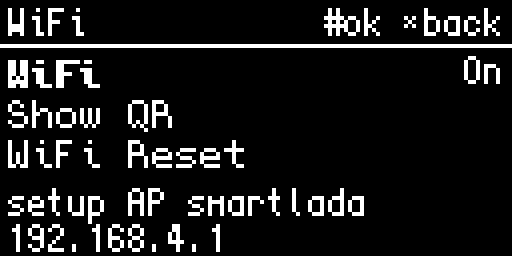
site/screens/png/wifi.png
