saschapo/smartlada/site/screens/png/zigbee.png

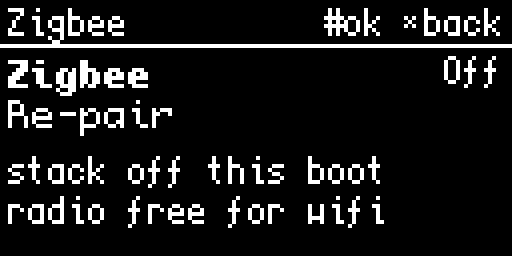
site/screens/png/zigbee.png
