saschapo/smartlada/site/source/alice-app.jpg

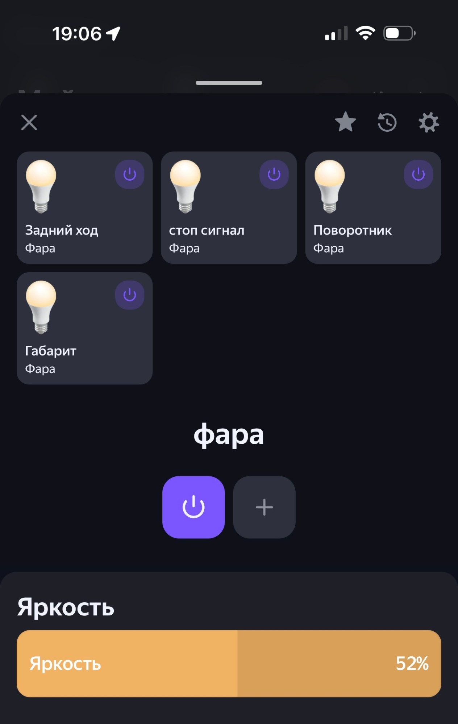
site/source/alice-app.jpg
