saschapo/smartlada/custom_pcb/smartlada_revA/BOM_work/revA/260721_platan_basket_review.md

# SmartLada Rev A — проверка корзины Platan

Дата проверки: **2026-07-21**  
Статус: компоненты подобраны, заказ не оформлялся.

## Файлы

- `260721_platan_basket.xls` — выгрузка корзины Platan. Несмотря на расширение, это TSV-текст в кодировке Windows-1251, а не бинарный Excel-файл.
- `260721_platan_basket_кириллица.xlsx` — пересобранная корзина с восстановленной кириллицей, числовыми ценами и формулами сумм.
- `smartlada_revA.kicad_sch` / `smartlada_revA.kicad_pcb` — актуальные схема и плата, по которым проверялась совместимость.

В исправленной корзине **18 строк**, итоговая стоимость на момент выгрузки — **1 937,24 ₽**.

## Что было сделано

1. Определена исходная кодировка Windows-1251 и восстановлена кириллица.
2. Корзина пересобрана в настоящий XLSX.
3. Суммы строк и общий итог заменены формулами.
4. Номиналы, корпуса и количество сопоставлены с актуальной схемой и PCB Rev A.
5. Проверены спорные позиции C1, C2, J2 и держатель F1.
6. J2 переделан в KiCad под шаг 2,54 мм; после изменения выполнен DRC.

## Принятые решения

### C2 — 100 нФ, 25 В, X7R, 0805

Выбран `GRM21BR71E104KA01L`.

C2 подключён между защищённой шиной `+12V` и GND после Q5. Для текущего применения от регулируемого комнатного блока питания 12 В номинал 25 В принят. Исходные 50 В были консервативным запасом, а не функциональной необходимостью.

Ограничение: это решение не переносится на автомобильную сеть и другие источники с выбросами напряжения. Перед вводом в эксплуатацию полезно измерить напряжение БП при включении и без нагрузки.

### C1 — 100 мкФ, 25 В

В корзину добавлен `EEUFR1E101` Panasonic:

- 100 мкФ, 25 В;
- корпус Ø6,3 × 11,2 мм;
- шаг выводов 2,50 мм;
- полярный THT-конденсатор.

Он соответствует footprint `CP_Radial_D6.3mm_P2.50mm` и принят без замечаний.

### J2 — переделан под 2,54 мм

Выбран `DG308-2.54-05P-14-00ZH`:

- пять контактов;
- шаг 2,54 мм;
- допустимый ток 6 А по UL / 8 А по IEC;
- провод 0,5–1,0 мм².

Для сравнения с нагрузкой платы:

- J2.1 (`+12V`, общий провод ламп) — около 3,33 А постоянно;
- J2.2…J2.5 — около 0,83 А на канал.

В схеме и PCB J2 уже заменён на пятиконтактный footprint 2,54 мм `TerminalBlock_Phoenix_MPT-0,5-5-2.54_1x05_P2.54mm_Horizontal`. Он используется как геометрический эквивалент выбранного DG308. Разводка обновлена.

Результат DRC от **2026-07-21 15:09**:

- 0 нарушений;
- 0 неподключённых площадок;
- 0 ошибок footprint.

Для общего провода `+12V` рекомендуется сечение 0,75–1,0 мм². Перед заказом PCB следует проверить ориентацию входа проводов и реальную геометрию корпуса по образцу или чертежу DG308; 3D-модель Phoenix является приближением.

### F1 — S1052-1 оставлен с текущим footprint

Параметры S1052-1:

- предохранитель 5,2 × 20 мм;
- держатель 4 А / 250 В;
- корпус 24 × 10 × 11 мм;
- расстояние между выводами 22,4 мм;
- ширина вывода 1,2 мм.

Текущий footprint Schurter 0031.8201 имеет расстояние площадок 22,5 мм и отверстия 1,3 мм.

Принятое решение: **footprint не менять**. Разница шага 0,1 мм несущественна и компенсируется гибкостью выводов. Корпус помещается в существующую область компонента.

Остаётся небольшой сборочный риск: отверстие 1,3 мм под номинальный вывод 1,2 мм может оказаться плотным с учётом допусков и металлизации. Для прототипной партии это приемлемо. Если держатель не войдёт свободно, отверстия можно аккуратно расширить вручную; после этого нужно проверить сохранность площадок и хорошо пропаять выводы.

Номинальная нагрузка платы около 3,33 А, то есть держатель 4 А используется примерно на 83% рейтинга. Запас небольшой, но достаточный для текущих четырёх ламп. Увеличение мощности нагрузки без повторной проверки не допускается.

## Остальные позиции

- `AOD4184A` и `AOD4185` совпадают с проектом.
- `TPS54202DDCR` совпадает с проектом и корпусом SOT-23-6/TSOT-23-6.
- `CDRH6D28NP-100NC` соответствует L1 10 мкГн.
- `SS14-E3/61T` соответствует D1: 1 А, 40 В, SMA/DO-214AC.
- Резисторы 13,7 кОм, 100 Ом и 100 кОм выбраны в корпусе 0805.
- C3/C4 выбраны 10 мкФ, 50 В, X7R, 1210.
- C5 выбран 100 нФ, X7R, 0603.
- C6/C7 выбраны 22 мкФ, 0805; перед заказом следует ещё раз подтвердить рабочее напряжение позиции в карточке магазина.
- Предохранитель `FS-52GT-4.0/250` — медленный T4A, 5×20 мм.

## Что проверить перед заказом плат и компонентов

- Просмотреть новые Gerber после изменения J2 во внешнем viewer.
- Проверить направление ввода проводов и нумерацию контактов J2.
- Использовать для общего `+12V` провод 0,75–1,0 мм².
- На первой сборке примерить S1052-1 до пайки остальных высоких компонентов.
- Измерить реальное напряжение 12-вольтового БП при включении и без нагрузки.
- Не переносить текущий входной каскад на автомобильную сеть без отдельной защиты.
