saschapo/smartlada/custom_pcb/smartlada_revB/smartlada_rev_b_bom.md

# SmartLada Rev B — BOM (на 4 платы + запас)

Снято с разведённой платы (2026-07-25). Наличие/цены — Platan (shop.platan.ru), retail.
Модуль U1 — **AliExpress** (не Platan). NT1 — net-tie, физической детали нет.
Правило Platan: для позиций **со склада** (QUANTY>0) продают от 1 шт, MINZAKAZ в API — оптовый.

Поля для KiCad Symbol Fields Table: **MPN** (part number) и **MF** (manufacturer).

## Резисторы 0805 (после унификации номиналов)

| Value | Ref | /плата | Заказ | MPN | MF | Platan NOM | Мин |
|---|-----|---|---|-----|----|---|-----|
| 100k | R1,R2,Rpd1..4 | 6 | 30 | ERJP06F1003V | Panasonic | 2015140622 | от 1 |
| 100R | Rg1..4,R7 | 5 | 25 | RT0805BRD07100RL | Yageo | 2014970291 | от 1 |
| 10k | R4,R10,R8,R9 | 4 | 20 | ERJ6ENF1002V | Panasonic | **2014975487** | MIN 1 ✓ |
| 22k | R3 | 1 | 6 | RC0805JR-0722KL | Yageo | **2014967651** | MIN 1 ✓ |
| 0R | R5,R6 | 2 | 10 | (см. ниже) | — | — | ⚠ на Platan только катушка |

**10k/22k — решены** (нашлись MIN-1 order-in линии: Panasonic ERJ6EN 10k, Yageo RC0805JR 22k).
**0R (R5/R6):** MIN-1 линии на Platan нет. Но R5/R6 — это **0 Ω rework-перемычки** в USB-паре
(нативный USB C6 работает при прямом соединении, series-R не нужен — datasheet/§6). Поэтому:
→ **просто запаять пятачки перемычкой/каплей** (детали не нужно), либо взять 0805 0Ω из
AliExpress-набора. Покупать катушку 0R на Platan не обязательно.

## Конденсаторы

| Value | Ref | /плата | Заказ | MPN | MF | Platan NOM | Мин |
|---|-----|---|---|-----|----|---|-----|
| 100nF 0603 | C2,C5,C9 | 3 | 15 | TCC0603X7R104K250CT | CCTC | 2017412118 | склад, от 1 |
| 1µF 0603 25V | C10 | 1 | 6 | TCC0603X7R105K250CT | CCTC | 2015754477 | от 1 |
| 10µF 1210 50V | C3,C4 | 2 | 10 | GRM32ER71H106KA12L | Murata | 2014974863 | order-in 1-2д, MIN 1 |
| 22µF 1210 25V | C6,C7,C8 | 3 | 15 | GRT21BR61E226ME13L | Murata | 2015901729 | склад, от 1 |
| 100µF элко 25V | C1 | 1 | 5 | EEUFR1E101 | Panasonic | 2014982023 | от 1 |

*C2 стоит на 0805-футпринте, но 0603-корпус паяется (как в revA) — плату не трогаем.*

## Активные / индуктивность

| Part | Ref | /плата | Заказ | MPN | MF | Platan NOM | Мин |
|---|-----|---|---|-----|----|---|-----|
| N-MOSFET | Q1..Q4 | 4 | 16 | AOD4184A | A&O | 2010030452 | ⚠ MIN 13 |
| P-MOSFET | Q5 | 1 | 5 | AOD4185 | YouTai | 2017289798 | от 1 |
| Buck | U2 | 1 | 5 | TPS54202DDCR | TI | **2015708243** | от 1 |
| USB ESD | U3 | 1 | 5 | USBLC6-2SC6 | YouTai | 2015469303 | от 1 (8₽) |
| Дроссель 10µH | L1 | 1 | 5 | CDRH6D28NP-100NC | Sumida | 2014962957 | от 1 |
| RGB 5050 | LED1 | 1 | 6 | WS2812B-V5 | WorldSemi | 2016855366 | склад, от 1 |
| Модуль | U1 | 1 | 6 | ESP32-C6-WROOM-1-N16 | Espressif | **AliExpress** | long-lead |

## Разъёмы / механика

| Part | Ref | /плата | Заказ | MPN | MF | Platan NOM | Мин |
|---|-----|---|---|-----|----|---|-----|
| Клемма 2P 5.0мм | J1 | 1 | 10 | DG127-5.0-02P | Degson | 2013048522 | ⚠ MIN 10 (заказ 5д) |
| ^ альтернатива J1 | J1 | — | — | XY128V-A-2P-5.0 | NXU | 828149532 | ⚠ склад ТОЛЬКО 3 шт (мало на 4 платы) |
| Клемма 5P 2.54мм | J2 | 1 | 5 | DG308-2.54-05P | Degson | 2017108400 | от 1 |
| USB-B розетка | J3 | 1 | 5 | USBB-1J-W | NXU | 249636968 | склад |
| Гнездо 8P female (2.54) | J4 | 1 | 1×PBS-40 (резать) | PBS-40 (DS1023-1x40S21) | Connfly | 2016827819 | склад 333, от 1 |
| Гребёнка 8P male (2.54) | J5 | 1 | 1×PLS-40 (резать) | PLS-40 | KLS | 613861066 | склад 14377, от 1 |
| Кнопка тактовая 6×6 THT | SW1,SW2 | 2 | 10 | 1-1825910-0 (TE, h=7мм — низкая) | TE | 2014974669 | order-in 1-2д, MIN 1 |
| Держатель фьюза 5×20 | F1 | 1 | 5 | S1052-1 | Ruichi | 2017222701 | от 1 |
| Фьюз 4A slow 5×20 | F1 | 1 | 6 | FS-52GT-4.0/250 | Conquer | 2017285955 | от 1 |

## Наличие Platan (снято 2026-07-29, retail)

**Со склада (от 1 шт):** 100nF TCC0603 (850), 22µF GRT21 (10907), WS2812B-V5 (1551),
USB-B USBB-1J-W (5267), PLS-40/J5 (14377), J4 гнездо DS1023-1x40S21 (333).

**Под заказ 1-2 раб.дня, MIN 1** (не склад, но берут от 1): 100k, 100R, 10k, 22k, 1µF,
10µF Murata (замена!), 100µF, AOD4185, TPS54202, USBLC6, дроссель L1, DG308/J2, держатель
фьюза, кнопки 1-1825910-0.

**Требуют внимания (большой MIN или долгий лид):**
- **Q1-4 AOD4184A** — 0 склад, **MIN 13**, 3-4 дня → берём 16.
- **J1 DG127** — 0 склад, **MIN 10**, 5 дней → берём 10.
- **Фьюз FS-52GT-4.0/250** — 0 склад, **лид 1-2 НЕДЕЛИ**, MIN 2 → заказать РАНЬШЕ остального.
- **10µF Hongda HLC1210 (старый) был MIN 1000** → заменён на Murata GRM32ER71H106KA12L (MIN 1).
- **10k/22k/0R** — решены ранее (10k/22k MIN 1; 0R R5/R6 = перемычка, не покупаем).

## Не Platan
- **U1 ESP32-C6-WROOM-1-N16** — AliExpress, **ЗАКАЗАНО 5 шт** (3 шт до 8 авг 2026, 2 шт до 15 авг 2026).
  Взят N16 (16 MB), не N8 — текущая сборка под 16MB/N16 (README) корректна, отдельный 8MB-профиль НЕ нужен.
