saschapo/smartlada/custom_pcb/smartlada_revA/BOM_work/revA/electroconnect_order_260721.md

# SmartLada Rev A — заявка на изготовление плат (ЭЛЕКТРОконнект / pselectro.ru)

Дата заявки: **21.07.2026**
Документ сформирован: 21.07.2026 22:14 (ред., маска исправлена; первая версия 21:47)
Статус заявки: **на рассмотрении**

## Реквизиты

| Поле | Значение |
|---|---|
| Плательщик | Пономарев Александр Святославич |
| Получатель | Пономарев Александр Святославич |
| Способ доставки | ПВЗ СДЭК |
| Адрес получения | СДЭК, Москва, ул. Щербаковская, 20 |
| Срочность изготовления | Серийный |

## Параметры платы

| Поле | Значение |
|---|---|
| Плата | smartlada_revA |
| Тип заказа | новый |
| Количество плат | 4 |
| Размеры | 80 x 65 мм |
| Площадь платы | 0.52 дм² |
| Общая площадь | 2.08 дм² (0.52 x 4) |
| Вырезы/окна | Нет |
| Количество слоёв | 2 |
| Материал | FR4 |
| Толщина платы | 1.5 мм |
| Толщина фольги | 35 мкм (1 oz) |
| Паяльная маска | Жидкая ПМ; С двух сторон; Чёрная |
| Переходные отверстия | закрыты маской |
| Маркировка | Верх (top); Белая |
| Дата/нумерация | Нет |
| Финишное покрытие | Горячее лужение ПОС-63 (HASL) |
| Краевые разъёмы | Нет |
| Метод обработки контура | Фрезеровка |
| Электроконтроль | да |

## Инженерные заметки к заявке

**РЕШЕНО (ред. 22:14) — паяльная маска исправлена на «С двух сторон».**
В первой версии заявки (21:47) была ошибочно указана «Верх (top)»: при маске только
сверху нижний GND-полигон и THT-пады не-GND цепей (J1.1, J2.1–5, C1, F1, J3) остались бы
голой медью с зазором 0.2–0.5 мм -> риск КЗ припоем при пайке. Пользователь исправил
сторону на сайте до запуска.

**Цвет маски: чёрная (в проектных доках планировалась зелёная).** Функционально
эквивалентно; наши минимальные элементы 0.2 мм в пределах возможностей чёрной маски.
Обновлено в FABRICATION_ORDER.md.

**Сверено с проектом и совпадает:** 80x65 мм, 2 слоя, FR4, толщина 1.5 мм, фольга
35 мкм, шелк только сверху, HASL, фрезеровка контура (зазор медь-край 0.5 мм это
поддерживает), переходные закрыты маской (KiCad затентил виа — совпадает с гербером),
электроконтроль включён.

**Дрель-файлы:** отверстия d3.2 (4x M3) и d2.7 (фиксатор F1) — NPTH, отдельный файл;
проверить, что в загруженном комплекте присутствуют оба Excellon-файла (PTH и NPTH).

Комплектация деталей на 4 платы — см. `SmartLada_RevA_BOM_4boards.xlsx`.
