saschapo/smartlada/custom_pcb/smartlada_revA/BOM_work/revA/platan_order_769977.md

# SmartLada Rev A — заказ компонентов (Platan)

Магазин: Platan (shop.platan.ru)
Номер заказа: **769977**
Дата: 2026-07-21
Статус: **оплачен** (счёт действовал до 2026-07-23, оплата картой онлайн)
Комплектация: на **4 платы**

## Доставка

| Поле | Значение |
|---|---|
| Способ | Яндекс-доставка, Москва и МО |
| Адрес | Москва, Измайловское шоссе 11 |
| Оплата | картой на сайте |

## Состав

17 позиций, итог по корзине ≈ **2 453 ₽**. Полный список и количества:
- выгрузка корзины: `260721_platan_basket.xls`;
- комплектация на 4 платы с запасом: `SmartLada_RevA_BOM_4boards.xlsx`.

## Ключевые решения по этому заказу

- **C5 и C2 переведены на `TCC0603X7R104K250CT`** (0603 X7R 100 нФ 25 В, в наличии,
  от 1 шт, 7 ₽). Исходные GRM188R72A104KA35D (C5) и GRM21BR71E104KA01L (C2) были
  под заказ (0 на складе) и упирались в глюк мин.заказа на сайте («доступно N = qty+5»).
  На площадке C2 (0805) стоит 0603-корпус — осознанно, плату не меняем, gerber не трогаем.
- **Заказные позиции** (0 на складе, срок 1-5 дней): AOD4185, S1052-1, EEUFR1E101,
  RC0805, RT0805, ERJP06, L1, SS14, FS-52GT, U1, DG308, AOD4184A (мин.заказ 13).
- **Со склада** (мин. отгрузка кратна): HLC1210 (C3/C4), GRT21 (C6/C7), PLS-40 (J3),
  TCC0603 (C5/C2), DG127 (J1, всего 3 шт).

## Открытый хвост

- **J1 `DG127-5.0-02P`**: на Platan доступно только **3 шт** (дозаказ от 2700). На 4 платы
  нужно 4. Четвёртый клеммник (5.0 мм, 2 конт., винтовой — KF301-5.0-2P / MX126-5.0-2P /
  DG127-5.0) добрать в другом магазине до сборки 4-й платы.

## Связанные документы

- `electroconnect_order_260721.md` — заказ на изготовление плат (ЭЛЕКТРОконнект).
- `../../FABRICATION_ORDER.md` — подготовка к производству.
