saschapo/smartlada/site/screens/anim/lamp_setup.webp

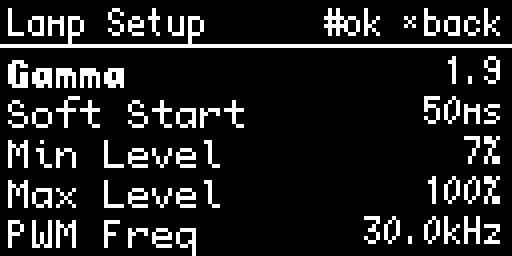
site/screens/anim/lamp_setup.webp
