saschapo/smartlada/SmartLadaC6/src/version.h

#pragma once

// SmartLada C6 firmware version. Printed to Serial at startup, returned in /status
// and shown in the web-UI header. Bump manually on significant changes.
#define FW_VERSION "0.7.0-c6"
#define FW_BUILD (__DATE__ " " __TIME__)
