saschapo/smartlada/SmartLadaRevC/src/ui/menu.cpp

#include "menu.h"
#include "ui_font.h"
#include "../display/display.h"
#include "../config/config.h"
#include "../channels/channels.h"
#include "../fx/effects.h"
#include "../input/buttons.h"
#include "../net/zigbee.h"
#include "../net/bleota.h"
#include "../net/wifinet.h"
#include "../net/radio.h"
#include "qr.h"
#include "../power/power.h"
#include "../version.h"
#include <Preferences.h>

using display::oled;

extern uint32_t g_bootCount;   // defined in the .ino (RTC-persisted boot counter)
extern uint32_t g_otaReq;      // RTC flag: set to bleota::OTA_REQ_MAGIC + reboot -> BLE OTA mode

namespace menu {

enum Screen { SC_IDLE, SC_MENU, SC_MODE, SC_BRIGHT, SC_TIMINGS, SC_LAMP,
              SC_SETTINGS, SC_DISP, SC_NET, SC_INFO, SC_FACTORY, SC_FORCE,
              SC_ZB, SC_ZBRP, SC_SYS, SC_FW, SC_QR };
static constexpr uint8_t NSCREEN = 17;

static Screen  screen = SC_IDLE;
static Screen  modeReturn = SC_MENU;     // where Mode returns to (set on entry)
static int8_t  cursor = 0;
static int8_t  screenCursor[NSCREEN] = {0};   // per-screen saved cursor (restored on return)
static bool    editing = false;
static uint8_t timMode = 0xFF;           // effect whose params the Timings screen is editing
static bool    dirty = true;
static bool    pendingSave = false;      // flush config NVS on release
static bool    pendingFxSave = false;    // flush effect params NVS on release
static uint8_t factorySel = 0;           // Factory Reset confirm: 0 = No, 1 = Yes
static uint8_t forceSel = 0;             // Force Out confirm: 0 = No, 1 = Yes
static uint8_t zbSel = 0;                // Zigbee re-pair confirm: 0 = No, 1 = Yes
static uint8_t fwSel = 0;                // "Update Over BLE" confirm: 0 = No, 1 = Yes
static uint32_t s_now = 0;

// display power management (idle dim / off)
static uint32_t lastAct = 0;
static uint8_t  powerState = 0;          // 0 = on, 1 = dim, 2 = off

// carousel slide animation
static bool     animActive = false;
static uint32_t animStart = 0;
static int8_t   animDir = 0;
static constexpr uint32_t ANIM_MS = 180;
static constexpr int16_t  CY = 37, SLOT = 24, BAND_Y = 24, BAND_H = 24;  // pages 3..5

static const char* MAIN_ITEMS[] = {"Mode", "Brightness", "Timings", "Lamp Setup", "Settings"};
static constexpr uint8_t MAIN_N = sizeof(MAIN_ITEMS) / sizeof(MAIN_ITEMS[0]);
static const Screen MAIN_TARGET[MAIN_N] = {SC_MODE, SC_BRIGHT, SC_TIMINGS, SC_LAMP, SC_SETTINGS};

// Settings sub-menu. "Force Out" opens a confirm screen (SC_SETTINGS target = handled inline).
// WiFi QR will live inside the WiFi screen (Phase 6), not as a top-level item.
static const char* SET_ITEMS[] = {"Display", "Zigbee", "WiFi", "Force Out", "System"};
static constexpr uint8_t SET_N = sizeof(SET_ITEMS) / sizeof(SET_ITEMS[0]);
static const Screen SET_TARGET[SET_N] = {SC_DISP, SC_ZB, SC_NET, SC_SETTINGS, SC_SYS};
static constexpr uint8_t FORCE_IDX = 3;   // "Force Out" (confirm before enabling)

// System sub-menu (maintenance / diagnostics).
static const char* SYS_ITEMS[] = {"Statistics", "Update Over BLE", "Factory Reset"};
static constexpr uint8_t SYS_N = sizeof(SYS_ITEMS) / sizeof(SYS_ITEMS[0]);
static const Screen SYS_TARGET[SYS_N] = {SC_INFO, SC_FW, SC_FACTORY};

static const uint8_t ARROW_UP[]   = {0x18, 0x3C, 0x7E, 0xFF};
static const uint8_t ARROW_DOWN[] = {0xFF, 0x7E, 0x3C, 0x18};

// ---------- adjust helpers ----------
// Acceleration: hold longer -> bigger step (rate is capped at ~1 frame, so speed
// past that comes from step size, keeping every jump visible).
static int accelMult() {
  uint32_t h = buttons::heldMs(buttons::UP), h2 = buttons::heldMs(buttons::DOWN);
  if (h2 > h) h = h2;
  if (h >= 3000) return 10;
  if (h >= 1200) return 3;
  return 1;
}
static void adjPct(uint8_t& v255, int dpct) {
  int p = (v255 * 100 + 127) / 255;
  p += dpct; if (p < 0) p = 0; if (p > 100) p = 100;
  v255 = (uint8_t)((p * 255 + 50) / 100);
}
static void adjInt(int32_t& v, int dir, int32_t lo, int32_t hi, int32_t step) {
  v += dir * step; if (v < lo) v = lo; if (v > hi) v = hi;
}
// off-after: 30s steps up to 1 min, then 1-min steps (0=off, 30s, 1m, 2m, ...)
static void adjOff(int32_t& v, int dir, int m) {
  for (int i = 0; i < m; i++) {
    if (dir > 0) v += (v < 60) ? 30 : 60;
    else         v -= (v <= 60) ? 30 : 60;
    if (v < 0) v = 0; if (v > 3600) v = 3600;
  }
}
static uint8_t pct(int32_t v) { return (uint8_t)((v * 100 + 127) / 255); }

// UP/DOWN adjust a 0..255 value in whole-percent steps; returns true if changed.
static bool adjPctBtn(uint8_t& v, int m) {
  bool ch = false;
  if (buttons::repeat(buttons::UP))   { adjPct(v, +m); ch = true; }
  if (buttons::repeat(buttons::DOWN)) { adjPct(v, -m); ch = true; }
  return ch;
}

static void fmtParam(const fx::Param& p, char* buf, size_t n) {
  if (p.type == fx::PT_TIME_MS)      snprintf(buf, n, "%ld.%lds", p.value / 1000, (p.value % 1000) / 100);
  else if (p.type == fx::PT_PERCENT) snprintf(buf, n, "%ld%%", (long)p.value);
  else if (p.type == fx::PT_ONOFF)   snprintf(buf, n, "%s", p.value ? "On" : "Off");
  else                               snprintf(buf, n, "%ld", (long)p.value);
}

static void printCentered(const char* s, int16_t Y) {
  int16_t bx, by; uint16_t bw, bh;
  oled.getTextBounds(s, 0, 0, &bx, &by, &bw, &bh);
  oled.setCursor((128 - (int16_t)bw) / 2 - bx, Y - by - (int16_t)bh / 2);
  oled.print(s);
}
static void printRight(const char* s, int16_t xr, int16_t yBase) {
  int16_t bx, by; uint16_t bw, bh;
  oled.getTextBounds(s, 0, 0, &bx, &by, &bw, &bh);
  oled.setCursor(xr - (int16_t)bw - bx, yBase);
  oled.print(s);
}
// A ">" chevron at the right edge marking a row that drills into a sub-screen. `y` is the
// list row's top (rows are 10 px tall); the chevron is centred vertically on the row.
static void chevron(int16_t y) {
  int16_t cx = 115, cy = y + 4;           // shifted 4 px left; 1 px trimmed top & bottom
  oled.drawLine(cx, cy - 2, cx + 2, cy, SSD1306_WHITE);
  oled.drawLine(cx + 2, cy, cx, cy + 2, SSD1306_WHITE);
}
static void header(const char* title) {
  oled.setFont(&dweep);
  oled.setTextSize(1);
  oled.setTextColor(SSD1306_WHITE);
  oled.setCursor(2, 9);
  oled.print(title);
  const char* leg = "#ok *back";
  int16_t bx, by; uint16_t bw, bh;
  oled.getTextBounds(leg, 0, 0, &bx, &by, &bw, &bh);
  oled.setCursor(126 - (int16_t)bw - bx, 9);
  oled.print(leg);
  oled.drawLine(0, 11, 127, 11, SSD1306_WHITE);
}
static void bar(int16_t x, int16_t y, int16_t w, int16_t h, uint8_t val) {
  oled.drawRect(x, y, w, h, SSD1306_WHITE);
  // Round, not truncate: Alice's 100% is ZCL 254 (not 255), so /255 truncation left the
  // fill 1 px short of full. Rounding makes 254 reach the last inner pixel.
  int16_t iw = (int16_t)(((int32_t)(w - 2) * val + 127) / 255);
  if (iw > (w - 2)) iw = w - 2;
  if (iw > 0) oled.fillRect(x + 1, y + 1, iw, h - 2, SSD1306_WHITE);
}

// ---------- carousel ----------
static int16_t slotOffset(int8_t d) { return (d == -1) ? 4 : (d == 0) ? -2 : (d == 1) ? -5 : 0; }

static void carousel(const char* title, const char* const* items, uint8_t n, int8_t sel) {
  float p = 1.0f;
  if (animActive) {
    uint32_t dt = s_now - animStart;
    if (dt >= ANIM_MS) animActive = false;
    else { float t = (float)dt / ANIM_MS; p = t * t * (3 - 2 * t); }
  }
  int16_t yshift = animActive ? (int16_t)((1.0f - p) * SLOT * animDir) : 0;

  // Big (x2) items live INSIDE the white rectangle (magnifier): the incoming /
  // settled centre (d=0) and, while animating, the outgoing centre (d=-animDir).
  int8_t bigA = 0;
  int8_t bigB = animActive ? (int8_t)(-animDir) : 0;

  // pass 1: EVERY item at x1 -- this is what shows in the black zone (an item's
  // x1 form is what emerges once it leaves the rectangle).
  oled.setFont(&orp_medium); oled.setTextSize(1); oled.setTextColor(SSD1306_WHITE);
  for (int8_t d = -2; d <= 2; d++) {
    int16_t y = CY + d * SLOT + yshift + slotOffset(d);
    if (y < 2 || y > 66) continue;
    printCentered(items[(int8_t)(((sel + d) % n + n) % n)], y);
  }

  // pass 2: big (x2) items, clipped to the band via a page-aligned snapshot so
  // they never appear in the black zone (the x1<->x2 swap is hidden by the edge).
  static uint8_t scratch[1024];
  uint8_t* buf = oled.getBuffer();
  memcpy(scratch, buf, sizeof(scratch));
  oled.fillRect(0, BAND_Y, 128, BAND_H, SSD1306_BLACK);   // clear band for the x2 draw
  oled.setFont(&orp_medium); oled.setTextSize(2); oled.setTextColor(SSD1306_WHITE);
  for (int8_t d = -2; d <= 2; d++) {
    if (d != bigA && d != bigB) continue;
    int16_t y = CY + d * SLOT + yshift + slotOffset(0);   // centre baseline
    printCentered(items[(int8_t)(((sel + d) % n + n) % n)], y);
  }
  memcpy(buf + 0 * 128, scratch + 0 * 128, 3 * 128);      // restore pages 0..2 (above band)
  memcpy(buf + 6 * 128, scratch + 6 * 128, 2 * 128);      // restore pages 6..7 (below band)

  display::invertRect(0, BAND_Y, 128, BAND_H);   // band -> white, x2 text -> black
  oled.fillRect(0, 0, 128, 12, SSD1306_BLACK);   // clip above the top line
  header(title);
}

// ---------- screens ----------
static void renderIdle() {
  // PD gating: no 12 V and not forced -> outputs are held off, tell the user why.
  if (!power::present12V() && !power::forced()) {
    oled.setFont(&orp_medium); oled.setTextSize(2); oled.setTextColor(SSD1306_WHITE);
    printCentered("NO 12V", 26);
    oled.setFont(&dweep); oled.setTextSize(1);
    printCentered("check supply / Force Out", 50);
    return;
  }
  // "brightness" caption, then the arrows + % at the top-menu-item coordinates
  oled.setFont(&dweep);
  oled.setTextSize(1);
  oled.setTextColor(SSD1306_WHITE);
  printCentered("brightness", 5);

  // One master for both layers: effect brightness, and a ceiling over the static picture.
  uint8_t bri = config::s.master;
  char pcs[8]; snprintf(pcs, sizeof(pcs), "%u%%", pct(bri));
  oled.setFont(&orp_medium);
  oled.setTextSize(1);
  oled.setTextColor(SSD1306_WHITE);
  int16_t bx, by; uint16_t bw, bh;
  oled.getTextBounds(pcs, 0, 0, &bx, &by, &bw, &bh);
  int16_t pcx = (128 - (int16_t)bw) / 2 - bx, pcy = CY - SLOT + slotOffset(-1);  // = top menu item y
  oled.setCursor(pcx, pcy - by - (int16_t)bh / 2);
  oled.print(pcs);
  oled.drawBitmap(pcx - 14, pcy - 2, ARROW_UP, 8, 4, SSD1306_WHITE);
  oled.drawBitmap(pcx + (int16_t)bw + 6, pcy - 2, ARROW_DOWN, 8, 4, SSD1306_WHITE);

  // fx name at the Mode-carousel selected coordinates (seamless *), with the
  // brightness fill on the band (name inverts at the fill boundary)
  oled.setFont(&orp_medium);
  oled.setTextSize(2);
  oled.setTextColor(SSD1306_WHITE);
  printCentered(fx::modeName(config::s.mode), CY + slotOffset(0));
  oled.drawRect(0, BAND_Y, 128, BAND_H, SSD1306_WHITE);
  int16_t fillW = (int16_t)(((int32_t)bri * 126 + 127) / 255);   // round (254 -> full)
  if (fillW > 126) fillW = 126;
  if (fillW > 0) display::invertRect(1, BAND_Y + 1, fillW, BAND_H - 2);

  oled.setFont(&dweep);
  oled.setTextSize(1);
  oled.setTextColor(SSD1306_WHITE);
  oled.setCursor(2, 62);
  oled.print("#:MENU");
  printRight("*:FX", 126, 62);
}

// one list row: bold when selected, inverted when editing (replaces the frame)
static void row(int16_t y, bool sel, const char* label, const char* value,
                bool hasBar, uint8_t barVal, int16_t barX = 62, int16_t barW = 47,
                int16_t valR = 126,     // valR: right edge of the value, pulled in where
                                        // a scroll arrow shares the margin (Timings)
                int16_t valL = -1) {    // valL >= 0: left-align the value there instead, so a
                                        // barless row starts where the bars start
  oled.setFont(sel ? &orp_bold : &orp_medium);
  oled.setTextSize(1);
  oled.setTextColor(SSD1306_WHITE);
  oled.setCursor(2, y + 8);
  oled.print(label);
  if (hasBar) bar(barX, y, barW, 9, barVal);   // barX/barW per screen (Brightness vs Timings)
  oled.setFont(&dweep);
  oled.setTextColor(SSD1306_WHITE);
  if (valL >= 0) { oled.setCursor(valL, y + 7); oled.print(value); }
  else           printRight(value, valR, y + 7);
  if (sel && editing) display::invertRect(0, y - 1, 128, 11);
}

static void renderBright() {
  header("Brightness");
  if (config::s.mode != 0) {                       // animation: one common bar (= master)
    bar(8, 23, 112, 16, config::s.master);
    oled.setFont(&orp_medium);
    oled.setTextSize(2);
    oled.setTextColor(SSD1306_WHITE);
    char b[8]; snprintf(b, sizeof(b), "%u%%", pct(config::s.master));
    printCentered(b, 52);
    return;
  }
  const char* lab[5] = {"1 Turn", "2 Marker", "3 Reverse", "4 Stop", "Master"};
  uint8_t val[5] = {config::s.staticBri[0], config::s.staticBri[1],
                    config::s.staticBri[2], config::s.staticBri[3], config::s.master};
  for (uint8_t i = 0; i < 5; i++) {
    char v[6]; snprintf(v, sizeof(v), "%u", pct(val[i]));
    row(14 + i * 10, i == cursor, lab[i], v, true, val[i]);   // default barX=62, barW=47
  }
}

static void renderTimings() {
  header("Timings");
  if (config::s.mode == 0) {
    oled.setFont(&orp_medium);
    oled.setTextSize(1);
    oled.setTextColor(SSD1306_WHITE);
    printCentered("No Timings (Static)", 36);
    return;
  }
  const fx::Effect& e = fx::EFFECTS[config::s.mode - 1];
  // Rows are 12 px from y=14, so four fit above the 64 px edge. Chase has more items than
  // that (5 params + Reset), so scroll a window that keeps the cursor inside it.
  static constexpr uint8_t ROWS = 4;
  const uint8_t nItems = e.nparams + 1;
  // Sticky window: it only moves when the cursor would leave it, so walking back up the list
  // does not drag the view along -- the screen holds still until the cursor reaches its top
  // row. Persists between frames, then is clamped in case the effect (and nItems) changed.
  // MARGIN keeps one row visible past the cursor, so the list starts moving BEFORE the cursor
  // reaches an edge -- that motion is what tells the user there is more, without waiting for
  // them to hit the end. At the very ends the clamp wins and the cursor does reach the edge.
  static constexpr int MARGIN = 1;
  static uint8_t first = 0;
  int f = first;
  if (cursor - MARGIN < f)             f = cursor - MARGIN;
  if (cursor + MARGIN > f + ROWS - 1)  f = cursor + MARGIN - ROWS + 1;
  if (nItems <= ROWS)                  f = 0;
  else if (f > nItems - ROWS)          f = nItems - ROWS;
  if (f < 0)                           f = 0;
  first = (uint8_t)f;

  for (uint8_t i = first; i < nItems && i < first + ROWS; i++) {
    int16_t y = 14 + (int16_t)(i - first) * 12;
    if (i < e.nparams) {
      const fx::Param& p = e.params[i];
      const bool isSwitch = (p.type == fx::PT_ONOFF);   // no bar: "On"/"Off" says it all
      uint8_t fill = (!isSwitch && p.max > p.min)
          ? (uint8_t)((int32_t)(p.value - p.min) * 255 / (p.max - p.min)) : 0;
      char v[16]; fmtParam(p, v, sizeof(v));
      row(y, i == cursor, p.name, v, !isSwitch, fill, 51, 44, 118,
          isSwitch ? 51 : -1);                                    // bar clear of long labels
                                                                 // ("Fade Out"), value clear
                                                                 // of the scroll arrows
    } else {                                            // action row: Reset To Defaults
      bool sel = (i == cursor);
      oled.setFont(sel ? &orp_bold : &orp_medium);
      oled.setTextSize(1);
      oled.setTextColor(SSD1306_WHITE);
      oled.setCursor(4, y + 8);
      oled.print("Reset To Defaults");
      if (sel) display::invertRect(0, y - 1, 128, 11);
    }
  }
  // more-above / more-below markers, right edge, clear of the value bars
  if (first > 0)                oled.drawBitmap(120, 15, ARROW_UP, 8, 4, SSD1306_WHITE);
  if (first + ROWS < nItems)    oled.drawBitmap(120, 58, ARROW_DOWN, 8, 4, SSD1306_WHITE);
}

static void renderLamp() {
  header("Lamp Setup");
  const char* lab[5] = {"Gamma", "Soft Start", "Min Level", "Max Level", "PWM Freq"};
  for (uint8_t i = 0; i < 5; i++) {
    char v[10];
    switch (i) {
      case 0:  snprintf(v, sizeof(v), "%u.%u", config::s.gammaX10 / 10, config::s.gammaX10 % 10); break;
      case 1:  snprintf(v, sizeof(v), "%ums", config::s.softMs); break;
      case 2:  snprintf(v, sizeof(v), "%u%%", config::s.minLvl); break;
      case 3:  snprintf(v, sizeof(v), "%u%%", config::s.maxLvl); break;
      default:
        if (config::s.pwmFreq >= 1000)
          snprintf(v, sizeof(v), "%u.%ukHz", config::s.pwmFreq / 1000, (config::s.pwmFreq % 1000) / 100);
        else
          snprintf(v, sizeof(v), "%uHz", config::s.pwmFreq);
    }
    row(14 + i * 10, i == cursor, lab[i], v, false, 0);
  }
}

static void renderSettings() {
  header("Settings");
  for (uint8_t i = 0; i < SET_N; i++) {
    int16_t y = 14 + i * 10;
    bool sel = (i == cursor);
    oled.setFont(sel ? &orp_bold : &orp_medium);
    oled.setTextSize(1);
    oled.setTextColor(SSD1306_WHITE);
    oled.setCursor(4, y + 8);
    oled.print(SET_ITEMS[i]);
    if (i == FORCE_IDX) {                 // toggle state on the right (no drill-down chevron)
      oled.setFont(&dweep);
      printRight(power::forced() ? "on" : "off", 126, y + 7);
    } else {
      chevron(y);                         // drills into a sub-screen
    }
    if (sel) display::invertRect(0, y - 1, 128, 11);
  }
}

static void renderSys() {
  header("System");
  for (uint8_t i = 0; i < SYS_N; i++) {
    int16_t y = 14 + i * 10;
    bool sel = (i == cursor);
    oled.setFont(sel ? &orp_bold : &orp_medium);
    oled.setTextSize(1);
    oled.setTextColor(SSD1306_WHITE);
    oled.setCursor(4, y + 8);
    oled.print(SYS_ITEMS[i]);
    chevron(y);                           // all System items drill into a sub-screen
    if (sel) display::invertRect(0, y - 1, 128, 11);
  }
}

static void renderFactory() {
  header("Factory Reset");
  oled.setFont(&orp_medium);
  oled.setTextSize(1);
  oled.setTextColor(SSD1306_WHITE);
  printCentered("Erase all settings?", 26);
  oled.setFont(&orp_bold);
  // No
  if (factorySel == 0) oled.fillRect(24, 44, 30, 15, SSD1306_WHITE);
  oled.setTextColor(factorySel == 0 ? SSD1306_BLACK : SSD1306_WHITE);
  oled.setCursor(31, 55); oled.print("No");
  // Yes
  if (factorySel == 1) oled.fillRect(74, 44, 34, 15, SSD1306_WHITE);
  oled.setTextColor(factorySel == 1 ? SSD1306_BLACK : SSD1306_WHITE);
  oled.setCursor(80, 55); oled.print("Yes");
}

static void renderForce() {
  header("Force Out");
  oled.setFont(&dweep);
  oled.setTextSize(1);
  oled.setTextColor(SSD1306_WHITE);
  printCentered("Drive FETs, bypass 12V gate?", 22);
  oled.setFont(&orp_bold);
  oled.setTextSize(1);
  if (forceSel == 0) oled.fillRect(24, 44, 30, 15, SSD1306_WHITE);
  oled.setTextColor(forceSel == 0 ? SSD1306_BLACK : SSD1306_WHITE);
  oled.setCursor(31, 55); oled.print("No");
  if (forceSel == 1) oled.fillRect(74, 44, 34, 15, SSD1306_WHITE);
  oled.setTextColor(forceSel == 1 ? SSD1306_BLACK : SSD1306_WHITE);
  oled.setCursor(80, 55); oled.print("Yes");
}

static void renderDisplay() {
  header("Display");
  const char* lab[3] = {"Brightness", "Dim After", "Off After"};
  for (uint8_t i = 0; i < 3; i++) {
    char v[10];
    if (i == 0)       snprintf(v, sizeof(v), "%u%%", pct(config::s.dispBri));
    else if (i == 1)  { if (config::s.dimSec) snprintf(v, sizeof(v), "%us", config::s.dimSec); else strcpy(v, "off"); }
    else {
      uint16_t os = config::s.offSec;
      if (!os)            strcpy(v, "off");
      else if (os < 60)   snprintf(v, sizeof(v), "%us", os);        // 30s
      else if (os % 60)   snprintf(v, sizeof(v), "%u.5m", os / 60); // e.g. 90s -> 1.5m
      else                snprintf(v, sizeof(v), "%um", os / 60);
    }
    row(15 + i * 13, i == cursor, lab[i], v, false, 0);   // no bars in Display
  }
}

// Wi-Fi screen: three actions plus the live state, so the switch, the QR and the network
// name are all visible without drilling further.
static const char* NET_ITEMS[] = {"WiFi", "Show QR", "WiFi Reset"};
static constexpr uint8_t NET_N = 3;

static const char* netStateText() {
  switch (wifinet::state()) {
    case wifinet::CONNECTING: return "joining";
    case wifinet::ONLINE:     return "online";
    case wifinet::AP:         return "setup AP";
    default:                  return "off";
  }
}

static void renderNet() {
  header("WiFi");
  for (uint8_t i = 0; i < NET_N; i++) {
    char v[10]; v[0] = 0;
    if (i == 0) snprintf(v, sizeof(v), "%s", wifinet::enabled() ? "On" : "Off");
    row(14 + i * 10, i == cursor, NET_ITEMS[i], v, false, 0);
  }
  oled.setFont(&dweep);
  oled.setTextColor(SSD1306_WHITE);
  char l[26];
  const char* name = (wifinet::state() == wifinet::AP) ? wifinet::apSsid() : wifinet::staSsid();
  snprintf(l, sizeof(l), "%s %s", netStateText(), name[0] ? name : "-");
  oled.setCursor(2, 54); oled.print(l);
  if (wifinet::state() == wifinet::ONLINE || wifinet::state() == wifinet::AP) {
    snprintf(l, sizeof(l), "%s", wifinet::ip().toString().c_str());
    oled.setCursor(2, 63); oled.print(l);
  }
}

// Full-screen QR. In setup-AP mode it encodes the Wi-Fi join string, so a phone camera joins
// the device's own network; once online it encodes the UI address instead.
static void renderQr() {
  char payload[80], cap[24];
  // Once a phone is associated the join code is useless -- show the address to open instead.
  bool joinMode = (wifinet::state() == wifinet::AP) && (wifinet::apClients() == 0);
  if (joinMode) {
    qr::joinString(payload, sizeof(payload), wifinet::apSsid(), wifinet::apPass());
    snprintf(cap, sizeof(cap), "%s", wifinet::apSsid());
  } else {
    IPAddress a = wifinet::ip();
    snprintf(payload, sizeof(payload), "http://%s", a.toString().c_str());
    snprintf(cap, sizeof(cap), "%s", a.toString().c_str());
  }
  oled.setFont(&dweep);
  oled.setTextColor(SSD1306_WHITE);
  oled.setCursor(2, 12); oled.print(joinMode ? "join:" : "open:");
  oled.setCursor(2, 24); oled.print(cap);
  if (joinMode) { oled.setCursor(2, 36); oled.print(wifinet::apPass()); }
  oled.setCursor(2, 62); oled.print("* back");
  if (!qr::draw(payload, 95, 32, 2)) printCentered("QR too long", 50);
}

static void renderStub(const char* t, const char* msg) {
  header(t);
  oled.setFont(&orp_medium);
  oled.setTextColor(SSD1306_WHITE);
  printCentered(msg, 36);
}

// Live device diagnostics: firmware id, SoC die temperature, VBUS/PD state, and the
// last reset reason + boot count (BROWNOUT + climbing count = a cold-boot reboot loop).
static void renderInfo() {
  header("Statistics");
  oled.setFont(&dweep);
  oled.setTextSize(1);
  oled.setTextColor(SSD1306_WHITE);
  char l[24];
  uint16_t vb = power::vbusMv();
  oled.setCursor(2, 22); oled.print("version: " FW_VERSION);
  snprintf(l, sizeof(l), "temp %.1fC", temperatureRead());
  oled.setCursor(2, 34); oled.print(l);
  snprintf(l, sizeof(l), "VBUS %u.%uV %s", vb / 1000, (vb % 1000) / 100, power::good() ? "PD12" : "no12");
  oled.setCursor(2, 46); oled.print(l);
  snprintf(l, sizeof(l), "rst %s #%lu %s", power::resetReason(), (unsigned long)g_bootCount,
           zb::colorFixActive() ? "fix" : "NOFIX");
  oled.setCursor(2, 58); oled.print(l);
}

// Zigbee network status + re-pair entry.
// Two rows: the debug switch (takes effect on reboot -- the stack has no clean shutdown) and
// re-pair. Status fills the rest of the screen.
static const char* ZB_ITEMS[] = {"Zigbee", "Re-pair"};
static constexpr uint8_t ZB_N = 2;

static void renderZb() {
  header("Zigbee");
  for (uint8_t i = 0; i < ZB_N; i++) {
    char v[8]; v[0] = 0;
    if (i == 0) snprintf(v, sizeof(v), "%s", zb::enabledPref() ? "On" : "Off");
    row(14 + i * 10, i == cursor, ZB_ITEMS[i], v, false, 0);
  }
  oled.setFont(&dweep);
  oled.setTextSize(1);
  oled.setTextColor(SSD1306_WHITE);
  char l[24];
  if (!zb::enabledOnThisBoot()) {
    oled.setCursor(2, 46); oled.print("stack off this boot");
    oled.setCursor(2, 56); oled.print("radio free for wifi");
    return;
  }
  bool up = zb::connected();
  oled.setCursor(2, 40); oled.print(up ? "state: joined" : "state: joining...");
  if (up) {
    snprintf(l, sizeof(l), "PAN 0x%04X ch%u a%04X", zb::panId(), zb::channel(), zb::shortAddr());
    oled.setCursor(2, 50); oled.print(l);
    uint8_t lqi; int8_t rssi; uint16_t par;
    if (zb::parentLink(lqi, rssi, par)) snprintf(l, sizeof(l), "LQI %u  RSSI %ddBm", lqi, rssi);
    else                                strcpy(l, "LQI --  RSSI --");
    oled.setCursor(2, 60); oled.print(l);
  }
}

static void renderFwConfirm() {
  header("Update Over BLE");
  oled.setFont(&dweep);
  oled.setTextSize(1);
  oled.setTextColor(SSD1306_WHITE);
  printCentered("Reboot to BLE OTA mode?", 20);
  printCentered("(Zigbee pauses)", 30);
  oled.setFont(&orp_bold);
  oled.setTextSize(1);
  if (fwSel == 0) oled.fillRect(24, 44, 30, 15, SSD1306_WHITE);
  oled.setTextColor(fwSel == 0 ? SSD1306_BLACK : SSD1306_WHITE);
  oled.setCursor(31, 55); oled.print("No");
  if (fwSel == 1) oled.fillRect(74, 44, 34, 15, SSD1306_WHITE);
  oled.setTextColor(fwSel == 1 ? SSD1306_BLACK : SSD1306_WHITE);
  oled.setCursor(80, 55); oled.print("Yes");
}

static void renderZbConfirm() {
  header("Re-pair");
  oled.setFont(&dweep);
  oled.setTextSize(1);
  oled.setTextColor(SSD1306_WHITE);
  printCentered("Leave network & rejoin?", 22);
  oled.setFont(&orp_bold);
  oled.setTextSize(1);
  if (zbSel == 0) oled.fillRect(24, 44, 30, 15, SSD1306_WHITE);
  oled.setTextColor(zbSel == 0 ? SSD1306_BLACK : SSD1306_WHITE);
  oled.setCursor(31, 55); oled.print("No");
  if (zbSel == 1) oled.fillRect(74, 44, 34, 15, SSD1306_WHITE);
  oled.setTextColor(zbSel == 1 ? SSD1306_BLACK : SSD1306_WHITE);
  oled.setCursor(80, 55); oled.print("Yes");
}

void render() {
  if (!dirty) return;
  dirty = false;
  oled.clearDisplay();
  oled.setTextSize(1);              // every screen starts at x1 unless it opts into x2
  switch (screen) {
    case SC_IDLE:   renderIdle(); break;
    case SC_MENU:   carousel("MENU", MAIN_ITEMS, MAIN_N, cursor); break;
    case SC_MODE: {
      static constexpr uint8_t MODE_MAX = 1 + 8;    // Static + up to 8 effects
      static const char* names[MODE_MAX];
      uint8_t n = fx::modeCount();
      if (n > MODE_MAX) n = MODE_MAX;
      for (uint8_t i = 0; i < n; i++) names[i] = fx::modeName(i);
      carousel("MODE", names, n, cursor);
      break;
    }
    case SC_BRIGHT:   renderBright(); break;
    case SC_TIMINGS:  renderTimings(); break;
    case SC_LAMP:     renderLamp(); break;
    case SC_SETTINGS: renderSettings(); break;
    case SC_DISP:     renderDisplay(); break;
    case SC_NET:      renderNet(); break;
    case SC_QR:       renderQr(); break;
    case SC_INFO:     renderInfo(); break;
    case SC_FACTORY:  renderFactory(); break;
    case SC_FORCE:    renderForce(); break;
    case SC_ZB:       renderZb(); break;
    case SC_ZBRP:     renderZbConfirm(); break;
    case SC_SYS:      renderSys(); break;
    case SC_FW:       renderFwConfirm(); break;
  }
  oled.setFont(nullptr);
  oled.display();
  if (animActive) dirty = true;
}

// ---------- power management ----------
static void applyPower(uint8_t st) {
  powerState = st;
  if (st == 0)      { display::power(true);  display::setBrightness(config::s.dispBri); dirty = true; }
  else if (st == 1) { display::power(true);  display::setBrightness(3); }   // ~1%
  else              { display::power(false); }
}
static void updatePower(uint32_t now) {
  uint32_t idle = now - lastAct;
  uint8_t want = 0;
  if (config::s.offSec && idle >= (uint32_t)config::s.offSec * 1000UL)       want = 2;
  else if (config::s.dimSec && idle >= (uint32_t)config::s.dimSec * 1000UL)  want = 1;
  if (want != powerState) applyPower(want);
}

// ---------- navigation ----------
static void go(Screen s) {
  screenCursor[screen] = cursor;
  screen = s;
  cursor = screenCursor[s];
  editing = false;
  animActive = false;
  if (s == SC_MODE) cursor = config::s.mode;
  if (s == SC_FACTORY) factorySel = 0;
  if (s == SC_FORCE) forceSel = 0;             // default to No
  if (s == SC_ZBRP)  zbSel = 0;                // default to No
  if (s == SC_FW)    fwSel = 0;                // default to No
  dirty = true;
}
static void slide(int8_t dir, uint8_t n) {
  cursor = (int8_t)(((cursor + dir) % n + n) % n);
  animActive = true; animStart = s_now; animDir = dir;
  dirty = true;
}

void update(uint32_t now) {
  using namespace buttons;
  s_now = now;

  static uint32_t s_infoTick = 0;                       // Info + idle + Zigbee show live values -> ~1 Hz
  if ((screen == SC_INFO || screen == SC_IDLE || screen == SC_ZB) && now - s_infoTick >= 1000) { s_infoTick = now; dirty = true; }
  bool up = pressed(UP), down = pressed(DOWN), ok = pressed(SEL), back = pressed(BACK);
#if UI_TFT
  // Encoder: CW = UP so values rise, but a list must step forward (DOWN) on CW. The locals
  // below drive only navigation (cursors, carousels, Yes/No); values read repeat() directly.
  { bool t = up; up = down; down = t; }
#endif
  bool act = up || down || ok || back || heldMs(UP) || heldMs(DOWN) || heldMs(SEL) || heldMs(BACK);
  if (act) lastAct = now;

  // when the panel is OFF, the first press only wakes it (consumed). When merely
  // dimmed the UI is still visible, so let the press act normally (updatePower
  // below restores full brightness the same frame).
  if ((up || down || ok || back) && powerState == 2) { applyPower(0); return; }

  int m = accelMult();

  switch (screen) {
    case SC_IDLE:                              // one master in both layers (a ceiling in static)
      if (adjPctBtn(config::s.master, m)) { pendingSave = true; dirty = true; }
      if (ok)   go(SC_MENU);
      if (back) { modeReturn = SC_IDLE; go(SC_MODE); }   // *:FX (returns to idle)
      break;

    case SC_MENU:
      if (up)   slide(-1, MAIN_N);
      if (down) slide(+1, MAIN_N);
      if (ok)   { if (MAIN_TARGET[cursor] == SC_MODE) modeReturn = SC_MENU; go(MAIN_TARGET[cursor]); }
      if (back) go(SC_IDLE);
      break;

    case SC_MODE: {
      uint8_t n = fx::modeCount();
      if (up)   slide(-1, n);
      if (down) slide(+1, n);
      if (ok)   { config::s.mode = cursor; config::save(); go(modeReturn); }
      if (back) go(modeReturn);
      break;
    }

    case SC_BRIGHT:
      if (config::s.mode != 0) {
        if (adjPctBtn(config::s.master, m)) { pendingSave = true; dirty = true; }  // effect brightness
        if (back || ok) go(SC_MENU);
      } else if (!editing) {
        if (up)   { cursor = (cursor + 5 - 1) % 5; dirty = true; }
        if (down) { cursor = (cursor + 1) % 5; dirty = true; }
        if (ok)   { editing = true; dirty = true; }
        if (back) go(SC_MENU);
      } else {
        if (cursor < 4) {                                    // per-lamp static level
          if (adjPctBtn(config::s.staticBri[cursor], m)) {
            config::s.lampOn |= (1 << cursor);               // editing a channel enables it
            pendingSave = true; dirty = true;
          }
        } else {                                             // Master row = the ceiling
          if (adjPctBtn(config::s.master, m)) { pendingSave = true; dirty = true; }
        }
        if (ok || back) { editing = false; dirty = true; }
      }
      break;

    case SC_TIMINGS: {
      // Snapshot mode once: the Zigbee task can change config::s.mode at any instant (Alice picks
      // a different effect). Deriving e/nItems and the param access from a single snapshot keeps
      // them consistent within this frame; notifyExternalChange() redraws with the new mode next.
      uint8_t tmode = config::s.mode;
      if (tmode == 0) { editing = false; timMode = 0xFF; if (back || ok) go(SC_MENU); break; }
      // An edit belongs to ONE effect. If the mode switched under us, cancel it even when the
      // cursor is still a valid index for the new effect -- otherwise a held UP would keep
      // adjusting (e.g. Chase Step -> Breathe Period) without the user ever opening that editor.
      if (tmode != timMode) { timMode = tmode; if (editing) { editing = false; dirty = true; } }
      fx::Effect& e = fx::EFFECTS[tmode - 1];
      uint8_t nItems = e.nparams + 1;              // params + "Reset To Defaults"
      if (cursor >= nItems) { cursor = 0; editing = false; }
      // If the mode changed under us, cursor may now point past this effect's params (or at the
      // Reset row, or the effect may have none, e.g. Drive: params==nullptr). Never dereference
      // e.params[cursor] as a Param unless it is a real, in-range param slot.
      if (editing && (!e.params || cursor >= e.nparams)) { editing = false; dirty = true; }
      if (!editing) {
        if (up)   { cursor = (cursor + nItems - 1) % nItems; dirty = true; }
        if (down) { cursor = (cursor + 1) % nItems; dirty = true; }
        if (ok) {
          if (cursor == e.nparams) { fx::resetParams(tmode); fx::saveParams(); dirty = true; }
          else if (e.params && e.params[cursor].type == fx::PT_ONOFF) {
            fx::Param& p = e.params[cursor];       // a switch has nothing to dial: OK flips it
            p.value = p.value ? 0 : 1;             // in place, with no edit mode to confirm
            pendingFxSave = true; dirty = true;
          }
          else                     { editing = true; dirty = true; }
        }
        if (back) go(SC_MENU);
      } else {
        fx::Param& p = e.params[cursor];
        int32_t v = p.value;
        if (repeat(UP))   { adjInt(v, +1, p.min, p.max, p.step * m); p.value = v; pendingFxSave = true; dirty = true; }
        if (repeat(DOWN)) { adjInt(v, -1, p.min, p.max, p.step * m); p.value = v; pendingFxSave = true; dirty = true; }
        if (ok || back) { editing = false; dirty = true; }
      }
      break;
    }

    case SC_LAMP:
      if (!editing) {
        if (up)   { cursor = (cursor + 5 - 1) % 5; dirty = true; }
        if (down) { cursor = (cursor + 1) % 5; dirty = true; }
        if (ok)   { editing = true; dirty = true; }
        if (back) go(SC_MENU);
      } else {
        bool ch = false; int32_t v = 0;
        switch (cursor) {
          case 0: v = config::s.gammaX10;
            if (repeat(UP))   { adjInt(v, +1, 10, 30, 1 * m); ch = true; }
            if (repeat(DOWN)) { adjInt(v, -1, 10, 30, 1 * m); ch = true; }
            if (ch) { config::s.gammaX10 = v; channels::setCalib(config::s.gammaX10, config::s.minLvl, config::s.maxLvl); }
            break;
          case 1: v = config::s.softMs;
            if (repeat(UP))   { adjInt(v, +1, 0, 3000, 50 * m); ch = true; }
            if (repeat(DOWN)) { adjInt(v, -1, 0, 3000, 50 * m); ch = true; }
            if (ch) { config::s.softMs = v; channels::setSoftMs(config::s.softMs); }
            break;
          case 2: v = config::s.minLvl;
            if (repeat(UP))   { adjInt(v, +1, 0, 50, 1 * m); ch = true; }
            if (repeat(DOWN)) { adjInt(v, -1, 0, 50, 1 * m); ch = true; }
            if (ch) { config::s.minLvl = v; channels::setCalib(config::s.gammaX10, config::s.minLvl, config::s.maxLvl); }
            break;
          case 3: v = config::s.maxLvl;
            if (repeat(UP))   { adjInt(v, +1, 50, 100, 1 * m); ch = true; }
            if (repeat(DOWN)) { adjInt(v, -1, 50, 100, 1 * m); ch = true; }
            if (ch) { config::s.maxLvl = v; channels::setCalib(config::s.gammaX10, config::s.minLvl, config::s.maxLvl); }
            break;
          default: v = config::s.pwmFreq;          // PWM Freq applied on exit (re-attach is heavy)
            if (repeat(UP))   { adjInt(v, +1, 100, 30000, 500 * m); ch = true; }
            if (repeat(DOWN)) { adjInt(v, -1, 100, 30000, 500 * m); ch = true; }
            if (ch) config::s.pwmFreq = v;
            break;
        }
        if (ch) { pendingSave = true; dirty = true; }
        if (ok || back) {
          if (cursor == 4) channels::setFreq(config::s.pwmFreq);
          editing = false; dirty = true;
        }
      }
      break;

    case SC_SETTINGS:
      if (up)   { cursor = (cursor + SET_N - 1) % SET_N; dirty = true; }
      if (down) { cursor = (cursor + 1) % SET_N; dirty = true; }
      if (ok) {
        if (cursor == FORCE_IDX) {
          if (power::forced()) { power::setForce(false); dirty = true; }  // turning OFF is safe -> immediate
          else                 go(SC_FORCE);                              // turning ON needs confirmation
        } else go(SET_TARGET[cursor]);
      }
      if (back) go(SC_MENU);
      break;

    case SC_FACTORY:
      if (up || down) { factorySel ^= 1; dirty = true; }
      if (back) go(SC_SYS);
      if (ok) {
        if (factorySel == 1) {                     // Yes -> wipe config + leave Zigbee, reboot
          Preferences pr; pr.begin("smartlada", false); pr.clear(); pr.end();
          delay(50);
          zb::factoryReset();                      // erases Zigbee NVS + reboots
          ESP.restart();                           // fallback if factoryReset() returned
        } else go(SC_SYS);
      }
      break;

    case SC_DISP:
      if (!editing) {
        if (up)   { cursor = (cursor + 3 - 1) % 3; dirty = true; }
        if (down) { cursor = (cursor + 1) % 3; dirty = true; }
        if (ok)   { editing = true; dirty = true; }
        if (back) go(SC_SETTINGS);
      } else if (cursor == 0) {
        if (adjPctBtn(config::s.dispBri, m)) {
          if (config::s.dispBri < 3) config::s.dispBri = 3;   // display brightness >= ~1%
          display::setBrightness(config::s.dispBri);
          pendingSave = true; dirty = true;
        }
        if (ok || back) { editing = false; dirty = true; }
      } else if (cursor == 1) {
        int32_t v = config::s.dimSec;
        if (repeat(UP))   { adjInt(v, +1, 0, 120, 5 * m); config::s.dimSec = v; pendingSave = true; dirty = true; }
        if (repeat(DOWN)) { adjInt(v, -1, 0, 120, 5 * m); config::s.dimSec = v; pendingSave = true; dirty = true; }
        if (ok || back) { editing = false; dirty = true; }
      } else {
        int32_t v = config::s.offSec;
        if (repeat(UP))   { adjOff(v, +1, m); config::s.offSec = v; pendingSave = true; dirty = true; }
        if (repeat(DOWN)) { adjOff(v, -1, m); config::s.offSec = v; pendingSave = true; dirty = true; }
        if (ok || back) { editing = false; dirty = true; }
      }
      break;

    case SC_NET:                              // WiFi is a top-level Settings item
      if (up)   { cursor = (cursor + NET_N - 1) % NET_N; dirty = true; }
      if (down) { cursor = (cursor + 1) % NET_N; dirty = true; }
      if (ok) {
        // Turning Wi-Fi on hands the radio over and reboots; turning it off gives it back to
        // Zigbee. There is no "both" -- see radio.h.
        if (cursor == 0)      radio::setMode(wifinet::enabled() ? radio::ZIGBEE : radio::WIFI);
        else if (cursor == 1) go(SC_QR);
        else                  wifinet::resetWifi();   // AP name/password back to defaults
        dirty = true;
      }
      if (back) go(SC_SETTINGS);
      break;
    case SC_QR:                               // full-screen QR; any key returns
      if (back || ok || up || down) go(SC_NET);
      break;
    case SC_INFO:                             // Statistics lives under System
      if (back || ok) go(SC_SYS);
      break;

    case SC_FW:                               // "Update Over BLE" confirm -> reboot to OTA mode
      if (up || down) { fwSel ^= 1; dirty = true; }
      if (back) go(SC_SYS);
      if (ok) {
        if (fwSel == 1) { g_otaReq = bleota::OTA_REQ_MAGIC; delay(50); ESP.restart(); }
        else go(SC_SYS);
      }
      break;

    case SC_SYS:
      if (up)   { cursor = (cursor + SYS_N - 1) % SYS_N; dirty = true; }
      if (down) { cursor = (cursor + 1) % SYS_N; dirty = true; }
      if (ok)   go(SYS_TARGET[cursor]);
      if (back) go(SC_SETTINGS);
      break;

    case SC_ZB:
      if (up)   { cursor = (cursor + ZB_N - 1) % ZB_N; dirty = true; }
      if (down) { cursor = (cursor + 1) % ZB_N; dirty = true; }
      if (ok) {
        if (cursor == 0) zb::setEnabled(!zb::enabledPref());   // stores + reboots
        else             go(SC_ZBRP);
      }
      if (back) go(SC_SETTINGS);
      break;

    case SC_ZBRP:
      if (up || down) { zbSel ^= 1; dirty = true; }
      if (back) go(SC_ZB);
      if (ok) {
        if (zbSel == 1) zb::factoryReset();   // leave network + reboot -> rejoin
        else go(SC_ZB);
      }
      break;

    case SC_FORCE:
      if (up || down) { forceSel ^= 1; dirty = true; }
      if (back) go(SC_SETTINGS);
      if (ok) {
        if (forceSel == 1) power::setForce(true);   // confirmed -> enable debug override
        go(SC_SETTINGS);
      }
      break;
  }

  bool released = (heldMs(UP) == 0 && heldMs(DOWN) == 0);
  if (pendingSave && released)   { config::save();   pendingSave = false; }
  if (pendingFxSave && released) { fx::saveParams(); pendingFxSave = false; }
  updatePower(now);
}

void begin() { screen = SC_IDLE; cursor = 0; dirty = true; lastAct = millis(); powerState = 0; }

void notifyExternalChange() { dirty = true; }   // Zigbee/network wrote config::s -> redraw

// Full-screen OTA banner. The main loop calls this (and nothing else) while a BLE OTA is
// running, so effects/menu/report-back are frozen -- fewer things compete with the transfer.
void showUpdating(uint8_t pct) {
  display::power(true);
  oled.clearDisplay();
  oled.setFont(&orp_medium);
  oled.setTextSize(2);
  oled.setTextColor(SSD1306_WHITE);
  printCentered("UPDATING", 20);
  char b[8]; snprintf(b, sizeof(b), "%u%%", pct);
  printCentered(b, 42);
  oled.setFont(&dweep);
  oled.setTextSize(1);
  printCentered("keep power on", 60);
  oled.display();
  dirty = true;   // force a normal redraw once OTA ends and the loop resumes
}

void showOtaIdle() {
  display::power(true);
  oled.clearDisplay();
  oled.setFont(&orp_medium);
  oled.setTextSize(2);
  oled.setTextColor(SSD1306_WHITE);
  printCentered("BLE OTA", 18);
  oled.setFont(&dweep);
  oled.setTextSize(1);
  printCentered("Zigbee paused - flash now", 40);
  printCentered("any key: exit", 56);
  oled.display();
  dirty = true;
}

}  // namespace menu
