saschapo/smartlada/sketches/Ec11Tft24Test/checkmark_ok_64_64_28f.h

#ifndef CHECKMARK_OK_64_64_28F_H
#define CHECKMARK_OK_64_64_28F_H

// Animation: checkmark-ok 64×64 28f
// Size: 64x64, Frames: 28

#include <Arduino.h>

static const unsigned char checkmark_ok_64_64_28f_frames[28][512] PROGMEM = {
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
};

static int checkmark_ok_64_64_28f_frame = 0;

#endif // CHECKMARK_OK_64_64_28F_H
