saschapo/smartlada/SmartLadaRevC/src/ui/menu.h

#pragma once
#include <Arduino.h>

// Menu / UI state machine. update() consumes button events and mutates settings;
// render() redraws only when something changed (keeps the panel static -> no
// tearing). The lamp animation runs independently of the display.
namespace menu {

void begin();
void update(uint32_t now);
void render();
void notifyExternalChange();   // force a redraw after Zigbee/network changed config::s
void showUpdating(uint8_t pct);// full-screen "UPDATING" during a BLE OTA (loop is frozen)
void showOtaIdle();            // "BLE OTA" idle banner while waiting for a transfer

}  // namespace menu
